LewisTrundle/tactihelm-l5project/timelog.md

# Timelog

* Tactihelm - Adding Haptic Feedback to a Cycling Helmet for Cyclist Safety
* LEWIS TRUNDLE
* 2469635T
* Stephen Brewster

## Week 1 [18/09/2023] - 7 hours
### 19 Sep 23
* *2.5 hours* Started conducting research.
### 20 Sep 23
* *3 hours* Continued with research.
### 21 Sep 23
* *1.5 hours* Continued with research.

## Week 2 [25/09/23] - 10 hours
### 25 Sep 23
* *3.5 hours* Continued with research.
### 26 Sep 23
* *3.5 hours* Continued with research.
### 28 Sep 23
* *1.5 hours* Continued with research.
### 29 Sep 23
* *1.5 hours* First supervisor meeting.

## Week 3 [02/10/23] - 5.5 hours
### 02 Oct 23
* *1 hour* Started constructing the Arduino parts.
### 05 Oct 23
* *1 hour* Structuring project repo.
### 08 Oct 23
* *3.5 hours* Constructing the circuit.

## Week 4 [09/10/23] - 21 hours
### 09 Oct 23
* *7 hours* Created an initial app to Bluetooth control motors on circuit.
### 10 Oct 23
* *1 hours*  Supervisor meeting.
* *1.5 hours* Continued working on app.
### 11 Oct 23
* *1.5 hours* Housekeeping.
### 12 Oct 23
* *4 hours* Setting up Expo app for bluetooth permissions.
### 13 Oct 23
* *6 hours* Connecting the bike radar to react native app via Bluetooth.

## Week 5 [16/10/23] - 29.5 hours
### 16 Oct 23
* *4 hours* Continuing to connect bike radar to react native app.
* *2.5 hours* Creating user survey.
### 17 Oct 23
* *1 hour* Supervisor meeting
* *1 hour* Continuing user survey.
### 18 Oct 23
* *2.5 hours* Finalised user survey.
### 19 Oct 23
* *4.5 hours* Started creating react native app to connect to bluetooth devices.
### 20 Oct 23
* *2 hours* Connecting both devices to app.
* *2 hours* General app work.
### 21 Oct 23
* *4.5 hours* General app work.
### 22 Oct 23
* *5.5 hours* General app work.

## Week 6 [23/10/23] - 17.5 hours
### 23 Oct 23
* *5.5 hours* General app work.
### 24 Oct 23
* *2 hours* Started interim report.
### 27 Oct 23
* *3 hours* General app work.
### 28 Oct 23
* *3 hours* General app work.
* *2 hours* Circuit construction.
### 29 Oct 23
* *2 hours* General app work.

## Week 7 [30/10/23] - 14.5 hours
### 30 Oct 23
* *1 hour* General app work.
* *4 hours* Started on introduction for interim report.
### 31 Oct 23
* *1 hour* Supervisor meeting.
* *1.5 hours* User survey work.
* *1.5 hours* General app work.
### 01 Nov 23
* *2.5 hours* Interim report work.
### 02 Nov 23
* *3 hours* Interim report work.

## Week 8 [06/11/23] - 14 hours
### 06 Nov 23
* *3.5 hours* Interim report work.
### 07 Nov 23
* *0.5 hours* Interim report work.
### 08 Nov 23
* *5 hours* Analysing user survey.
### 09 Nov 23
* *2 hours* Interim report work.
* *1 hours* Refactoring code on app.
### 11 Nov 23
* *2 hours* Continued refactoring code on app.

## Week 9 [13/11/23] - 9.5 hours
### 15 Nov 23
* *4 hours* General app work.
### 16 Nov 23
* *2.5 hours* More general app work.
### 17 Nov 23
* *3 hours* Interim report.

## Week 10 [20/11/23] - 19 hours
### 20 Nov 23
* *5 hours* Interim report.
### 21 Nov 23
* *1.5 hours* Supervisor meeting and prep.
* *2.5 hours* Interim report.
### 22 Nov 23
* *3 hours* Interim report.
### 23 Nov 23
* *3.5 hours* Interim report.
### 24 Nov 23
* *3.5 hours* Interim report.

## Week 11 [27/11/23] - 17 hours
### 28 Nov 23
* *5.5 hours* Interim report.
### 01 Dec 23
* *3.5 hours* Interim report.
### 02 Dec 23
* *6 hours* Interim report.
### 03 Dec 23
* *2 hours* Interim report.

## Week 12 [04/12/23] - 33.5 hours
### 04 Dec 23
* *5 hours* Interim report.
### 05 Dec 23
* *2.5 hours* Interim report.
### 06 Dec 23
* *6.5 hours* Interim report.
### 07 Dec 23
* *6.5 hours* Interim report.
### 08 Dec 23
* *3.5 hours* Interim report.
### 09 Dec 23
* *3 hours* Interim report.
### 10 Dec 23
* *6.5 hours* Interim report.

## Week 13 [11/12/23] - 21 hours
### 11 Dec 23
* *3.5 hours* Interim report.
### 12 Dec 23
* *6 hours* Interim report.
### 13 Dec 23
* *6 hours* Interim report.
### 14 Dec 23
* *4.5 hours* Interim report.
### 04 Dec 23
* *1 hours* Interim report.

## Week 14 [08/01/24] - 16.5 hours
### 08 Jan 24
* *1.5 hours* Housekeeping.
### 09 Jan 24
* *1 hours* Lab-study prep.
### 11 Jan 24
* *6 hours* Updating Arduino-code.
### 12 Jan 24
* *5 hours* Updating Arduino-code.
* *3 hours* Lab-study planning.

## Week 15 [15/01/24] - 14 hours
### 15 Jan 24
* *2 hours* Updating app to work with arduino code
### 18 Jan 24
* *3 hours* Lab-study planning.
### 19 Jan 24
* *5 hours* App work.
### 21 Jan 24
* *4 hours* Lab-study planning

## Week 16 [22/01/24] - 7 hours
### 22 Jan 24
* *2 hours* Lab-study planning.
### 26 Jan 24
* *5 hours* Lab-study planning.

## Week 17 [29/01/24] - 13.5 hours
### 29 Jan 24
* *3 hours* Lab-study planning.
### 01 Feb 24
* *4.5 hours* Lab-study planning.
### 04 Feb 2024
* *6 hours* Lab-study planning.

## Week 18 [05/02/24] - 12.5 hours
### 05 Feb 2024
* *4 hours* Lab-study planning.
### 06 Feb 2024
* *1.5 hours* Conducting lab-study.
* *1 hours* Supervisor meeting.
### 07 Feb 2024
* *3 hours* Conducting lab-study.
### 08 Feb 2024
* *2 hours* Conducting lab-study.
### 09 Feb 2024
* *3 hours* Conducting lab-study.

## Week 19 [12/02/24] - 1.5 hours
### 16 Feb 2024
* *1.5 hours* Conducting lab-study.

## Week 20 [19/02/24] - 18 hours
### 19 Feb 2024
* *3 hours* Conducting lab-study.
* *3 hours* Started analysing results.
### 21 Feb 2024
* *3 hours* Conducting lab-study.
* *3 hours* Started planning user study.
### 23 Feb 2024
* *6 hours* Coding infrastructure for user study.

## Week 21 [26/02/24] - 21 hours
### 27 Feb 2024
* *3 hours* Conducting lab-study.
### 28 Feb 2024
* *4 hours* Conducting lab-study.
### 29 Feb 2024
* *6 hours* Continued with analysis of lab-study results
### 02 Feb 2024
* *8 hours* Further analysis of lab-study.

## Week 22 [04/03/24] - 20 hours
Week was mainly composed of gaining ethical permission of the user-study and redesigning the helmet.

## Week 23 [11/03/24] - 32 hours
Started writing the dissertation and testing the helmet.

## Week 24 [18/03/24] - 20 hours
Conducting user study.

## Week 25 [25/03/24] - 30 hours
Writing dissertation.

## Week 26 [01/04/24] - 40 hours
Writing dissertation.

## Week 27 [08/04/24] - 40 hours
Finishing the project!
