LewisTrundle/tactihelm-l5project/user-study/task-list.md

# TactiHelm User Study: Task List

## Important Information

Before proceeding with any tasks, please ensure you have fully read the [information sheet](./information-sheet.md) and [user manual](../user-guide/user-manual.md).

- If you have opted not to record your GPS data, then please ignore any instructions regarding how to do so.
- Please remember to turn on and off the helmet, bike radar, and headpiece between usage.
- Please ensure your mobile device is near fully charged before commencing your commute.
- If you are okay doing so, for GPS data to be accurately tracked, please ensure battery saving mode on your mobile device is turned off.

## Task List

1. cycle from **work to home** using TactiHelm and performing think-aloud.
2. cycle from **home to work** using TactiHelm and performing think-aloud.
3. complete questionnaire.
4. complete interview and return equipment.
5. cycle from **home to work** normally and complete NASA-TLX questionnaire.

Task 1 will be performed the day you are given TactiHelm. Tasks 2, 3, and 4 will be performed the day after you are given TactiHelm. Task 4 can be performed any day within seven days of performing the previous tasks. Please note that this experiment is not a test of your ability.

## Task 1: First Commute

Your first task is to cycle your normal commute, from your workplace to your residence, whilst using the TactiHelm system. While performing this task, please ensure to perform a think-aloud evaluation, as previously described.

**Before proceeding with Task 1, please carefully read through the [Before Your Commute](../user-guide/user-manual.md#before-your-commute) and [After Your Commute](../user-guide/user-manual.md#after-your-commute) sections of the user manual.**

## Task 2: Second Commute

Your second task is to again cycle your normal commute, this time from your residence to your workplace, whilst using the TactiHelm system. While performing this task, please ensure to perform a think-aloud evaluation, as previously described.

**Before proceeding with Task 2, please carefully read through the [Before Your Commute](../user-guide/user-manual.md#before-your-commute) and [After Your Commute](../user-guide/user-manual.md#after-your-commute) sections of the user manual.**

Once you have completed task 2, please immediately commence to task 3.

## Task 3: Questionnaire

After completion of task 2, your third task is to complete the provided questionnaire.

- [Post-experiment Questionnaire](https://uofg.qualtrics.com/jfe/form/SV_0N8G0Wckys2GCge)

You will be asked a variety of questions regarding your two commutes. Some questions will be regarding both of them, while other questions will only be about your second commute. Please complete this questionnaire as soon as possible after your second commute, so that your experience is still fresh in your mind. Please answer truthfully and honestly.

## Task 4: Interview

After your commutes and completion of the questionnaire, you will be asked to come in for an interview with the evaluator. This will be relatively short (no more than 15 minutes) and is just for us to more deeply understand your experience with TactiHelm.

**Please bring all the equipment with you to return.**

## Task 5: Final Commute and Questionnaire

Your final task is to complete one more commute but without TactiHelm. Please complete this commute within seven days of your interview. Immediately after your commute, we would ask that you complete part of the questionnaire again.

- [Post-experiment Questionnaire](https://uofg.qualtrics.com/jfe/form/SV_0N8G0Wckys2GCge)

Make sure to select the option stating that you have just completed your final commute.
