LewisTrundle/tactihelm-l5project/user-study/participant-brief.md

# TactiHelm User Study: Participant Brief

Hi! Thank you for volunteering to be part of the user-study for our TactiHelm project.

**What is TactiHelm?**
TactiHelm is a smart-helmet which provides vibrotactile feedback to a cyclist warning them of an approaching vehicle. The helmet connects to a bike radar, attached to the rear of a users bike. The radar detects the approaching vehicle and communicates this information to the helmet. The helmet uses this information to activate the vibrational motors inside the helmet - activating them in some pattern, from which the cyclist can interpret information about the approaching vehicle.

**What am I doing here today?**
We would like to evaluate how our developed TactiHelm system works in the real-world. In-order to do this, we need the help of people, such as yourself, who are willing to try on and wear TactiHelm during an actual bike ride. By doing this, we hope to understand how effective our helmet is in warning cyclists of the presence and proximity of approaching vehicles behind them.

**What will I be doing?**
Your participation in this study will take place over the course of today, tomorrow, and one further day. Your primary task will be to simply cycle your commute between your workplace and residence as you normally would, but equipped with the TactiHelm system. We ask that during your commute, you perform a think-aloud evaluation of the system (i.e. say your thoughts out-loud). Further guidance on this will be explained shortly. After the completion of your second commute, you will be asked to complete a questionnaire, followed by a short interview with the evaluator. Finally, we will ask that you complete one more commute between your workplace and residence, without the use of TactiHelm. This will not require a think-aloud evaluation, instead we will ask you to complete a small section of the questionnaire again, after which, your participation in this study is complete, and you will be properly debriefed.

The task list is as follows:

1. cycle from **work to home** using TactiHelm and performing think-aloud.
2. cycle from **home to work** using TactiHelm and performing think-aloud.
3. complete questionnaires and interview and return equipment.
4. cycle from **home to work** normally and complete NASA-TLX questionnaire.

Task 1 will be performed the day you are given TactiHelm. Tasks 2 and 3 will be performed the day after you are given TactiHelm. Task 4 can be performed any day within seven days of performing the previous tasks. Please note that this experiment is not a test of your ability.

**What data will you collect?**

| Data Type | Reason for Collection | Collection Method | Storage | Extra Notes |
|:---:|:---:|:---:|---|---|
| Audio data captured during commute | This will be used to look for any important comments made regarding your experience with TactiHelm | Using a microphone connected to a voice recorder app on your mobile device | This will not be uploaded to anywhere other than the evaluators own personal device, for the sole purpose of analysis | |
| Answers to post-experiment questionnaire | This will be used to gather your subjective opinion on the effectiveness and usability of TactiHelm | Using the online survey platform, Qualtrics | All survey data will be stored anonymously online | |
| Audio from post-experiment interview | This will be used to gather more descriptive data from yourself regarding the effectiveness and usability of TactiHelm | Using a voice recorder app on a mobile device | This will not be uploaded to anywhere other than the evaluators own personal device, for the sole purpose of analysis | |
| GPS data captured during commute | This will be used for purposes such as visualising your commute and comparing general information, such as your commute distance, elevation profile, and time to complete | Using the Ride with GPS app on your mobile device | All GPS data will be kept within the Ride with GPS app and sharing of such data will be kept confidential. Any personal data, such as your actual location will not be used or shared | You may opt out of collection of this data, in which case, we would ask that you provide some general information yourself regarding your commute |

Please note that your data is and will remain completely confidential, and will be used solely for the purpose of this research project. You can of course request that your data be removed at any time, including during or after the study.

**What if I no longer want to participate?**
You are welcome to withdraw from the experiment at any time without prejudice. If you do so, then please note that it will not be possible for you to be debriefed about the purposes of the experiment.

**Can I ask questions?**
Yes, you are free to ask whatever questions you like during the study, and the evaluator will attempt to answer them to the best of their knowledge (so long as it won’t impose on the results of the study). If you have any further questions either during or after the study, please feel free to reach out to [2469635t@student.gla.ac.uk](mailto:2469635t@student.gla.ac.uk).

**Consent**
By continuing with this study, you acknowledge that you have read and understood the above information, and you consent to participate in this study. If you consent to participate in this study, then please follow the link to explicitly give your consent: [User Consent Form](https://uofg.qualtrics.com/jfe/form/SV_24umSauLX1uydtI).
