LewisTrundle/tactihelm-l5project/interim-report/Education Use Consent For Level 5 Projects.docx

Education Use Consent

I hereby grant my permission for my Level 5 Project Final Research Paper and Interim Report to be distributed and shown to other University of Glasgow students and staff for educational purposes.

Name: Lewis Trundle

Student Id: 2469635T

Signature:

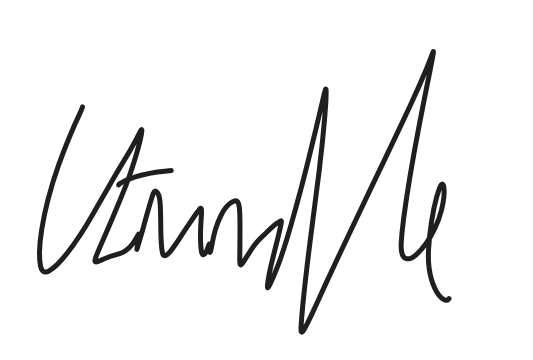
[picture p3: figure]

Date: 15/12/2023
