LewisTrundle/tactihelm-l5project/presentation/TactiHelm.pptx

## TactiHelm: A Vibrotactile Helmet for Cycling Safety

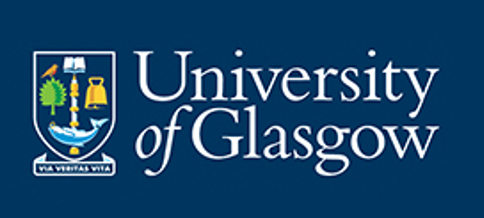
[picture p4: figure]

Lewis Trundle
Level 5 MSci Project
Supervised by Stephen Brewster

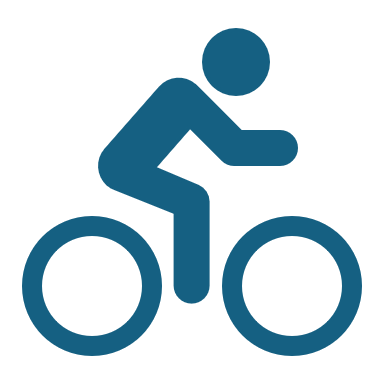
[picture p5: figure]
Bike

## Motivation

41,000 cyclists are fatally injured annually worldwide [1].
Leading cause of fatalities is collisions with other vehicles approaching from behind [2, 3].
Technologies such as bike radars provide unique alerting methods, utilising visual, auditory, and vibrotactile feedback.
Yet to be explored is how the cycling helmet can be used.

Introduction

TactiHelm System

Lab Study

User Study

Conclusions

## Objective

“Develop a vibrotactile helmet-based hazard notification system to effectively warn a cyclist of an approaching vehicle.”

What hazard information is most useful for warning cyclists?
How can this information be encoded using vibrotactile feedback?
How can this be incorporated into a helmet-based display?

Introduction

TactiHelm System

Lab Study

User Study

Conclusions

## Background Survey

An online survey was conducted (N=110) to understand the requirements of such a system.

73% had suffered an injury whilst cycling
80% said that they regularly wear a helmet
10% responded that they own a bike radar.
40% stated that close passes from cars were a top safety challenge while cycling.

Introduction

TactiHelm System

Lab Study

User Study

Conclusions

## The TactiHelm System

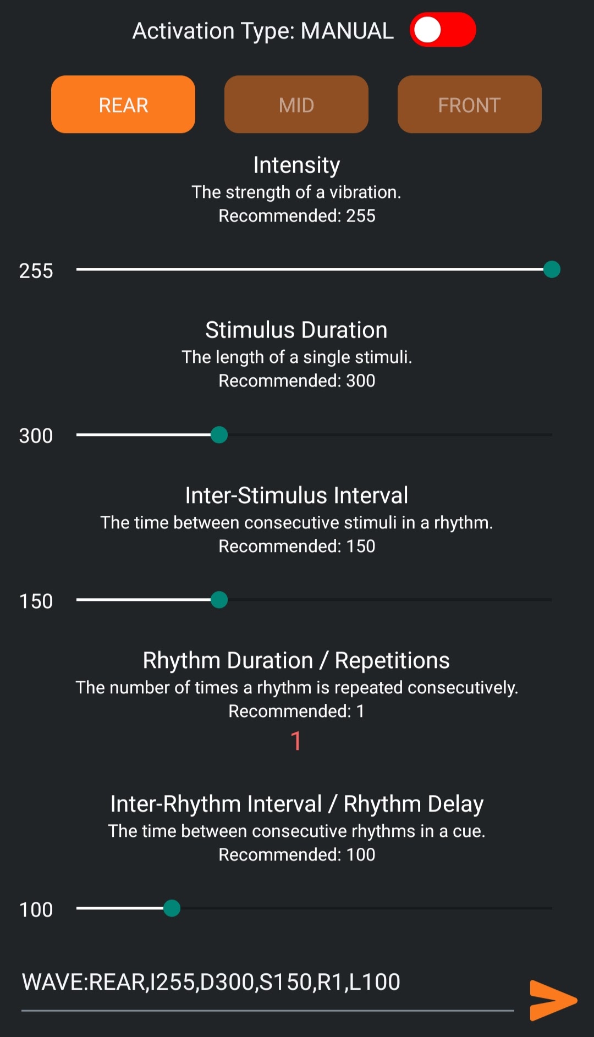
[picture p6: figure]

Controller

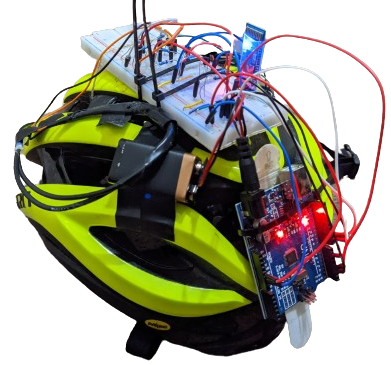
[picture p7: figure]

Helmet

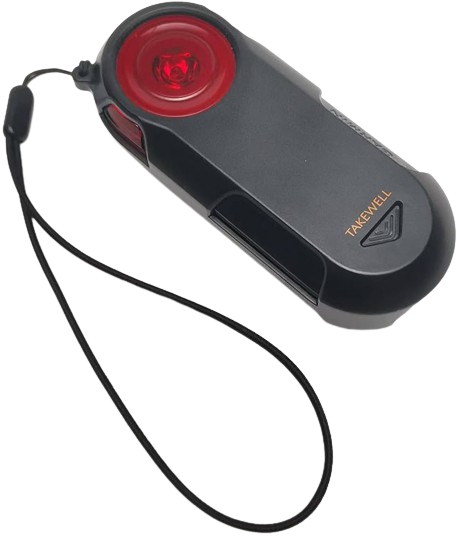
[picture p8: figure]

Bike Radar

Introduction

TactiHelm System

Lab Study

User Study

Conclusions

## Helmet

- Extends a standard cycling helmet.
- 3 internal tactile actuators along sagittal midline.
- Controlled by an Arduino microcontroller.
- Remotely operated via a mobile app.

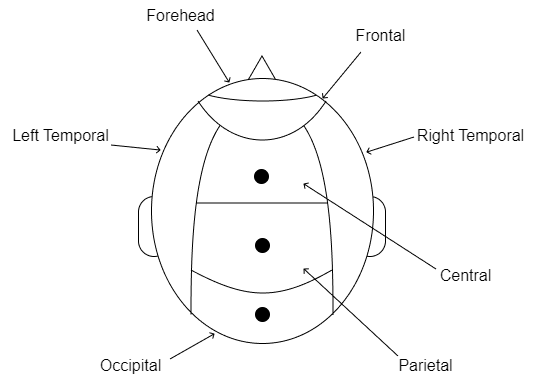
[picture p9: figure]

Introduction

TactiHelm System

Lab Study

User Study

Conclusions

## Bike Radar

- Bike radar detects approaching vehicles’ distance and speed.
- Info sent to the controller app, which calculates the following distance.
- Following distance encoded into vibrational cues: far, near and imminent.
- Following distance thresholds found through preliminary testing.

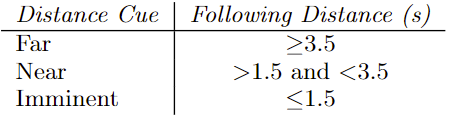
[picture p10: figure]

Introduction

TactiHelm System

Lab Study

User Study

Conclusions

## Controller

- Controller app connects to the helmet and radar – allowing communication between them.
- Parses info received from the radar into relevant instructions for the Arduino.
- Provides manual control over attributes of vibrations, such as location, intensity, etc.

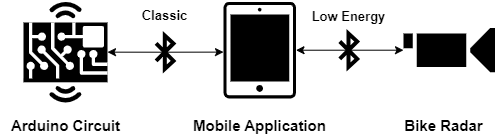
[picture p11: figure]

Introduction

TactiHelm System

Lab Study

User Study

Conclusions

## Lab Study: Investigating Vibrotactile Distance Encodings

Goal:

To investigate how distance can be effectively encoded using vibrotactile cues delivered from a helmet.

RQ1. Is the sagittal plane of the scalp a suitable location for vibrotactile stimulation, for a helmet-based display?
RQ2. Which combination of location- and duration-based encodings are most usable?
RQ3. Which combination of location- and duration-based encodings helps participants make the fewest amount of perception/interpretation errors?

Introduction

TactiHelm System

Lab Study

User Study

Conclusions

Questions:

## Independent Variables: Encoding Schemes

Six encoding schemes were evaluated

Singular Constant
Singular Varying
Wall Constant
Wall Varying
Wave Constant
Wave Varying

Vibration Location
Singular
Wave
Vibration Duration
Constant
Varying
Wall

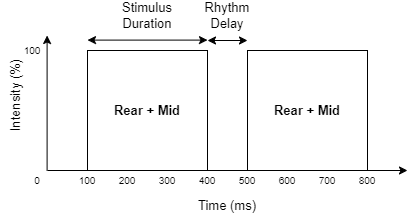
[picture p12: figure]

Example: Wall Varying (Near)

Introduction

TactiHelm System

Lab Study

User Study

Conclusions

## Experiment Design

- Participants evaluated every scheme (within-subjects), in lab-based environment.
- For each scheme, participants received a randomised series of 24 vibrations (8 far, 8 near, 8 imminent) delivered every 5 seconds, followed by post-evaluation questions.
- Dependent measures:
  - Cue Perception: For each vibration, participants recorded the distance cue they believed was conveyed.
    - Stat tests: Two-way repeated-measures ANOVA, followed by pairwise t-tests.
  - Usability: For each scheme, usability was measured using 5-point Likert questions, regarding its: usefulness, distinguishability, interpretability, intuitiveness, and length.
    - Stat test: Friedmans’ ANOVA, followed by pairwise Wilcoxon.

Introduction

TactiHelm System

Lab Study

User Study

Conclusions

## Results: Usability & Cue Perception

Constant vs Varying: All Varying outperformed Constant counterparts for usability and perception.
Within Constant: For usability and perception, Wall was the worst, and Wave was the best.
Within Varying: All varying schemes performed similarly well, with no significant differences.
Perception across cues:
Far: similar across all schemes.
Near & Imminent: Varying schemes performed significantly better than Constant schemes.

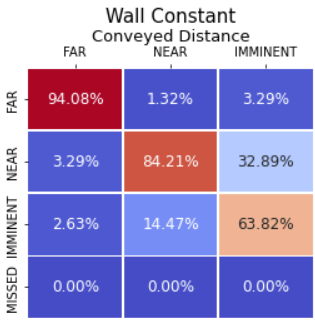
[picture p13: figure]

Introduction

TactiHelm System

Lab Study

User Study

Conclusions

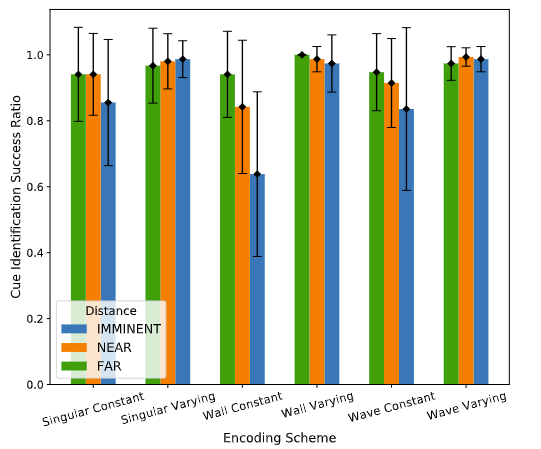
[picture p14: figure]

## Lab Study: Conclusions

- RQ1 (suitability of the head as a vibrotactile display):
  - Linear configuration of tactors along midline of head worked well.
  - Participants wanted a larger gap between the front and middle tactors.
- RQ2&3 (most effective encoding scheme):
  - For both usability and cue perception, all Varying conditions were better than Constant conditions.
    - Likely due to being able to easily count the number of vibrations, from which it is cognitively easier to infer a distance, compared to using an on-body location.
  - The dominant effect of duration makes the location irrelevant, however, there are still notable differences across location schemes.

Introduction

TactiHelm System

Lab Study

User Study

Conclusions

## User Study: Effectiveness of TactiHelm in the Real World

Goal:

Evaluate our developed TactiHelm system in the real-world.

RQ1. Can participants accurately perceive and interpret vibrotactile signals on the scalp whilst cycling?
RQ2. Does the use of TactiHelm improve participants' perceived safety?
RQ3. Is the 3-level categorisation of following distance, suitable for alerting participants of an approaching vehicle?

Introduction

TactiHelm System

Lab Study

User Study

Conclusions

Questions:

## Experiment Design

- We asked commuter cyclists to perform a think-aloud evaluation during their morning commute, using TactiHelm.
- After their commute, they would complete a short questionnaire, followed by an interview.

System Usability Scale (SUS)
NASA-RTLX
Qualitative comments

Introduction

TactiHelm System

Lab Study

User Study

Conclusions

## Results so Far: SUS & NASA-RTLX Totals

SUS

NASA-RTLX

- M=73.5, SD=5.76
- t-test reveals no significant difference from typical benchmark of 68.

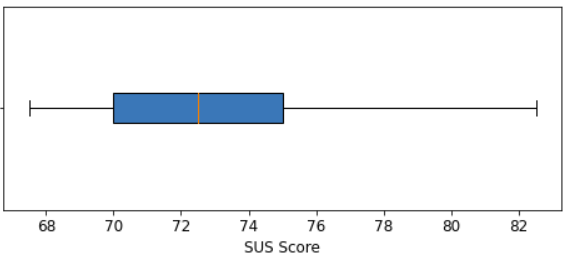
[picture p15: figure]

With TH: (M=42.5, SD=16.67)
Without TH: (M=48.5, SD=10.92)
t-test reveals no significant difference

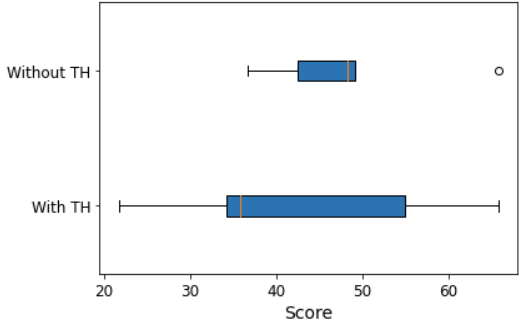
[picture p16: figure]

Introduction

TactiHelm System

Lab Study

User Study

Conclusions

## Results so Far: NASA-RTLX Factors

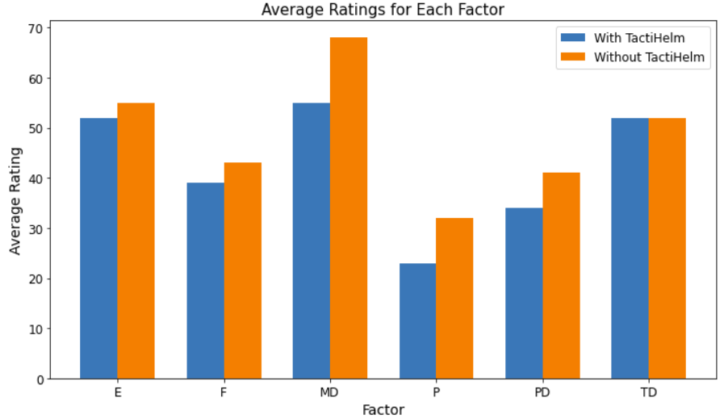
[picture p17: figure]

Introduction

TactiHelm System

Lab Study

User Study

Conclusions

- ‘With TH’ had lower workload across all factors
  - However, no differences were statistically significant.

## Results so Far: Qualitative Comments

Design of the cues made a vehicle really seem like it was approaching

Cue Design

Imminent cue was often delivered too late, and the far cue too early

Cue Delivery

Sometimes required more cognitive effort to interpret

Effort

Reminded you that a vehicle was still there
Could focus more on your surroundings

Effort and Safety

Potential to aid accessibility or to be used for cycling education
Sometimes stopped working

Additional Comments

Introduction

TactiHelm System

Lab Study

User Study

Conclusions

## Conclusions and Future Work

TactiHelm has the potential to improve perceived cycling safety, by giving timely alerts, without distracting the user. However, further work is needed refining the delivery of cues and making the system more robust.

Improve current system: integrate with different bike radars and helmets.
Multimodal: integrate visual and audio cues.
Improve detection and alerting system to be omnidirectional.
Decrease cost by integrating smartphone.

Introduction

TactiHelm System

Lab Study

User Study

Conclusions

## Thank You

Questions?

References:
1. World Health Organization. Global status report on road safety 2018. World Health Organization, 2018
2. Michal Bil, Martina Bilova, and Ivo Muller. Critical factors in fatal collisions of adult cyclists with automobiles. Accident Analysis Prevention, 42(6):1632–1636, 2010.
3. Dovile Adminaite, Richard Allsop, and Graziella Jost. Making walking and cycling on europe’s roads safer. 2015.

## Circuit

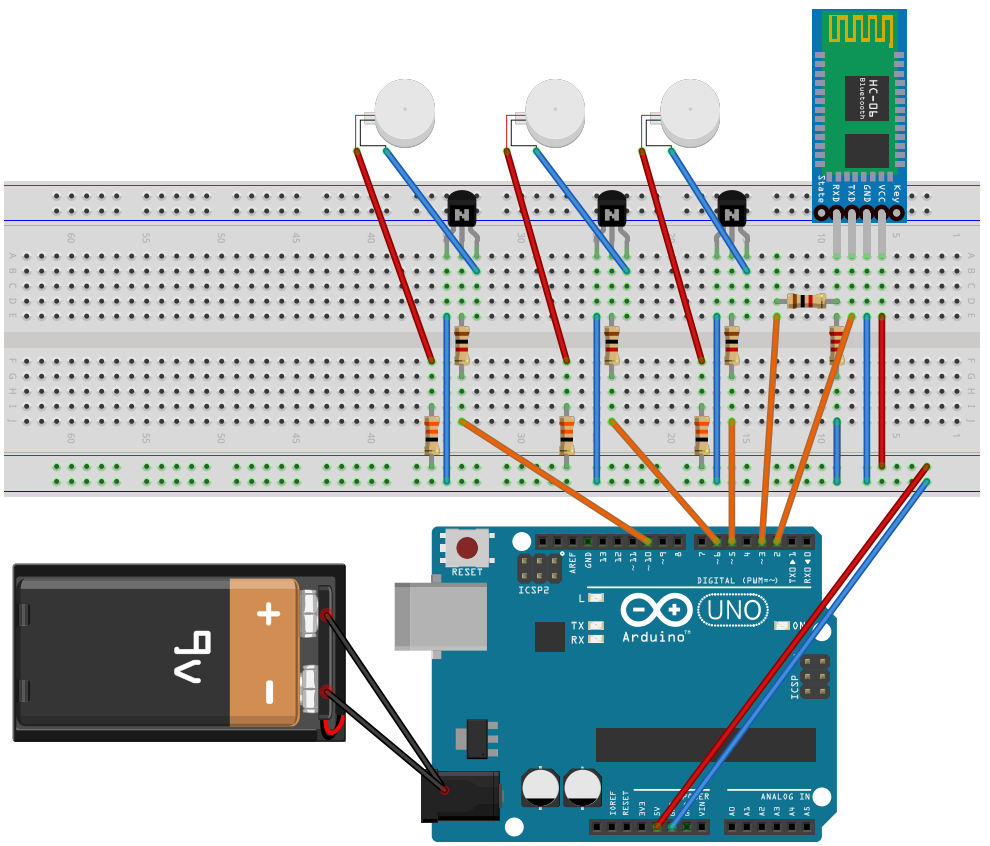
[picture p18: figure]

Version 1

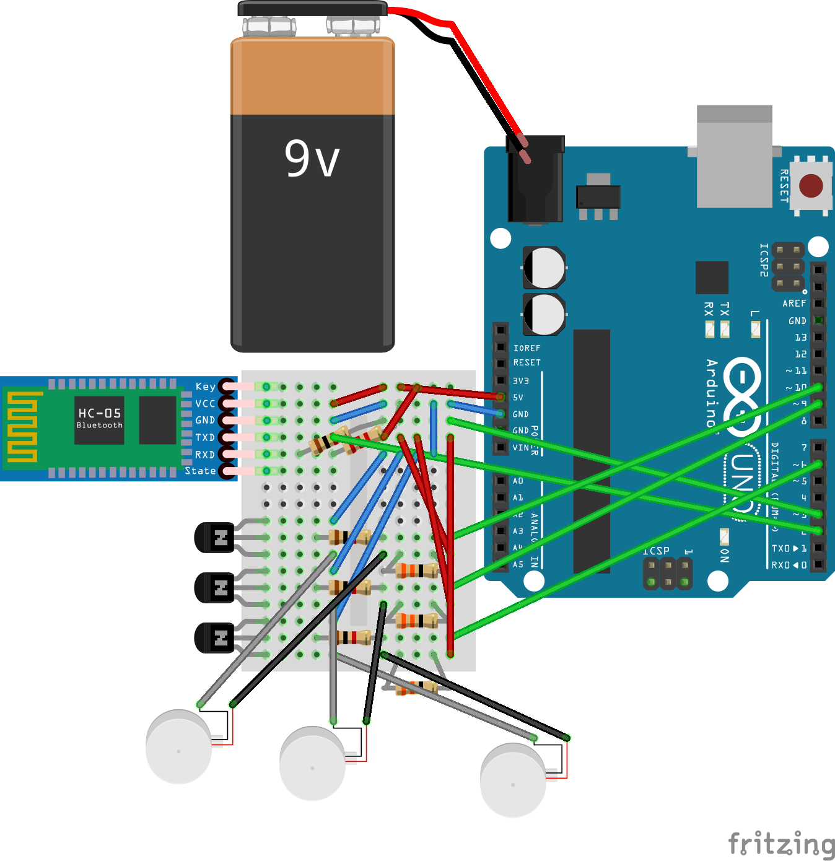
[picture p19: figure]

Version 2

## Lab Study: Stats Tests

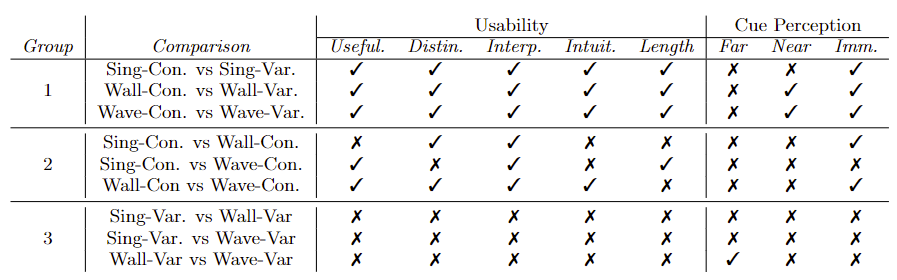
[picture p20: figure]

## Lab Study: Usability

## Lab Study: Recognition Errors

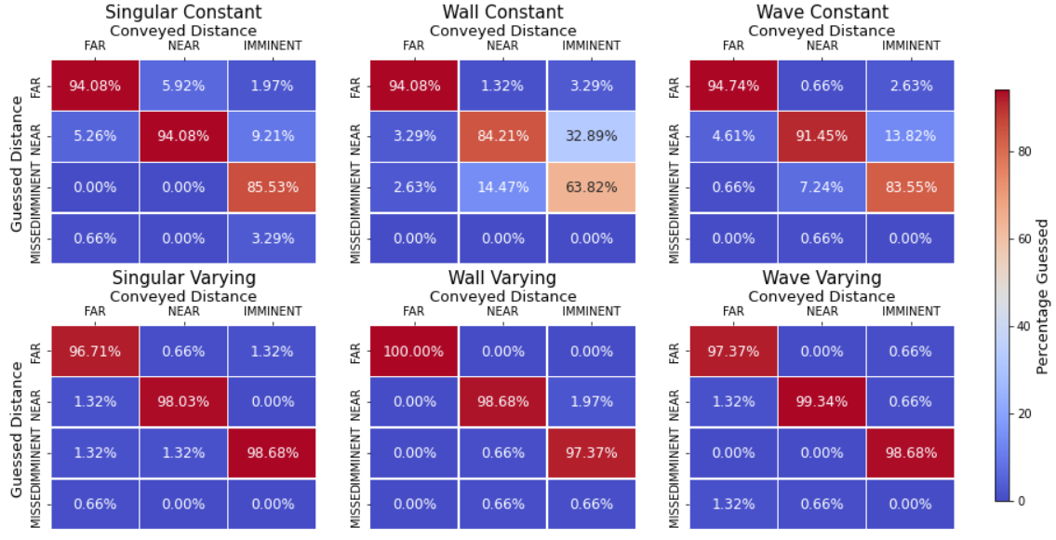
[picture p21: figure]

## Lab Study: Additional Results

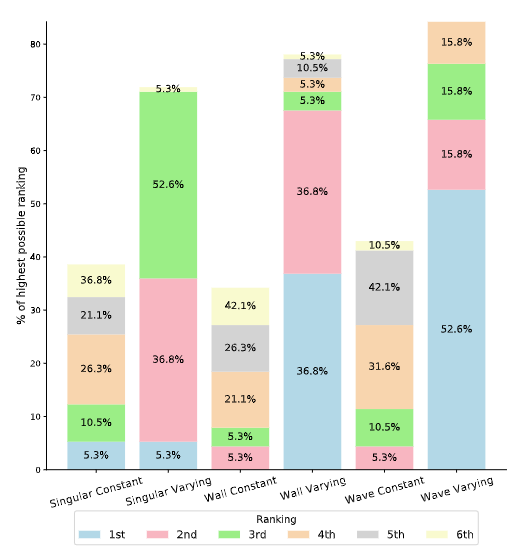
[picture p22: figure]

Scheme Preference

M=7.17/10, SD=2.08
Comments regarding uncomfortable pressure points

Helmet Comfort

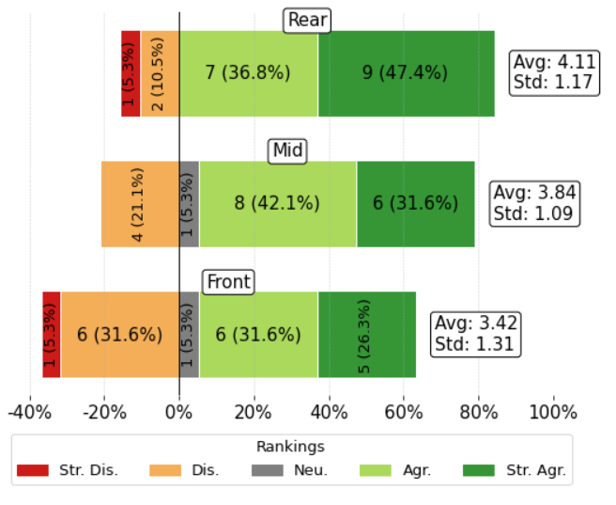
[picture p23: figure]

Tactor Perception

Only 25% knew it was a measure of time and guessed an imminent cue would represent 1-5 seconds.

Understanding of Fol. Dis.

## Example: Near

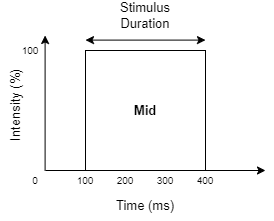
[picture p24: figure]

Singular Constant

Wall Varying

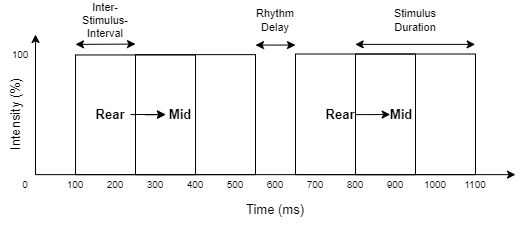
[picture p25: figure]

Wave Varying
