LewisTrundle/tactihelm-l5project/interim-report/2469635t_interim_report.pdf

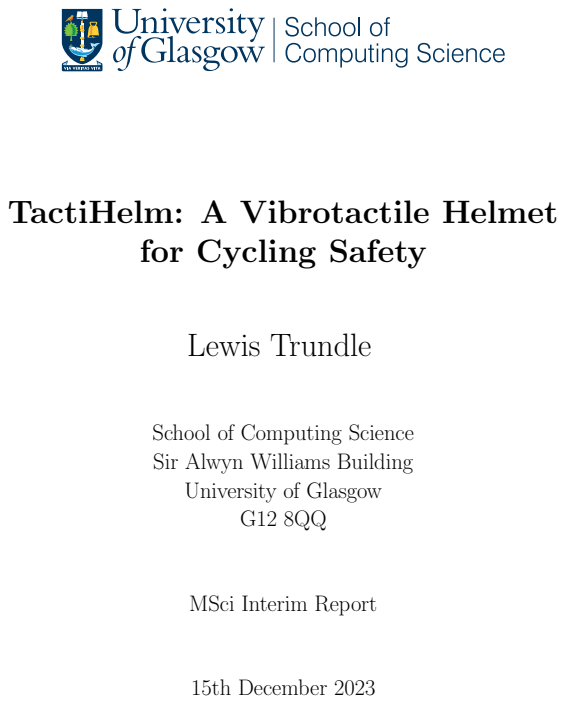
[picture p26: page 1]
Lewis Trundle; 15th December 2023

TactiHelm: A Vibrotactile Helmet

for Cycling Safety

School of Computing Science
Sir Alwyn Williams Building
University of Glasgow

MSci Interim Report

## Contents

1 Introduction | 1
2 Background Survey | 2
3 Proposed Approach | 10

i

4 Work Plan | 19

ii

## 1 Introduction

### 1.1 Motivation

Each year, road-traffic accidents account for 1.35 million deaths worldwide, with cyclists comprising 41,000 of these fatalities [60]. The economic burden associated with road accidents in the EU alone is estimated to amount to 236 billion euros annually [16]. Despite the EU achieving an average annual reduction of 3% in motor vehicle related fatalities, between 2010 and 2018, the fatality rate for cyclists remained the same across that period
[2] - emphasising the lack of attention towards cyclists regarding road safety.

One of the primary causes of cyclist fatalities is collisions with motorised vehicles [13], with 78% of cyclist fatalities in the EU due to bicycle-to-vehicle collisions [1]. Although a collision with another vehicle may occur from any angle, situations where the offending vehicle crashes into the cyclist from behind cause the largest proportion of fatalities of all crash directions [13]. Despite a large body of research investigating how cyclist safety can be improved using safety systems implemented within other road vehicles [68, 70, 15, 40, 48], few studies have explored how cyclist safety can be improved from the perspective of the cyclist [82, 73].

Studies investigating the cognitive demand of cycling has shown that novice cyclists often struggle to accomplish cognitive tasks which are necessary for traffic safety, such as looking for traffic and identifying the type of intersection [86]. To aid cyclists, safety technology such as rear-view bike radars [28] help reduce cognitive load, by delivering warning messages about approaching vehicles both visually and audibly. An obvious benefit of auditory messages is that they do not consume the visual sensory channel. However, auditory messages have been shown to be difficult to understand in noisy environments [20] and in situations such as when the cyclist is listening to music, something which many admit to doing [19].

A possible alternative message modality is vibrotactile. Previous work from Vo et al. [81] explored how this modality can be used for the purpose of cyclist safety, something which no other studies have done as of yet. Regarding where to encode vibrotactile stimulation, there are many options. Previous work have used belts [65, 71, 25], vests [26, 77, 79, 67], and even bicycles [64, 51], as mediums for vibrational stimuli, with products such as attachable handlebar grips which can provide vibrotactile feedback [9]. However, an unexplored area is the potential of the helmet. Few studies have explored how vibrotactile stimuli can be used in helmets [8, 88] and even fewer have investigated how this can be applied in the context of cycling [43].

### 1.2 Problem Statement and Aim

We aim to develop a vibrotactile helmet which can improve cycling safety - helping to lower the number of cyclist fatalities. More specifically, we aim to develop a hazard notification system using vibration for cyclists, able to effectively communicate to the cyclist when a vehicle from behind is approaching.

The system is restricted to the context of notifying of vehicles behind the user, as from our motivation, we identify this as a dangerous situation, with little existing work to aid cyclists in this context. By focusing our system to work in this specific context, we aim to make the most impact in terms of improving cyclist safety.

Regarding developing this system, we first investigate the best metric (or metrics) to convey to a cyclist, to appropriately inform them of approaching vehicles. We hypothesise that this would simply be distance. However, categories of such a metric can be arbitrary - what specific distances do terms such as far or near mean to a cyclist? We hope to distinguish such meanings in this project.

Secondly, we explore how this information can be encoded using vibrotactile cues. This modality is chosen due to its potential to provide feedback with minimal distraction. Therefore, our chosen coding method should be able to accurately represent the appropriate metric, with minimal diversion of the cyclists’ attention. Furthermore, we investigate how this system can be incorporated into a helmet - our chosen medium due to the unexplored potential of bicycle helmets for interaction. We seek to answer which region of the head is best to place vibrotactile motors, and what parameters of the vibrations are most suitable to encode our vibrotactile cues.

Finally, we will evaluate the system in a real-world user study, to learn cyclists’ thoughts regarding its usefulness for cycling in real-life. By testing the system in realistic conditions, we hope to discover if it achieves its purpose of improving cycling safety.

## 2 Background Survey

There is little literature on the use of vibrotactile feedback while cycling, and of the existing corpus, few relate to the problem of cyclist safety. To address this issue, we survey four broad areas of research, and combine the insights we gather to inform our approach to developing TactiHelm. We first examine existing literature regarding in-vehicle hazard notification systems for cyclists. We then explore how different feedback modalities have been used in cycling. Finally, we review the ways in which vibrotactile stimuli can be used to encode information, and how this can be applied to the head.

### 2.1 Hazard Notification for Cyclist Safety

The idea of a hazard notification system was first explored in 1992 by Horowitz and Dingus [35]. They proposed various design approaches, such as adjusting the warning intensity based off the detected collision time, and employing different signal modalities to convey various warning severities - concepts which have been often used in later research. However, it was not until 1996 where one of the earliest hazard detection systems emerged [44]. While not explicitly labelled as a hazard detection system, this project combined radar and vision technologies to create a system which could detect and classify road vehicles ahead of the car, then appropriately change lanes to avoid collision. This idea of detecting vehicles in-front was continued in subsequent research by Huang et al. who developed a warning system which could detect lane boundaries and successfully detect a vehicle in-front with 97% accuracy [37].

These early in-vehicle warning systems are all examples of Intelligent Transport Systems (ITSs) - a series of information and communications technologies which aim to improve the safety of transportation [74]. Despite research into various types of ITSs, few address how the safety of vulnerable road users (VRUs), such as cyclists, can be improved [69]. Silla et al. [70] performed a quantitative safety impact assessment of five different types of ITSs, to evaluate which has the greatest potential to improve cyclist safety. They found that by 2030, the Pedestrian and Cyclist Detection System + Emergency Braking (an in-vehicle system which uses detection sensors to detect pedestrians/cyclists in front of a forward moving vehicle to warn and automatically brake) would have the greatest effect. The PROSPECT project [15], funded by the European Commission, further improves the effectiveness of detection systems. Not only is it able to detect VRUs, but it can also detect their intentions - allowing the vehicle to take pre-emptive measures, such as changing its speed or course, to avoid a collision. This project is estimated to reduce the number of seriously injured people in the EU by anywhere up to 2,500 people by 2030.

Another promising ITS mentioned by Silla et al. [70] is Bicycle to Vehicle communication (B2V) systems. Jenkins et al. created a system which could bring cyclists onto the US Connected Vehicles Program [58] - an initiative designed to bring vehicles onto a Vehicle-to-Everything (V2X) network¹
. This was done by outfitting cyclists with a low-cost DSRC-WAVE²
solution which allowed them to receive basic safety messages. From this, they created a multimodal hazard notification system which would deliver these safety messages using audio and haptic cues. By varying signal parameters, they were able to create a unique vocabulary of cues which cyclists could learn. This was delivered via a standard smartphone speaker and Boreal Bikes’ smrtGRiPs [9]. Although the paper does not describe exactly how these cues were encoded, it does describe the five hazard categories used to decide which action to recommend to the cyclist - ranging from cautionary messages to suggesting immediate action.

Lujic et al. combines the idea of cyclist detection systems and connected networks, to create InTraSafEd5G [48], a system which can predict when pedestrians and cyclists will enter a vehicles’ blind spot at intersections. By installing nodes across various traffic lights around Vienna, the authors create an Edge network which is able to detect critical situations and deliver early warning messages to drivers in real-time using 5G. These warnings are

1The ’Everything’ part of V2X refers to any entity which has an impact or can be impacted by a vehicle. Typically, V2X is a combination of Vehicle-to-Vehicle (V2V) and Vehicle-to-Infrastructure (V2I) networks. In this specific case, Jenkins et al. aims to also include a Vehicle-to-Cyclist (V2C) network.
2Dedicated Short-Range Communications for Wireless Access in Vehicular Environments (DSRC-WAVE) is currently one of the only ways to provide V2X networks, with high reliability and low latency.

delivered both visually and audibly to a driver’s mobile phone. This work highlights the potential of combining various types of ITSs to create a system which enhances cyclist safety. However, the described system only provides a single type of notification to the driver, only alerting them of whether a potential collision is possible. An improved system may deliver different types of notifications which is able to effectively communicate more information about the potential collision.

Despite the potential for improving cyclist safety using ITSs, pre-existing attitudes and perceptions affect the acceptance of such systems. Angelis et al. [17] investigated how attitudes towards cyclists effect how likely a driver is to use an in-vehicle cyclist detection system. They found that drivers who already express a negative representation of cyclists are more unlikely to use a new technology, compared to those who do not. This is further explored by Berge et al. [7] who studied acceptance from the perspective of the cyclist, exploring their beliefs and attitudes towards being equipped with human-machine interfaces (HMIs) for communication with smart-traffic. Through analysis of questionnaire responses and interviews, the authors identified that cyclists were worried about using HMIs as the responsibility of safety would be imposed on themselves, regardless of whether a situation warrants they take immediate action.

### 2.2 Feedback Modalities in Cycling

Wolfe et al. [87] investigated the different types of distractions which cyclists commonly face, finding that auditory distractions were most common, followed shortly by visual ones. Despite little research into ‘distracted biking’ [55] it is generally believed that cyclists’ use of mobile phones is at the root of the cause. Angelis et al. [49] studied the relationship between smartphone usage while cycling and frequency of crashes, finding that the usage of a smartphone led to an increased crash risk. With over half a surveyed population admitting to using their mobile device on every trip [32] and 17% of the population admitting to using one during every ride [31], there have been calls to put legislation in place to prevent the use of smartphones while cycling [61]. However, Angelis et al.’s study found that the link between smartphone usage and increased crash risk was not true for their female subsample, and only applied to their male subset. Although they recommend investigating this further, this finding is also backed by other studies exploring differences in cycling behaviours based on factors such as gender [6]. Furthermore, the authors admit to limitations in their study, such as the unreliability of participants remembering crashes. While some studies have investigated ways to improve smartphone interaction while cycling to reduce distraction [66, 34] other approaches have investigated alternative interaction modalities, which don’t make use of the visual sensory channel.

The concept of utilising different sensory channels to convey information is an idea studied by Wickens [84] and Wickens and Liu [85], who explored ‘Multiple Resource Theory’ - a model of human information processing which predicts that attention is a limited cognitive resource that can be allocated across different tasks and modalities. The model implies that multiple sensory channels can be used simultaneously (within the cognitive load of the individual), without any individual one degrading the processing performance of the human operator. Seeking to take advantage of this concept, Wickens suggests that tasks can be configured to utilise multiple sensory channels - exploiting our information-processing capabilities.

In the context of cycling, multiple works would explore the potential of utilising such a model, by developing tactile displays to aid navigation. One of the earliest instances of this was by Pielot et al. [64] who developed Tacticycle - a bicycle with a minimal set of navigational cues encoded into the handlebars, to guide tourists to points of interests. Direction was encoded via the relative intensity across both handlebars. For example, a 45◦ angle to the right was indicated by 25% intensity vibration in the left handlebar and a 75% intensity vibration in the right. This coding method proved effective, as participants in a study were able to understand the tactile cues and none of them reported losing orientation. However, the authors acknowledge that their testing environment was geographically constraint, and that it was likely participants could find the correct way to their destination as long as they travelled roughly in the right direction. Steltenpohl and Bouwer [71] created Vibrobelt - a vibrotactile belt also developed to aid navigation while cycling . By analysing the visual focus and spatial knowledge acquisition of participants, the authors found that the use of Vibrobelt increased participants ability to recall images from the route, but were generally slower at navigating and recalling the route - showing a lesser contextual understanding. Peeters et al. [62] investigated response times of vibrotactile cues during various levels of physical cycling exercise. By attaching vibrotactile motors to participants’ spine and thighs, they showed that vibrotactile signals were perceivable in both a stationary position, and during diverse levels of physical effort. Furthermore, they showed that cyclists’ reaction time to stimuli shortened as they were cycling with greater effort. However, the study does not investigate the tactile perception of other body parts while cycling, such as the head.

Strohaeker et al. [73] investigated the effect of unimodal warnings on cyclists to prevent collisions, specifically comparing acoustic and vibrotactile warnings. The results found that warnings, especially acoustic, were effective at shortening response times to potential collisions. Though, vibrotactile warnings could also be effective for a system which does not require urgent reactions from the cyclist. This study however, did not consider how multimodal warnings could be used. The effects of unimodal and multimodal cues would be investigated by Matviienko et al. [51, 50] who compared the effectiveness of delivering navigational instructions to child cyclists using visual, auditory, and vibrotactile feedback. Visual and auditory cues were delivered using flashing lights and speakers inside a bicycle helmet, and vibrotactile cues were delivered using the bicycles’ handlebars - similar to Tacticycle [64]. Results from their study showed that unimodal cues were easier to recognise, and so were best used to indicate directions, but multimodal cues were best used to communicate when immediate action is required as it demonstrated shorter reaction times and better understandability. However, due to the sample size and age of the participants, the authors acknowledge that these findings may not be generalisable to the public. These findings are backed by Sawitzky et al. [82, 83] who compared different awareness message modalities for cyclists to avoid dooring - a type of collision where a parked vehicle door suddenly opens onto the path of an incoming cyclist. The authors compared the effectiveness of using combinations of visual messages, auditory icons, and voice messages for delivering warning notifications. The results showed that participants generally preferred the multimodal combination of visual messages and auditory icons. Although the study does not provide any evidence for how tactile feedback could be used, it does suggest it be studied for future work.

Despite the potential of using different communication modalities while cycling, there are drawbacks to each. Waard et al. [19] discovered that 68% of auditory cues were missed when participants were listing to music. Notably, no negative effects towards participants auditory perception were recorded when they only used one earbud. Although Wolfe et al. [87] suggests these effects can be reduced using bone conducing headphones³
, May and
Walker [52] found that when distractor sounds were played through them, a wearers’ ability to localise critical environment sounds worsened. Erdei et al. [23, 22] reported that the perception of vibrotactile signals during cycling worsen in environments where the surface causes haptic interference. However, they suggested this could be overcome by adjusting how the vibrotactile stimuli was delivered to the cyclist. An effective way of delivering stimuli was shown by Tacticyle [64], where they delivered vibrations through the handlebars as they believed, “these are the only parts of the bicycle that the rider constantly touches during the ride”. This statement would be proven correct by Hochleitner et al. [34] who found that cyclists like to keep their hands on the handlebars as much as possible. Furthermore, Porcheron et al. [66] further studied cyclists use of technology while cycling and through findings of an ethnographic study, they introduced the concept that the handlebars are a ‘zonal space’. This alluded to the possibility of expanding the potential stimuli vocabulary, by encoding information across various zones of the handlebars. Companies have even capitalised on the capabilities of the handlebars for vibrotactile feedback, with products such as smrtGRiPs [9] which can be attached to the handlebars of any bicycle.

### 2.3 Coding Information Using vibrotactile Stimuli

### 2.3.1 Coding Direction Using Veridical and Illusionary Stimuli

Much early work utilising vibrotactile stimuli would explore how tactile displays could be incorporated alongside visual displays, to extend a computer systems’ functionality. Tan and Pentland [75], investigated how tactile displays could be used in wearable computing
- suggesting they could be used as directional displays to aid navigation. Ertan et al. [26] would shortly realise this idea of a wearable navigational display less than a year later in 1998, where they developed an adjustable vest which provides directional navigational instructions via vibrations. These directions were conveyed by vibrating a grid of motors -which were sewn into the back of the vest - in a specific pattern. For example, to indicate a right turn, the motors were activated sequentially, from left to right. Research into the design of such a haptic vest would continue over the years, including a study, investigating its efficiency in conveying directional instructions across different gravity conditions [77]. Although the study found that the perceived intensity of vibrotactile signals did not change

3These differ from regular headphones in that, instead of projecting air pressure waves directly into a wearers’ ear, they instead use the cheekbones to transfer auditory signals directly to the cochlea [47].

across the varying conditions, it did comment on the effect that cognitive load has on a persons ability to interpret tactile signals - suggesting the need for further psychophysical experiments investigating haptic perception.

This method of communicating direction makes use of a vibrotactile illusion known as ‘sensory saltation’ - a phenomenon in which successive pulses delivered to equidistant regions of a body part simulate the feeling of movement across the stimulus area [29]. Lederman and Jones [45] and Lee et al. [46] studied different types of sensory illusions, dividing haptic illusions into two types: saltation, and funneling - the illusion of perceiving a single sensation at the centre of two or more simultaneously presented stimuli which are close in proximity. The use of such illusions has the potential to reduce the number of required actuators [42], and earlier studies showed that these illusions are highly robust. Gardner and Spencer
[27] studied funneling, by placing three stimulators spaced 30mm apart on participants forearms and simultaneously activating them. In 80% of the trials, participants reported feeling a stimulation within a 20mm band of the middle stimulator. Cholewiak and Collins
[14] compared the perception of veridical and saltatory sensations. When presenting participants with both types of sensations, the majority of responses reported feeling the same sensation - highlighting the effectiveness of using saltation to mimic veridical signals. However, a study by Peeters et al. [62] contradict these findings. By measuring the perception of vibrotactile signals at the thigh and spine, they showed that illusionary signals were less perceptible than veridical signals, with participants often feeling the individual veridical stimuli during the illusion conditions.

Later studies would often utilise veridical signals for coding direction, such as one conducted by van Erp [79], which used the on-body location of the veridical vibration to indicate the direction of travel. Using a haptic vest similar to Ertan et al. [26], they instead attached motors around the axial (horizontal) plane of the wearers body, allowing directions in a 360◦
circumference to be conveyed. The use of such a coding scheme has the benefit of only requiring a linear array of motors, and would lead to such tactile displays being implemented on smaller wearables, such as belts [65, 71, 25]. Only a small number of studies have investigated how funneling can be use, such as one conducted by Kim et al. [42], who demonstrated how funneling and saltation could be extended to 2D objects to create an ”out of the body” sensation. They attached vibrators to the rear of a mobile device and a phantom sensation was created in the middle area of the phone by varying the relative intensities of vibrations (in the case of funneling) and varying the inter-stimulus intervals (in the case of saltation). Participants were able to feel a phantom sensation in the gap between their two hands holding the mobile device - demonstrating how a greater number of stimulus loci can be created using only a small number of actuators.

### 2.3.2 Coding Distance Using Multiple Parameters

Although a simple navigational system may only convey direction to a user, a more effective one would also typically convey an idea of distance [11]. Parameters to encode information is studied by van Erp, who explores spatial and temporal effects of vibrotactile stimuli [24]. The paper serves as a set guidelines for implementing a vibrotactile system and suggests that a vibrotactile display affords four parameters which can be adjusted: the location, timing, frequency, and amplitude of a vibration. How parameters such as these can be used is described by Brewster and Brown [10], who introduce Tactons - structured, abstract messages, whose meaning is encoded using the parameters of cutaneous perception⁴
. The
authors expand on the parameters suggested by van Erp, explicitly describing how temporal characteristics of a vibration, such as rhythm and duration can be used.

Previous studies have investigated how these parameters can be used to create coding schemes for distance. van Erp et al. [25] investigated the effectiveness of different distance coding schemes to aid navigation for pedestrian participants. Two main categories of distance coding schemes were used; the first was a monotonic relation between distance and rhythm - as the distance got smaller, the rhythm got faster. The second category was a three-phase model, which varied the delay duration between vibration pulses, depending on which phase of the navigation task the participant was in. Navigational directions were encoded by the location of the vibrotactile motors on a belt which participants wore. Notably, there was no difference found in participant performance when comparing those with access to distance information, to those without - concluding that this may be due to the confounding of the distance information with the temporal resolution of the direction information. Straub et al. [72] conducted a similar experiment, also using a vibrotactile belt to perform navigational tasks with pedestrians. Three experiments were preformed to explore how the encoding of distance using the parameters of rhythm, intensity, and frequency, affected the walking speed of participants. Similarly to van Erp et al. [25], no notable differences to walking speed were found. However, this is likely attributable to the confounding of parameters, as both rhythm and intensity are simultaneously varied in the experimental coding schemes.

The inconclusive findings from van Erp et al. [25] and Straub et al. [72] identified a need to further explore how distance can be coded using temporal aspects of vibrotactile stimulation, something which the skin is sensitive to [78]. McDaniel et al. [54] utilised tactile rhythms to create a coding scheme to convey intimate, personal, interpersonal, and social distances to the blind. The duration of a pulse was kept to a constant 50ms, but as the distance increased, the delay between pulses increased, similar to van Erp et al.’s monotonic scheme [25]. However, this experiment proved effective, and showed that given a small training period, users were able to effectively identify different tactile rhythms and associate them with their respective distances. Pielot et al. [63] further studied distance encodings by developing a tactile display which presents the position and distance of other team members in a fast-paced 3D multiplayer game. They compared rhythm-based, duration-based, and intensity-based schemes. Participants found their rhythm-based scheme the easiest to judge distance. Furthermore, they proved it was possible to accurately use vibrotactile signals to convey distance in an environment with high cognitive demand. Asif et al. [5] further studied these parameters, but instead explored how they could be combined to compare three rhythm-based schemes: rhythm only, rhythm and intensity, and rhythm and duration. These schemes were used in-vehicle, to indicate different categories of distance until an approaching turn. The results found that the combination of rhythm

4Cutaneous perception refers to receptors under the surface of the skin. The cutaneous senses are multimodal and includes sensations of temperature, pressure, and vibration.

and duration (where the pulse duration stayed the same but the number of pulses decreased as the distance decreased) was the easiest for participants to learn and led to the smallest amount of navigational mistakes. This finding motivated Prasad et al. [67] to develop HaptiMoto - a wearable vest which provides vibrotactile feedback regarding upcoming turns for motorcyclists. Through a user study, they were able to prove that the rhythm and duration coding scheme for distance, as found by Asif et al. [5], was effective at providing navigational instructions to motorcyclists. However, the authors note that this was only studied at low speeds of below 25 mph.

### 2.4 Vibrotactile Stimulation on the Head

### 2.4.1 Spatial Acuity and the Midline Effect

An early investigation into the spatial acuity of the head was performed by Gilliland and Schlegel [30] who studied localisation ability for various configurations of 4 to 12 tactors placed across the coronal plane of the head. Specifically, tactors were placed across the parietal meridian (from ear to ear). They found that optimal tactile detection and localization accuracy occurred when using six tactors - with a 93% accuracy. More than this, and both the accuracy and reaction time worsened. Myles and Kalb [56] also assessed tactile perception - comparing different regions of the head, using various configurations of eight tactors. They found that the scalp (namely the parietal, central and frontal regions) were the least sensitive loci on the head, whereas, the regions around the axial plane of the head (namely the forehead, occipital, and temple regions) were the most sensitive loci. These different regions can be seen in Figure 3. Myles et al. [57] continued studying how the effects of vibrotactile stimulation varied across regions of the head, by investigating to what effect hair density has on vibration sensitivity. Although known to cause lessened vibrotactile sensitivity, they found that the density of hair on the skin only has a small effect. More so, this effect is confined to only the regions of the head which are the least sensitive.

de Jesus Oliveira et al. [18] studied the spatial resolution of the head, specifically, comparing the more sensitive regions as identified by Myles and Kalb [56]. Namely, the forehead (referred to as frontal in this paper), temporal, occipital, and frontotemporal regions. Although they found that the forehead was the most accurate region for spatial discrimination of vibrotactile stimuli, their results also showed that the centre of the occipital region had high precision. Furthermore, they found that as the distance from the head midline increased, the precision for spatial discrimination decreased - naming this phenomenon as the Midline Effect. Although this was the first direct reporting of this effect, it had been indirectly reported on earlier by van Erp [80] who studied how spatio-temporal characteristics of vibrotactile patterns on the torso effects spatial acuity. He hypothesised multiple reasons for this phenomenon, such as suggesting the body midline is like an anchor point - allowing aid in absolute localization, or that the central nervous system has specific characteristics for processing stimuli. Regardless of the reason, de Jesus Oliveira et al. suggests further research is needed investigating the effect.

### 2.4.2 Tactile Systems for the Head

An early study investigating the role that vibrotactile stimulation can have in a helmet was conducted by Bertram et al. through The Tactile Helmet Project [8]. Vibration actuators were placed around the headband of a helmet, to warn the wearer of imminent collisions and communicate the distance of detected objects. The device is designed with the philosophy of ”active sensing”, where the behaviour of the device changes depending on the context of use. This is accomplished by varying the type and intensity of a vibration by using a context-sensitive algorithm, which takes into account the walking speed of the wearer.

Yamauchi and Suzuki [88] demonstrated how a vibrotactile helmet could be used for hazard notification, specifically, in the context of motorcycling. The location of the vibration on the different regions of the head (the forehead, temporal, and occipital regions) corresponded to the direction of the hazard, whereas the strength of the vibration corresponded to the level of risk. They showed that the use of four directions and three levels of intensity was effective at notifying a wearer of an approaching hazard, even in winds of up to 100km/h.

However, in the context of cycling, the only study to the best of our knowledge which investigates how vibrotactile stimulation around the head can be used, was conducted by Krauß et al. [43]. This study developed a navigational headband which vibrated on the wearers head in the direction of travel - using 12 actuators for a spatial resolution of 30◦ .
They demonstrated that vibrotactile stimulation could be used on the head whilst cycling, without the wearer reporting discomfort or distraction. Although the use of a headband is similar to a helmet, we recognise that no studies have explored how vibrotactile stimulation can be delivered via a helmet to aid cycling.

## 3 Proposed Approach

The following section details each part of the project, describing which stages have been completed, and which stages we are yet to complete. More specifically, it outlines the current implementation of the TactiHelm system, before describing the results from an initial user survey. Finally, it thoroughly describes the plan for two future studies. It is important to note that some details may change in future development of the project.

### 3.1 TactiHelm System Design

### 3.1.1 Circuit Hardware

The current TactiHelm helmet builds off previous work from Vo et al. [81]. The inside lining of the helmet is equipped with 10mm diameter, three volt ERM coin cell tactile actuators (tactors). The exact location, number, and spacing of these tactors is discussed in Section 3.1.5. These actuators are driven by PWM signals from 0 to 3V generated by an

Arduino Uno micro-controller [4], which is powered using a standard 9V battery. PWM can represent the use of an analogue signal [41], allowing us to more precisely vary the range of discrete values used to control the intensity of the tactile actuators. The Arduino Uno has six PWM pins, thus if we wish to vary the intensity of the actuators, we are limited to just six of them. The circuit is also equipped with an HC-06 Bluetooth Module, to allow for remote control over the actuators. This Bluetooth module communicates using Bluetooth Classic [21]. A diagram of the full circuit can be seen in Figure 1.

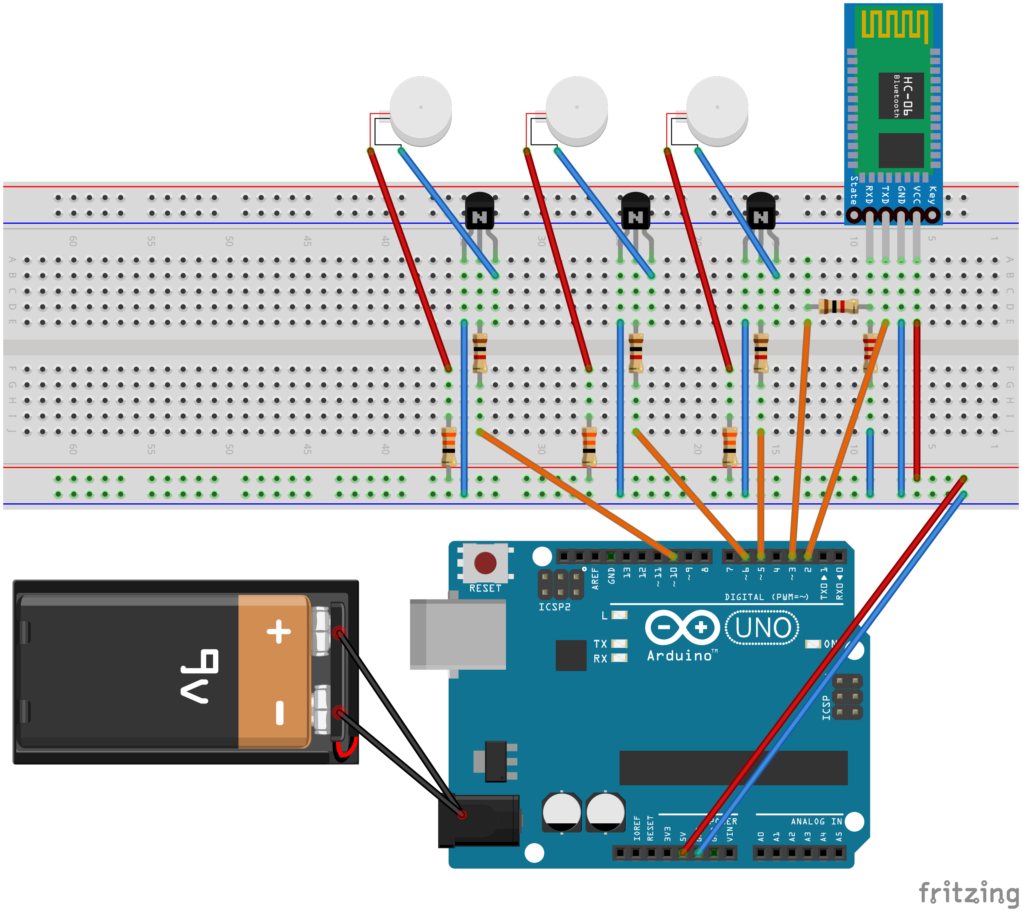
[picture p27: figure]

Figure 1: Figure shows the constructed circuit for TactiHelm. A voltage divider is used to limit the voltage level between the HC-06 Bluetooth Module and the Arduino [3]. The vibration motors require more power than the Arduino pins can provide, so NPN transistors are used to amplify the signal [76].

### 3.1.2 Bike Radar Design

On the other side of the TactiHelm system is the Garmin Varia RTL515 bike radar [28]. Designed to attach to the back of a bicycle, the radar can detect vehicles up to a range of 140 metres, with a viewing angle of 220◦
. The radar allows for two communication methods: Bluetooth Low Energy (BLE) and ANT+. Communicating using BLE provides us with access to the distance and speed of each detected vehicle. Notably, BLE does have limitations such as a smaller bandwidth compared to ANT+ [53]. However, this is not a concern since only a small amount of data is being transferred. From this, the following questions remain:

- Which metric (or metrics), from distance, speed, or some arbitrary combination of the two, is most suitable for signifying an approaching vehicle to a user?
- How can this metric be conveyed to a user? Should continuous values be encoded, or should the metric be defined into categories? What do these arbitrary categories mean to users?
- How can this information be encoded using vibrotactile cues?

To answer the first question, a potential metric for our system is the following distance of the car behind. Typically measured in seconds, the UK Government suggests that vehicles maintain at least a two-second gap from the vehicle in-front [33]. We can quite simply calculate the following distance using the distance and speed given to us by the bike radar. Answers to the other questions are explored with a lab-study investigating different cues and encodings, described in Section 3.3.

### 3.1.3 App Design

To allow communication between the bike radar and Arduino, a custom-built React Native application was developed, to act as an intermediary between the two devices, as seen in Figure 2. The current state of the application can run on an Android mobile phone; however, future versions of the app would ideally also run on an iOS device. Currently, the following functionality is possible with the application:

- Connect to the HC-06 Bluetooth module using Bluetooth Classic
- Connect to the Garmin Varia using Bluetooth Low Energy
- Receive the distance and speed information of each detected vehicle from the bike radar.
- Manually turn on/off and control the vibration intensity of each connected actuator.

What remains to be implemented is a pipeline between the bike radar and Arduino. More specifically, the information received via BLE from the bike radar should be parsed and encoded into the relevant vibrotactile cues. However, this is not possible, until such encodings to cues are defined, as discussed further.

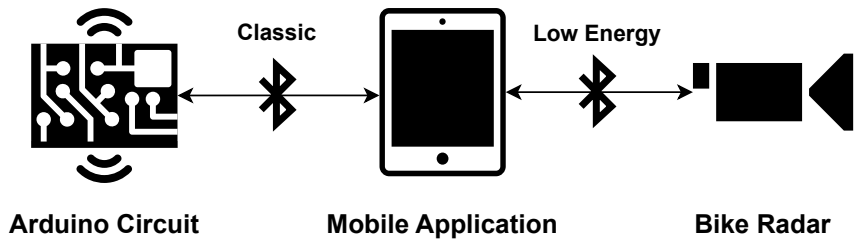
[picture p28: figure]
Classic; Low Energy; Arduino Circuit; Mobile Application; Bike Radar

Figure 2: Figure shows the overall system design. The bike radar communicates to the mobile application using Bluetooth Low Energy, which in turn communicates to the Arduino circuit using Bluetooth Classic.

### 3.1.4 Coding Distance Using Rhythm and Location

As previously mentioned in Section 2.3.2, a vibrotactile display affords four parameters which can be adjusted: the location, timing, frequency, and amplitude of a vibration [24]. In our described system, the ’intensity’ of a vibration is controlled by varying the voltage to the motor using pulse-width-modulation (as described in Section 3.1.1). These changes in voltage results in simultaneous changes in frequency and amplitude, meaning the parameter ’intensity’ is treated as a combination of these two parameters. However, whether these are suitable parameters for our system depends on how many intervals we wish to categorise distance, as frequency and amplitude only have 5-7 perceptually distinguishable levels [24]. From this, and for the sake of simplicity, we choose not to study how the intensity can be varied. Furthermore, it is known that the perception of a stimulus is effected by the waveform [24]. However, the vibration motors which we are using are only capable of producing sine waves, meaning we are limited to this waveform.

This leaves the parameters of location and timing to be used to encode distance. Many studies have investigated how timing (or more specifically, rhythm) can be used to represent different distances [25, 72, 54, 63, 5]. In these studies, the distance is measured from a moving wearer, to a stationary point of interest (POI), where the wearer is moving towards the POI. However, in the context of our described system, the POI (the approaching vehicle) is moving towards the wearer, who is also travelling in the same direction. This motivates the need to study whether typical rhythm coding schemes for distance are still appropriate for use in our described context. Furthermore, no studies to the best of our knowledge have investigated how the location of a vibration can convey distance. This is likely because the location parameter is typically used to convey direction.

From this, we seek to understand how location and/or rhythm of a vibration on a helmet can be used to code distance.

### 3.1.5 Helmet Design and Tactor Placement

A unique feature the use of a helmet affords is the ability to use locations across various anatomical planes. That is, the sagittal, coronal, and axial planes [39]. In the context of vibrotactile systems, motors on a belt-based display [65, 71, 25] would be considered to be along the axial plane, whereas motors on a 2D vest display [26, 77, 79] would be considered to be along the coronal plane. However, few studies have investigated how vibrotactile motors can be used to convey information across the sagittal plane.

By seeking to utilise the sagittal plane of a helmet, we restrict ourselves to linear configurations of tactors, anywhere between the nape and the forehead. These parasagittal configurations may pass through any of the cranial regions, except the temporal. However, as identified by Myles and Kalb [56], regions of the scalp are the least sensitive loci of the head, compared the regions around the axial plane of the head. However, de Jesus Oliveira et al. [18] found that this effect was mitigated when stimuli was presented closer to the midline of the head. Furthermore, they suggested that the center of the occipital region was suitable for conveying warning signals to participants.

For this reason, we restrict our configurations of tactors on the helmet to be linearly placed across the midline of the head, as to maximise perception of stimuli. Although Gilliland and Schlegal [30] found optimal tactile detection and localisation with four or six tactors, we initially set our number of tactors to three, as we hypothesise that no more than three is needed to accurately convey a sense of distance to the wearer. We are still to investigate the exact spacing of these tactors; however, we initially space them roughly 50mm apart. Further investigation into the number and spacing of tactors will be conducted in our lab study as described in Section 3.3. A diagram of the placement of the tactors on the head can be seen in Figure 3.

Forehead

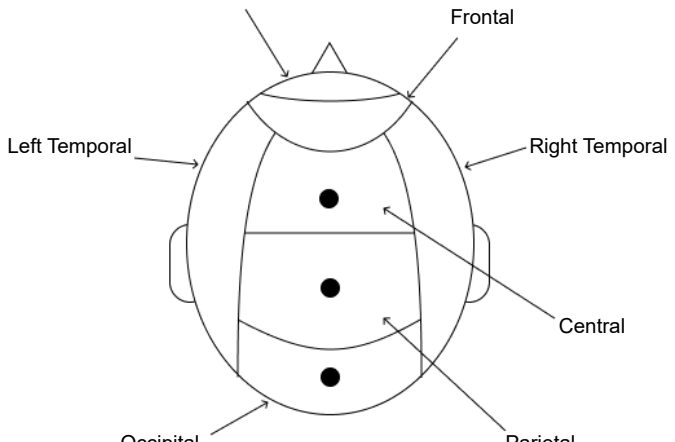
[picture p29: figure]
Frontal; Left Temporal; Right Temporal; Central

Occipital | Parietal

Figure 3: Diagram shows the different regions of the head, as well as the placement of the tactors for our described system.

### 3.2 Exploratory Survey

To identify the requirements of a hazard notification system such as TactiHelm, an online survey was conducted to understand cyclists’ attitudes and behaviours towards safety while cycling. The survey used a mixture of open response, Likert scale, and multiple choice questions to explore topics such as use of safety equipment and techniques and causes of injuries. It was distributed to various cycling groups around Glasgow, and respondents were urged to answer as truthly and honestly as possible. We emphasised that we did not intend to judge any participants’ answers on their safety, legality, or ’sensibility’ - instead we only wish to gather insights for use for the project.

The survey was answered by 110 respondents, aged from 16-24 (14.55%), 25-34 (10.91%), 35-44 (11.82%), 45-54 (31.82%), 55-64 (24.55%) and 65+ (5.45%) years old. Participants identified as 61.82% male, 37.27% female, and 0.91% non-binary. Finally, roughly 90%

of respondents were from Scotland, with the majority from Glasgow. This demographic data was collected as studies has shown that the risk and severity of cyclist injury vary depending on factors such as roadway characteristics and demographic group [6].

90% of respondents answered saying they cycle more than one hour a week, with 42.73% of respondents cycling 7+ hours a week. Respondents equally cycled on city roads (30.37%), cycle paths (29.63%), and country roads (28.15%), with the remaining 11.85% cycling in other environments. Notably, 72.73% of respondents answered that they had suffered some kind of injury while cycling - 60% a minor injury and 12.73% a major injury. Reasons for injury varied, from slipping on wet and uneven roads, to colliding with another road vehicle.

When asked about their usage of a helmet, over 80% of participants stated that they regularly wear one. When asked for reasons for not wearing a helmet, a variety of responses were given, with the most common being that they are not available when hiring a bike. Interestingly, some respondents answered that they did not believe helmets to be useful in certain scenarios, “Helmets are designed to prevent injury at relatively low speeds, speeds which are comfortably exceeded by adult cyclists of even moderate fitness. I believe the effectiveness of helmets to prevent injury is grossly overstated” [P13]. However, multiple studies conducted on the effectiveness of bicycle helmets [59, 38, 36, 12] have found that regardless of the crash severity, helmets can help reduce the severity of head injuries by 48% [38].

When asked about safety technology, the most common equipment following from a helmet were cycle lights (87.27%), reflective gear (64.54%), and bike computers or mounted smartphones (60.90%). Of nine respondents who stated they had a bike radar, all of them said they had a Garmin radar. When asked to comment on its usefulness they all expressed that they benefit from being more aware of vehicles behind them; however, a common disadvantage is its high cost.

Participants were asked to freely respond with the challenges they face which makes cycling feel unsafe. Categorising the responses, the most common ones were “close passes from cars” (38.18%), followed shortly by ”poor cycling infrastructure” (34.54%).

Finally, participants were provided with a brief description of TactiHelm and were invited to comment on its usefulness for cycling. Respondents thought the concept could be useful, but were worried that it may be distracting - expressing concern that it may remain vibrating at all times while a vehicle is detected. These comments are useful in understanding users pre-conceived notions and worries as to how such as system may operate, and help shed light on specific problems which should be addressed in TactiHelm.

### 3.3 Lab Study - Investigating Vibrotactile Distance Encodings

A key idea which remains to be investigated is how distance can be encoded using vibrotactile cues to effectively warn a cyclist of an approaching vehicle. The following section details a future lab-study to be conducted, to explore how distance can be effectively encoded for our system. We categorise distance into three categories: far, near, and imminent. How these terms correspond to real distances is arbitrary, and is something which we hope to understand via this study. Our lab-study presents the opportunity to provide four novel contributions regarding distance encoding schemes.

1. Is the typical use of rhythm to encode distance, a suitable parameter in the context of a hazard awareness system for approaching vehicles from behind?
2. How can the sagittal plane be utilised in a helmet-based vibrotactile display?
3. Is location of a vibration a suitable parameter to encode distance?
4. What real-life distances do cyclists associate with the terms: far, near, and imminent?

### 3.3.1 Subjects and Apparatus

We seek to recruit roughly 10 participants for the study. Although factors such as age and hair density may affect the perception of vibrotactile stimuli, we do not seek to discriminate in this study. The equipment used in this study will be that which is described in Section
3.1. However, vibrotactile cues will be controlled manually through the remote mobile application.

### 3.3.2 Tactile Location and Rhythm Design

Three different location coding schemes for distance have been defined for study. These represent a distance by vibrating any number of the three tactors. These are:

1. Singular Vibration - only the tactor at the location relative to the specified distance is activated.
2. Sequential Synchronous Vibration - all tactors up to the tactor at the location relative to the specified distance are activated at the same time.
3. Sequential Asynchronous Vibration - all tactors up to the tactor at the location relative to the specified distance are activated one at a time in sequential order.

By activation, we refer to a single 1000ms pulse of the tactor of 100% intensity. We set the inter-stimulus interval for the asynchronous condition to 500ms; however, we recognise that this may need further investigation, as discussed in Section 3.3.4. Furthermore, we cannot say for certain which tactors participants will relate to which distance - some participants may believe far should be communicated by activating the tactor at the rear of the head, while others may believe, it should activate the one at the front. Our prediction is given in Section 3.3.4.

Three different rhythm coding schemes for distance have also been defined for study. These are:

1. Monotonic (delay-based) - the activation delay continuously decreases as distance decreases.
2. Categorical (duration-based) - the duration of the rhythm (the number of pulses) decreases as the distance decreases.
3. Hybrid - a multi-phase model, which is categorical while the distance is far, but once a vehicle is imminent, it switches to a monotonic scheme.

With these schemes, only a single tactor is used, specifically, the rear tactor in the occipital region of the head. This is because Myles and Kalb [56] showed that stimulus perception is high in this region. The monotonic encoding is inspired from van Erp et al. [25], who compared different rhythm coding schemes for waypoint navigation. Specifically, an absolute encoding is used, where the delay decreases by a constant amount (compared to a relative encoding which decreases the delay be a percentage of the distance left). The categorical encoding is inspired from Asif et al. [5], who compared different rhythm encodings, finding that participants found the combination of rhythm and duration the best at conveying distance. The hybrid encoding is inspired by Steltenpohl and Bouwer [71], who combined two schemes similar to the described monotonic and categorical ones, to create a two-phase rhythm and duration distance encoding. Although arguably, these rhythm encodings could be further refined into more schemes; for instance, the monotonic scheme could be divided into a relative and an absolute scheme. This is simply meant to serve as an initial study investigating how rhythm can be used to encode distance for a hazard awareness system. Future work would ideally investigate such further refined schemes.

### 3.3.3 Procedure

In the first phase of the study, we seek to gain preliminary insights into our defined coding schemes, by putting the participants through a brief training stage. Participants will be presented with a brief description of TactiHelm, including the location and rhythm schemes which they will be testing. For each scheme, participants will be trained on the different cues. Both during and after this training, participants will be encourage to comment on various factors of the system, such as the number of tactors, and whether they agree with our coding schemes. In the second phase of the study, we seek to gain more quantitative data. Participants will be randomly assigned an order in which they experience the different coding schemes, to control for order effects. They will then be presented with various distance scenarios, and for each scenario, they will be asked to identify the perceived distance as presented by the vibrotactile cue. Participants responses and time taken to respond will be recorded, so that we can compare accuracy and reaction time. After the study, participants will be presented with a brief questionnaire to gather more further qualitative data.

Ideally, we would also like to evaluate schemes which combine both location and rhythm, such as using both the asynchronous location scheme and categorical rhythm scheme. However, further investigation into possible combinations is required.

### 3.3.4 Hypotheses and Predictions

We hypothesise that participants will prefer the asynchronous location scheme, as this utilises the vibrotactile illusion of sensory saltation - proven to be effective [45]. However, this is dependent on whether the size of our inter-stimulus interval is correct, as well as the spacing and number of our tactors. This may require further investigation. Additionally, we predict that participants may experience the illusion of funneling when using the synchronous scheme, due to the simultaneous activation of tactors. Further investigation is required into whether this could be a hindrance, or could be utilised.

We hypothesise that participants will prefer the categorical (duration-based) rhythm scheme, as Asif et al. [5] found the combination of rhythm and duration to work well to convey distance. Finally, we hypothesise that categorising distance into three categories is suitable for our system, and that participants will find it intuitive that the tactor at the back of the head corresponds to a far distance.

### 3.4 User Study - TactiHelm Evaluation

Following from our lab study, we aim to evaluate our fully developed TactiHelm system in a real-world user study. This study aims to assess the usability and effectiveness of the helmet in a naturalistic setting.

### 3.4.1 Subjects and Apparatus

Similarly to the lab study, we seek to recruit roughly 10 participants of any demographic. Although arguably, it may be more beneficial to recruit participants which cycle frequently, TactiHelm should be able to support even novice cyclists. The full TactiHelm system as described in Section 3.1 will be used. Distance will be coded using the best scheme found in the aforementioned lab study. For internal validity, we aim to use the same bike for every experiment. This bike will have a microphone and camera attached, to capture both video and audio footage of participants.

### 3.4.2 Procedure

Participants will undergo a brief training session on how TactiHelm works, and will be given the chance to ask any questions. Their primary task will involve riding the bicycle along a chosen road - once with and once without TactiHelm. The order in which participants do this will be randomised to account for learning order effects. Additionally, participants will be encouraged to think-aloud during the experiment. Afterwards, we will conduct postexperiment interviews and questionnaires with participants. This may include questions from SUS and NASA-TLX questionnaires, so that we can assess participants overall user experience with TactiHelm and whether it had any cognitive effects. Ideally, we would also review video and audio footage obtained from the experiment. There are a number of ways in which this could be analysed, such as comparing the number of times participants turned their heads during both conditions.

Which road this experiment will be performed on is yet to be decided. For validity purposes, it should have a moderate amount of traffic, so that we can perform a realistic evaluation. However, it should not be too busy as to put the participant in danger. Furthermore we still need to obtain ethical permission before performing such an experiment.

## 4 Work Plan

As discussed in the previous section, at the current stage of the project, we have achieved the following:

- Conducted a user survey to gather an initial understanding to cyclists’ thoughts and beliefs regarding safety while cycling.
- Developed a mobile application which can connect to our bike radar and Arduino, and has remote control over each tactile actuator.
- Thoroughly planned two studies to investigate distance coding schemes and then evaluate our finished TactiHelm product.

What remains to be done is to, prepare for, conduct, and then analyse the results of each study. Finally, we then must write our final article. This chapter outlines the intermediate deliverables and dates needed to complete the project. For simplicity, the plan is divided into weekly intervals, between the 8th January and the deadline of April 12th. The whole plan is detailed in a Gantt chart as shown in Figure 4.

The first large stage of work to be completed is the lab study as detailed in Section 3.3. This stage is expected to last from 08/01/24 to 05/02/24. Described below are the intermediate deliverables needed to complete this stage, and their expected dates:

1.1 Prepare materials for study (08/01 - 15/01): before the study can be conducted, we first need to recruit participants, create briefs and debriefs, and plan a space to perform the study, among other preparations.
1.2 Design cues (08/01 - 22/01): the relevant vibrotactile cues to be evaluated in the study need to be designed (as discussed in Section 3.3.3). These should be able to be activated from the mobile app on command.
1.3 Conduct study (22/01 - 29/01): the study can be performed with participants over the course of a week. This task is dependent upon tasks 1.1 and 1.2.
1.4 Analyse results (29/01 - 05/02): the results from the study need to be analysed, inorder to understand which encoding scheme for distance is most suitable. This task is dependent upon task 1.3.

The next large stage is to use the results gathered from the lab study, to design a real-world user study to evaluate our final TactiHelm product. This stage is expected to last from 05/02/24 to 11/03/24. Described below are the intermediate deliverables needed to complete this stage, and their expected dates:

2.1 Prepare materials for study (05/02 - 12/02): before the study can be conducted, we first need to recruit participants, create briefs and debriefs, and plan a space to perform the study, among other preparations.
2.2 Create pipeline from radar to cues (05/02 - 19/02): distance information from the radar should be encoded into the relevant vibrotactile cues using the best coding scheme found in our lab study.
2.3 Additional bug fixing (19/02 - 26/02): extra time is allocated to allow for any potential improvements and changes to be made to the system before the study is conducted. 2.4 Conduct study (26/02 - 04/03): the study can be performed over the course of a week. This is dependent upon tasks 2.1, 2.2, and 2.3.
2.5 Analyse results (04/03 - 11/03): a week is allocated to analyse results to assess the usability and effectiveness of TactiHelm. This task is dependent upon task 2.4.

The final large stage of work to be conducted is to write our final article piece. This stage can run concurrently alongside the other stages, and is expected to last from 12/02/24 to 01/04/24. This provides a buffer period of 11 days for potential changes and problems.

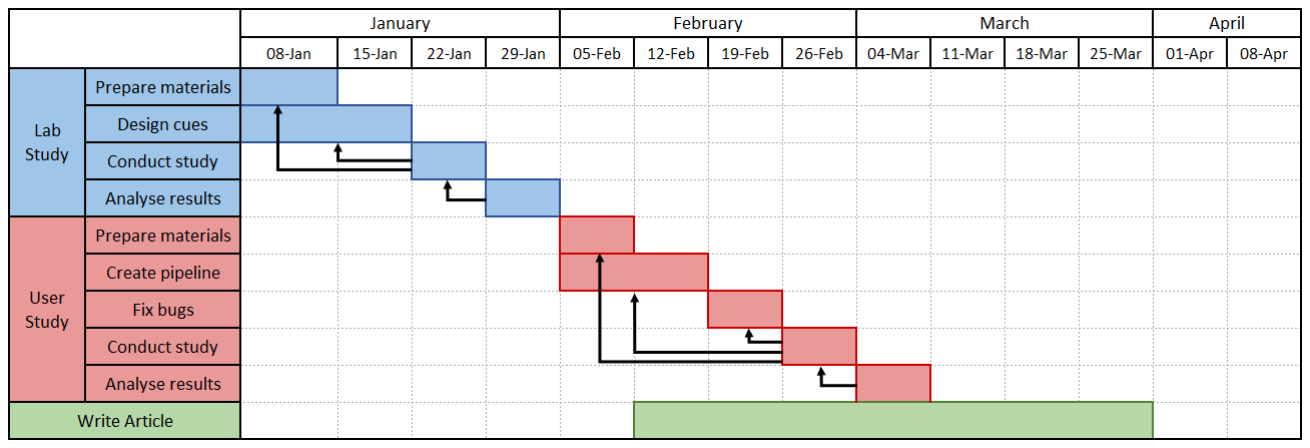
[picture p30: figure]

Figure 4: Figure shows the outlined work plan, visualised as a Gantt chart. Large tasks are divided into smaller deliverables. Time is split into weekly intervals.

## References

[1] Dovile Adminaite, Richard Allsop, and Graziella Jost. Making walking and cycling on europe’s roads safer. 2015.
[2] Dovil´e Adminait´e-Fodor and Graziella Jost. How safe is walking and cycling in europe? pin flash report 38. 2020.
[3] AranaCorp. Arduino and bluetooth module hc-06. https://www.aranacorp.com/en/arduino-and-bluetooth-module-hc-06/. (https://www.aranacorp.com/en/arduino-and-bluetooth-module-hc-06/)
[4] Arduino.cc. Uno r3 arduino documentation. https://docs.arduino.cc/hardware/uno-rev3. (https://docs.arduino.cc/hardware/uno-rev3)

[5] Amna Asif, Wilko Heuten, and Susanne Boll. Exploring distance encodings with a tactile display to convey turn by turn information in automobiles. In Proceedings of the 6th Nordic Conference on Human-Computer Interaction: Extending Boundaries, NordiCHI ’10, page 32–41, New York, NY, USA, 2010. Association for Computing Machinery.
[6] Ali Behnood and Fred Mannering. Determinants of bicyclist injury severities in bicyclevehicle crashes: A random parameters approach with heterogeneity in means and variances. Analytic Methods in Accident Research, 16:35–47, 2017.
[7] Siri Hegna Berge, Marjan Hagenzieker, Haneen Farah, and Joost de Winter. Do cyclists need hmis in future automated traffic? an interview study. Transportation research part F: traffic psychology and behaviour, 84:33–52, 2022.
[8] Craig Bertram, Mathew H. Evans, Mahmood Javaid, Tom Stafford, and Tony Prescott. Sensory augmentation with distal touch: The tactile helmet project. In Nathan F. Lepora, Anna Mura, Holger G. Krapp, Paul F. M. J. Verschure, and Tony J. Prescott, editors, Biomimetic and Biohybrid Systems, pages 24–35, Berlin, Heidelberg, 2013. Springer Berlin Heidelberg.
[9] Boreal Bikes. Garmin varia rtl515. https://www.garmin.com/en-GB/p/698001.
[10] Stephen Brewster and Lorna M. Brown. Tactons: Structured tactile messages for non-visual information display. In Proceedings of the Fifth Conference on Australasian User Interface - Volume 28, AUIC ’04, page 15–23, AUS, 2004. Australian Computer Society, Inc.
[11] GE Burntt and J Mark Porter. Empirical comparison of the use of distance versus landmark information within the human-machine interface for vehicle navigation systems. 2002.
[12] Carlson Moses B¨uth, Natalia Barbour, and Mohamed Abdel-Aty. Effectiveness of bicycle helmets and injury prevention: a systematic review of meta-analyses. Scientific reports, 13(1):8540, 2023.
[13] Michal B´ıl, Martina B´ılov´a, and Ivo M¨uller. Critical factors in fatal collisions of adult cyclists with automobiles. Accident Analysis Prevention, 42(6):1632–1636, 2010.
[14] Roger W Cholewiak and Amy A Collins. The generation of vibrotactile patterns on a linear array: Influences of body site, time, and presentation mode. Perception & Psychophysics, 62:1220–1235, 2000.
[15] Ilona Cieslik, Jordanka Kovaceva, Marie-Pierre Bruyas, David Large, Martin Kunert, Sebastian Krebs, and Martin Arbitmann. Improving the effectiveness of active safety systems to significantly reduce accidents with vulnerable road users-the project prospect (proactive safety for pedestrians and cyclists). 2019.
[16] European Commission, Directorate-General for Mobility, Transport, H Essen, D Fiorello, K El Beyrouty, C Bieler, L Wijngaarden, A Schroten, R Parolin, M Brambilla, D Sutter, S Maffii, and F Fermi. Handbook on the external costs of transport – Version 2019 – 1.1. Publications Office, 2020.
[17] Marco De Angelis, V´ıctor Mar´ın Puchades, Federico Fraboni, Luca Pietrantoni, and Gabriele Prati. Negative attitudes towards cyclists influence the acceptance of an in-vehicle cyclist detection system. Transportation Research Part F: Traffic Psychology and Behaviour, 49:244–256, 2017.

[18] Victor Adriel de Jesus Oliveira, Luciana Nedel, Anderson Maciel, and Luca Brayda. Spatial discrimination of vibrotactile stimuli around the head. In 2016 IEEE Haptics Symposium (HAPTICS), pages 1–6, 2016.
[19] Dick de Waard, Koen Edlinger, and Karel Brookhuis. Effects of listening to music, and of using a handheld and handsfree telephone on cycling behaviour. Transportation Research Part F: Traffic Psychology and Behaviour, 14(6):626–637, 2011. Special Issue: Driving Simulation in Traffic Psychology.
[20] Judy. Edworthy and Elizabeth. Hellier. Auditory warnings in noisy environments. Noise and Health, 2(6):27–39, 2000.
[21] Utmel | Electronic. | Hc-06 | bluetooth | module: | Pinout, | datasheet
pdf | and | arduino | connection. | https://www.utmel.com/components/
hc-06-bluetooth-module-pinout-datasheet-pdf-and-arduino-connection? id=884. (https://www.utmel.com/components/hc-06-bluetooth-module-pinout-datasheet-pdf-and-arduino-connection?id=884)
[22] Jochen Steinmann Elke-Henriette Erdei and Carmen Hagemeister. | Which signal
modalities do cyclists prefer based on experiences in road traffic? | Traffic Injury
Prevention, 22(8):640–645, 2021. PMID: 34709941.
[23] Elke-Henriette Erdei, Jochen Steinmann, and Carmen Hagemeister. Comparing perception of signals in different modalities during the cycling task: A field study. Transportation research part F: traffic psychology and behaviour, 73:259–270, 2020.
[24] Jan Erp. Guidelines for the use of vibro-tactile displays in human computer interaction. Proceedings of Eurohaptics, 2002, 01 2002.
[25] Jan B. F. Van Erp, Hendrik A. H. C. Van Veen, Chris Jansen, and Trevor Dobbins. Waypoint navigation with a vibrotactile waist belt. ACM Trans. Appl. Percept., 2(2):106–117, apr 2005.
[26] S. Ertan, C. Lee, A. Willets, H. Tan, and A. Pentland. A wearable haptic navigation guidance system. In Digest of Papers. Second International Symposium on Wearable Computers (Cat. No.98EX215), pages 164–165, 1998.
[27] Esther P Gardner and W Alden Spencer. Sensory funneling. ii. cortical neuronal representation of patterned cutaneous stimuli. Journal of Neurophysiology, 35(6):954– 977, 1972.
[28] Garmin. smrtgrips. https://smrtgrips.com/.
[29] Frank A Geldard. Sensory saltation: Metastability in the perceptual world. Lawrence Erlbaum, 1975.
[30] Kirby Gilliland and Robert E. Schlegel. Tactile stimulation of the human head for information display. Human Factors, 36(4):700–717, 1994.
[31] C Goldenbeld, M Houtenbos, and E Ehlers. The use of portable media players and mobile phones while cycling: results of a large-scale internet survey. Technical report, 2010.
[32] C. Goldenbeld, M. Houtenbos, E. Ehlers, and D. De Waard. The use and risk of portable electronic devices while cycling among different age groups. Journal of Safety Research, 43(1):1–8, 2012.
[33] National Highways. | National highway urges drivers to use the new two-
second | rule | in | new | campaign. | https://www.gov.uk/government/news/

national-highways-urges-drivers-to-use-the-two-second-rule-in-new-campaign, (https://www.gov.uk/government/news/national-highways-urges-drivers-to-use-the-two-second-rule-in-new-campaign) 2022.
[34] Wolfgang Hochleitner, David Sellitsch, Daniel Rammer, Andrea Aschauer, Elke Mattheiss, Georg Regal, and Manfred Tscheligi. No need to stop: Exploring smartphone interaction paradigms while cycling. In Proceedings of the 16th International Conference on Mobile and Ubiquitous Multimedia, MUM ’17, page 177–187, New York, NY, USA, 2017. Association for Computing Machinery.
[35] Avraham D. Horowitz and Thomas A. Dingus. Warning signal design: A key human factors issue in an in-vehicle front-to-rear-end collision warning system. Proceedings of the Human Factors Society Annual Meeting, 36(13):1011–1013, 1992.
[36] Alena Hoye. Recommend or mandate? a systematic review and meta-analysis of the effects of mandatory bicycle helmet legislation. Accident Analysis Prevention, 120:239–249, 2018.
[37] Shih-Shinh Huang, Chung-Jen Chen, Pei-Yung Hsiao, and Li-Chen Fu. On-board vision system for lane recognition and front-vehicle detection to enhance driver’s awareness. In IEEE International Conference on Robotics and Automation, 2004. Proceedings. ICRA ’04. 2004, volume 3, pages 2456–2461 Vol.3, 2004.
[38] Alena Høye. Bicycle helmets – to wear or not to wear? a meta-analyses of the effects of bicycle helmets on injuries. Accident Analysis Prevention, 117:85–97, 2018.
[39] National Cancer Institute. | Anatomical terminology. | https://training.seer.
cancer.gov/anatomy/body/terminology.html. (https://training.seer.cancer.gov/anatomy/body/terminology.html)
[40] Michael Jenkins, Daniel Duggan, and Alessandro Negri. Towards a connected bicycle to communicate with vehicles and infrastructure : Multimodel alerting interface with networked short-range transmissions (main-st). In 2017 IEEE Conference on Cognitive and Computational Aspects of Situation Management (CogSIMA), pages 1–3, 2017.
[41] Diagram Source Brain Kart. Pulse width modulation. 2001.
[42] Youngsun Kim, Jaedong Lee, and Gerard J. Kim. Extending ”out of the body” tactile phantom sensations to 2d and applying it to mobile interaction. Personal Ubiquitous Comput., 19(8):1295–1311, dec 2015.
[43] Anna-Magdalena Krauß, Dennis Wittchen, Dietrich Kammer, and Georg Freitag. A head-based vibrotactile compass for cyclists. Mensch und Computer 2021-Workshopband, 2021.
[44] D. Langer and T. Jochem. Fusing radar and vision for detecting, classifying and avoiding roadway obstacles. In Proceedings of Conference on Intelligent Vehicles, pages 333–338, 1996.
[45] Susan J. Lederman and Lynette A. Jones. Tactile and haptic illusions. IEEE Transactions on Haptics, 4(4):273–294, 2011.
[46] Hye Jin Lee, Jaedong Lee, Chi Jung Kim, Gerard J. Kim, Eun-Soo Kim, and Mincheol Whang. Brain process for perception of the “out of the body” tactile illusion for virtual object interaction. Sensors, 15(4):7913–7932, 2015.
[47] TS Littler, John J Knight, and PH Strange. Hearing by bone conduction and the use of bone-conduction hearing aids, 1952.

[48] Ivan Lujic, Vincenzo De Maio, Klaus Pollhammer, Ivan Bodrozic, Josip Lasic, and Ivona Brandic. Increasing traffic safety with real-time edge analytics and 5g. In Proceedings of the 4th International Workshop on Edge Systems, Analytics and Networking, EdgeSys ’21, page 19–24, New York, NY, USA, 2021. Association for Computing Machinery.
[49] V´ıctor Mar´ın Puchades Gabriele Prati Marco De Angelis, Federico Fraboni and Luca Pietrantoni. Use of smartphone and crash risk among cyclists. Journal of Transportation Safety & Security, 12(1):178–193, 2020.
[50] Andrii Matviienko, Swamy Ananthanarayan, Shadan Sadeghian Borojeni, Yannick Feld, Wilko Heuten, and Susanne Boll. Augmenting bicycles and helmets with multimodal warnings for children. In Proceedings of the 20th International Conference on Human-Computer Interaction with Mobile Devices and Services, MobileHCI ’18, New York, NY, USA, 2018. Association for Computing Machinery.
[51] Andrii Matviienko, Swamy Ananthanarayan, Abdallah El Ali, Wilko Heuten, and Susanne Boll. Navibike: Comparing unimodal navigation cues for child cyclists. In Proceedings of the 2019 CHI Conference on Human Factors in Computing Systems, CHI ’19, page 1–12, New York, NY, USA, 2019. Association for Computing Machinery.
[52] Keenan R May and Bruce N Walker. The effects of distractor sounds presented through bone conduction headphones on the localization of critical environmental sounds. Applied ergonomics, 61:144–158, 2017.
[53] S. McClain. What are the limitations of bluetooth? https://www.techwalla.com/articles/what-are-the-limitations-of-bluetooth, (https://www.techwalla.com/articles/what-are-the-limitations-of-bluetooth) 2017. Last accessed: 2023-03-21.
[54] Troy L. McDaniel, Sreekar Krishna, Dirk Colbry, and Sethuraman Panchanathan. Using tactile rhythm to convey interpersonal distances to individuals who are blind. In CHI ’09 Extended Abstracts on Human Factors in Computing Systems, CHI EA ’09, page 4669–4674, New York, NY, USA, 2009. Association for Computing Machinery.
[55] Judith L Mwakalonge, Jamario White, and Saidi Siuhi. Distracted biking: a review of the current state-of-knowledge. International Journal of Traffic and Transportation Engineering, 3(2):42–51, 2014.
[56] Kimberly Myles and Joel Kalb. Guidelines for head tactile communication. page 34, 03 2010.
[57] Kimberly Myles, Joel T. Kalb, Janea Lowery, and Bheem P. Kattel. The effect of hair density on the coupling between the tactor and the skin of the human head. Applied Ergonomics, 48:177–185, 2015.
[58] United States Department of Transportation. Us connected vehicles program. https://www.its.dot.gov/research_archives/connected_vehicle/connected_vehicle.htm. (https://www.its.dot.gov/research_archives/connected_vehicle/connected_vehicle.htm)
[59] Jake Olivier and Prudence Creighton. Bicycle injuries and helmet use: a systematic review and meta-analysis. International Journal of Epidemiology, 46(1):278–292, 07 2016.
[60] World Health Organization. Global status report on road safety 2018. World Health Organization, 2018.

[61] Mary O’Connor. Ban cyclists and e-scooter riders using phones, tory peer urges. https://www.bbc.co.uk/news/uk-politics-61018584, 2022.
[62] Thomas Peeters, Eric Van Breda, Wim Saeys, Evi Schaerlaken, Jochen Vleugels, Steven Truijen, and Stijn Verwulgen. Vibrotactile feedback during physical exercise: perception of vibrotactile cues in cycling. International Journal of Sports Medicine, 40(06):390–396, 2019.
[63] Martin Pielot, Oliver Krull, and Susanne Boll. Where is my team: Supporting situation awareness with tactile displays. In Proceedings of the SIGCHI Conference on Human Factors in Computing Systems, CHI ’10, page 1705–1714, New York, NY, USA, 2010. Association for Computing Machinery.
[64] Martin Pielot, Benjamin Poppinga, Wilko Heuten, and Susanne Boll. Tacticycle: Supporting exploratory bicycle trips. In Proceedings of the 14th International Conference on Human-Computer Interaction with Mobile Devices and Services, MobileHCI ’12, page 369–378, New York, NY, USA, 2012. Association for Computing Machinery.
[65] Benjamin Poppinga, Martin Pielot, and Susanne Boll. Tacticycle: A tactile display for supporting tourists on a bicycle trip. In Proceedings of the 11th International Conference on Human-Computer Interaction with Mobile Devices and Services, MobileHCI ’09, New York, NY, USA, 2009. Association for Computing Machinery.
[66] Martin Porcheron, Leigh Clark, Stuart Alan Nicholson, and Matt Jones. Cyclists’ use of technology while on their bike. In Proceedings of the 2023 CHI Conference on Human Factors in Computing Systems, CHI ’23, New York, NY, USA, 2023. Association for Computing Machinery.
[67] Manoj Prasad, Paul Taele, Daniel Goldberg, and Tracy A. Hammond. Haptimoto: Turn-by-turn haptic route guidance interface for motorcyclists. In Proceedings of the SIGCHI Conference on Human Factors in Computing Systems, CHI ’14, page 3597–3606, New York, NY, USA, 2014. Association for Computing Machinery.
[68] Johan Scholliers, Daniel Bell, Andrew Morris, and Alejandra B Garcia-Melendez. Potential of its to improve safety and mobility of vrus. 2014.
[69] Johan Scholliers, Daniel Bell, Andrew Morris, and Alejandra B. Garcia-Melendez. Potential of ITS to improve safety and mobility of VRUs. 6 2017.
[70] Anne Silla, Lars Leden, Pirkko R¨am¨a, Johan Scholliers, Martijn Van Noort, and Daniel Bell. Can cyclist safety be improved with intelligent transport systems? Accident Analysis Prevention, 105:134–145, 2017. Improving cyclist safety through scientific research, ICSC2015.
[71] Haska Steltenpohl and Anders Bouwer. Vibrobelt: Tactile navigation support for cyclists. In Proceedings of the 2013 International Conference on Intelligent User Interfaces, IUI ’13, page 417–426, New York, NY, USA, 2013. Association for Computing Machinery.
[72] Markus Straub, Andreas Riener, and Alois Ferscha. Distance encoding in vibro-tactile guidance cues. In 2009 6th Annual International Mobile and Ubiquitous Systems: Networking Services, MobiQuitous, pages 1–2, 2009.
[73] Elke Henriette Strohaeker, Alessandro Moia, Jochen Steinmann, and Carmen Hagemeister. How do warnings influence cyclists’ reaction to conflicts? comparing acoustic and vibro-tactile warnings in different conflicts on a test track. Transportation Research Part F: Traffic Psychology and Behaviour, 90:151–166, 2022.
[74] Rachel Finson Susan A. Shaheen. Intelligent transportation systems. Encyclopedia of Energy, pages 487–496, 2004.
[75] H.Z. Tan and A. Pentland. Tactual displays for wearable computing. In Digest of Papers. First International Symposium on Wearable Computers, pages 84–89, 1997.
[76] techZeero. Vibration motor with arduino - code, circuit for vibration motor. https: //techzeero.com/arduino-tutorials/vibration-motor-with-arduino/.
[77] R. Traylor and H.Z. Tan. Development of a wearable haptic display for situation awareness in altered-gravity environment: some initial findings. In Proceedings 10th Symposium on Haptic Interfaces for Virtual Environment and Teleoperator Systems. HAPTICS 2002, pages 159–164, 2002.
[78] Jan B F van Erp and Peter J Werkhoven. Vibro-tactile and visual asynchronies: Sensitivity and consistency. Perception, 33(1):103–111, 2004. PMID: 15035332.
[79] Jan BF van Erp. Tactile navigation display. In International Workshop on Haptic Human-Computer Interaction, pages 165–173. Springer, 2000.
[80] J.B.F. van Erp. Vibrotactile spatial acuity on the torso: effects of location and timing parameters. In First Joint Eurohaptics Conference and Symposium on Haptic Interfaces for Virtual Environment and Teleoperator Systems. World Haptics Conference, pages 80–85, March 2005.
[81] Dong-Bach Vo, Julia Saari, and Stephen Brewster. Tactihelm: Tactile feedback in a cycling helmet for collision avoidance. In Extended Abstracts of the 2021 CHI Conference on Human Factors in Computing Systems, CHI EA ’21, New York, NY, USA, 2021. Association for Computing Machinery.
[82] Tamara von Sawitzky, Thomas Grauschopf, and Andreas Riener. Hazard notifications for cyclists: Comparison of awareness message modalities in a mixed reality study. In 27th International Conference on Intelligent User Interfaces, IUI ’22, page 310–322, New York, NY, USA, 2022. Association for Computing Machinery.
[83] Tamara von Sawitzky, Thomas Grauschopf, and Andreas Riener. ldquo;attention! a door could open.rdquo;mdash;introducing awareness messages for cyclists to safely evade potential hazards. Multimodal Technologies and Interaction, 6(1), 2022.
[84] C Wickens. Processing resources and attention, varieties of attention. R. Parasuraman and D. Davis, Eds. Academic Press, 1984.
[85] Christopher D. Wickens and Yili Liu. Codes and modalities in multiple resources: A success and a qualification. Human Factors, 30(5):599–616, 1988. PMID: 3220489.
[86] M. Wierda and K. A. Brookhuis. Analysis of cycling skill: A cognitive approach. Applied Cognitive Psychology, 5(2):113–122, 1991.
[87] Elizabeth Suzanne Wolfe, Sandra Strack Arabian, Janis L Breeze, and Matthew J Salzler. Distracted biking: an observational study. Journal of trauma nursing: the official journal of the Society of Trauma Nurses, 23(2):65, 2016.
[88] Yuta Yamauchi and Akimasa Suzuki. Vibro-tactile notification in different environments for motorcyclists. no. c, pages 59–65, 2020.
