LewisTrundle/tactihelm-l5project/dissertation/tactihelm_l5project.pdf

# TactiHelm: A Vibrotactile Helmet for Cycling Safety

## Lewis Trundle (2469635t)

## April 12, 2024

## ABSTRACT

Despite significant advancements in motor-vehicle safety, such progress has not yet extended to cyclists, who continue to suffer thousands of fatal injuries annually worldwide, often due to collisions with road vehicles approaching from behind. Typical cyclist safety technologies rely on visual and auditory alerts for approaching vehicles, however, these sensory channels are often already in use whilst cycling. Vibrotactile stimulation offers a suitable alternative. Despite much prior work investigating methods for delivering vibration stimuli, few have explored how this can be used for cycling safety. In response, we continue previous work to develop TactiHelm: a vibrotactile, helmet-based, hazard-notification system, which can effectively warn a cyclist of vehicles approaching from behind. We combined a commercial bike radar with a modified cycling helmet to detect and convey distance information for approaching vehicles, using tactile actuators placed along the sagittal midline of the helmet. We conducted a study investigating how distance information can be encoded using the pattern and duration of a vibrotactile cue. Results showed that encoding schemes which vary the number of cue deliveries, led to a significantly higher percentage of correctly interpreted cues. Furthermore, participants preferred tactile patterns which create a sensation of movement across the scalp. TactiHelm was shown to be effective in real life, with commuter cyclists reporting its usefulness in portraying the approach of a vehicle, without consuming their sight or hearing, making them feel safer.

## 1. INTRODUCTION

Each year, road-traffic accidents account for 1.35 million deaths worldwide, with cyclists comprising 41,000 of these fatalities [58]. The economic burden associated with road accidents in the EU alone is estimated to amount to 236 billion euros annually [17]. Despite the EU achieving an average annual reduction of 3% in motor vehicle related fatalities between 2010 and 2018, the fatality rate for cyclists remained the same across that period [2] - emphasising the lack of attention towards cyclists regarding road safety. One of the primary causes of cyclist fatalities is collisions with motorised vehicles [14], with 78% of cyclist fatalities in the EU due to bicycle-to-vehicle collisions [1]. Although a collision with another vehicle may occur from any angle, situations where the offending vehicle crashes into the cyclist from behind cause the largest proportion of fatalities of all crash directions [14]. Despite a large body of research investigating how cyclist safety can be improved using safety systems implemented within other road vehicles [66, 68, 16, 40, 48], few studies have explored how cyclist safety can be improved from the perspective of the cyclist [77, 72].

Studies investigating the cognitive demand of cycling has shown that novice cyclists often struggle to accomplish the cognitive tasks which are necessary for traffic safety, such as looking for traffic and identifying the type of intersection [81]. To aid cyclists, safety technology such as rear-view bike radars [28] help reduce cognitive load, by delivering warning messages about approaching vehicles both visually and audibly, without the cyclist having to shoulder check, which takes their eyes of the road ahead. However, auditory messages have been shown to be difficult to understand in noisy environments [21] and in situations such as when the cyclist is listening to music, which many admit to doing [20]. A possible alternative message modality is vibrotactile stimulation. Many previous works have explored different methods for delivering vibrational stimuli, utilising belts [70, 26], vests [64], and even bicycles themselves [62, 51]. However, an unexplored area is the potential of the helmet. Few studies have explored how vibrotactile stimuli can be used in helmets [9, 83] and even fewer have investigated how this can be applied in the context of cycling [43].
In this paper, we continue previous work from Vo et al. [76], to develop TactiHelm: a vibrotactile, helmet-based, hazard-notification system, which can effectively warn a cyclist of vehicles approaching from behind. The system utilises a commercial bike radar to detect the distance and speed of approaching vehicles from behind the cyclist, which is subsequently conveyed to them using vibrotactile feedback delivered to the head. The TactiHelm system aims to improve cycling safety, by alerting the cyclist of potential collisions through their tactile sensory channel, as opposed to potentially distracting visual or auditory methods - helping reduce the cognitive demand required of the cyclist. Through development of this system, we define and investigate two primary research questions:
RQ1: How can meaningful information about an approaching vehicle be encoded using vibrotactile feedback delivered from a helmet? The amount of information that a vibrotactile display can effectively convey is limited by the number of perceptually distinguishable levels afforded by the parameters of the system [25]. This is subsequently limited by the on-body location of where these stimuli are delivered. Therefore, we consider how information about an approaching vehicle, such as its distance and speed, can be quantised and represented using vibrotactile stimulation. Furthermore, we investigate what parameters of a helmet-based vibrotactile display, are most suitable for encoding this information.
RQ2: Is our developed TactiHelm system effective for warning cyclists in real-world scenarios? For our system to be effective, people must be able to accurately perceive and interpret our defined vibrotactile cues on their scalp whilst

1

cycling. Furthermore, these cues must be meaningful, and should help improve perceived safety. Therefore, we assess TactiHelm using a real-world user study, where participants evaluate the system in realistic traffic conditions.

## 2. BACKGROUND

Little literature exists on the use of vibrotactile feedback for cycling, and of the existing corpus, few relate to the problem of cyclist safety. To address this issue, we survey four broad areas of research, and combine the insights we gather to inform our approach to developing TactiHelm. We first examine existing literature regarding hazard notification systems for cyclist safety. We then explore how different feedback modalities have been used in cycling. Finally, we review ways in which vibrotactile stimuli can be used to encode information, and how this can be applied to the head.

## 2.1 Hazard Notification for Cyclist Safety

Hazard notification systems were first explored by Horowitz and Dingus [35], who proposed ideas, such as varying the warning intensity based off the detected collision time, and using different signal modalities to convey various warning severities. These concepts have been used often in later research, such as by Langer and Jochem [44] and Huang et al.
[37] who combined radar and vision technologies to detect and classify road vehicles ahead of the car, with up to 97% accuracy, showing that even relatively older vehicle detection systems are highly reliable.
Jenkins et al. [40] showed how cyclist detection could be implemented using Bicycle to Vehicle communication systems. By outfitting cyclists with a human-machine interface (HMI), they were able to receive basic safety messages, delivered using multimodal audio and haptic cues, from a smartphone speaker and attachable handlebar grips [10]. These safety messages were categorised into five levels, describing recommended actions to the cyclist. Lujic et al. [48] furthers this idea, by creating an Edge network around a city which would detect when a pedestrian or cyclist entered a vehicles’ blind spot, sending a visual and auditory warning to driver’s mobile device in real-time using 5G. These papers showcase the potential ways in which feedback modalities can be used to improve cyclist safety. Furthermore, they highlight potential warning messages which could be used in our system. These don’t necessarily convey information about the potential threat, but rather they recommend actions to avoid danger.
These warning systems are examples of Intelligent Transport Systems (ITSs) - a series of technologies which aim to improve the safety of transportation [73]. Although few address how the safety of vulnerable road users (VRUs), such as cyclists, can be improved [67], of those which do, a quantitative safety impact assessment found that vehicles which contain a dedicated VRU detection system would have the greatest impact for cyclists [68]. However, despite their potential for improving cyclist safety, studies have shown that pre-existing attitudes and perceptions affect the acceptance of such systems. One such study from Angelis et al. [18], found that drivers who already express a negative representation of cyclists are more unlikely to use a cyclist detection system, compared to those who do not. This is further explored by Berge et al. [8] who studied acceptance from the perspective of the cyclist. Through questionnaires and interviews, the authors found that cyclists were worried about using technologies, such as HMIs, as they believed such technologies would force them to take responsibility over safety critical situations, regardless of whether or not it was their fault. This finding motivates the need to further study cyclists’ beliefs and attitudes towards cycling safety, to ensure that a technology such as TactiHelm would be accepted.

## 2.2 Feedback Modalities in Cycling

Wolfe et al. [82] investigated different types of distractions which cyclists commonly face, finding that auditory distractions were most common, followed shortly by visual ones. These distractions commonly occur from interaction with a mobile device, which studies have found to increase the risk of crashing whilst cycling [54, 49]. With over half a surveyed population admitting to using their mobile device on every trip [31], there have been calls to put legislation in place to prevent the use of smartphones whilst cycling [59]. While some studies investigate ways to improve smartphone interaction whilst cycling to reduce distraction [63, 34] other approaches have investigated alternative interaction modalities, which don’t consume the cyclists visual senses. Pielot et al. showed how vibrotactile stimulation can be effective in improving cyclists’ visual focus, by developing Tacticycle - a bicycle with a set of directional cues encoded by the relative intensity across both handlebars [62]. Although the authors remark that the navigational routes used in their study were simple, no participants reported losing orientation, and positively described the ease of interpreting the vibrotactile cues, with minimal cognitive effort. Steltenpohl and Bouwer support these findings using Vibrobelt
- a vibrotactile belt also developed to aid navigation while cycling [70]. Through analysis of visual focus and spatial knowledge acquisition, they found that Vibrobelt increased participants ability to recall images from the route; however, they were generally slower at navigating. These studies showed that vibrotactile feedback is an effective way of communicating information without decreasing the cyclists’ visual focus - an important aspect of cycling.
This concept of utilising different sensory channels to convey information is studied by Wickens [79] and Wickens and Liu [80], who explored Multiple Resource Theory - a model of human information processing which predicts that attention is a limited cognitive resource that can be allocated across different tasks and modalities. The model implies that multiple sensory channels can be used simultaneously, without impairing the attention of an individual, within their cognitive capacity. Seeking to take advantage of this concept, Wickens suggests that tasks can be configured to utilise these multiple sensory channels - exploiting our informationprocessing capabilities.
Previous studies have explored this idea further, by comparing the effectiveness of unimodal and multimodal warning messages for cyclists. Strohaeker et al. [72] compared auditory and vibrotactile warnings. They found that auditory warnings were more effective for decreasing participants response time to potential collisions, but vibrotactile warnings were still effective for a system which does not require urgent reactions from the cyclist. However, a study conducted by Peeters et al. [60] found that vibrotactile signals were not only perceivable during diverse levels of physical effort, but that cyclists’ reaction time to stimuli shortened

2

as they cycled with greater effort, acknowledging the potential of utilising tactile feedback for cycling. Matviienko et al. [51, 50] expanded upon this research by comparing the delivery of navigational instructions to child cyclists using visual, auditory, and vibrotactile feedback. Their results showed that when instructions were delivered multimodally, cue interpretation accuracy increased and cyclists showed a shorter reaction time to potential dangers. These findings are backed by Sawitzky et al. [77, 78] who similarly compared the combination of different awareness message modalities for cyclists, finding that a multimodal combination of visual messages and auditory icons was preferred by participants. Although these studies clearly outline the potential benefits of providing feedback multimodally, we keep our TactiHelm system restricted to only unimodal vibrotactile feedback, so that we may thoroughly assess the impact this has on cyclists’ perceived safety and focus.
Despite auditory and vibrotactile modalities having the potential to aid visual feedback, they each have disadvantages. Waard et al. [20] found that 68% of auditory cues were missed when participants were listing to music, an act which many admit to doing. Although this could be mitigated by wearing bone conducting headphones [82], May and Walker [52] found that their usage worsened participants ability to localise critical environment sounds. Erdei et al. [24, 23] reported that perception of vibrotactile signals worsen when cycling over surfaces which cause haptic interference. However, they suggested this could be overcome by adjusting how the stimuli was delivered to the cyclist. This motivates our decision to deliver vibrotactile stimuli through the cycling helmet, as this remains in-contact with the rider at all points of the journey and haptic interference received from the terrain dissipates the further it travels [47], with the helmet being one of the furthest points of contact away from the source of interference. Therefore, delivering tactile stimuli from the helmet to the scalp allows for greater perception.

## 2.3 Using Vibrations to Encode Distance

Parameters to encode information is studied by van Erp, who explores spatial and temporal effects of vibrotactile stimuli [25]. The paper serves as a set guidelines for implementing a vibrotactile system and suggests that a vibrotactile display affords five adjustable parameters: the location, timing, frequency, amplitude, and waveform of a vibration. How these parameters can be used is described by Brewster and Brown [11], who introduce Tactons - structured, abstract messages, whose meaning is encoded using the parameters of tactile perception. The authors expand on the parameters suggested by van Erp, explicitly describing how temporal characteristics of a vibration, such as rhythm and duration can be used.
Previous studies have investigated how these parameters can be used to encode distance. van Erp et al. [26] and Straub et al. [71] both performed similar studies, investigating the effectiveness of different distance encoding schemes to aid navigation for pedestrians. Both studies used different combinations of rhythm, duration, intensity, and frequency to encode distance, finding that access to distance information did not aid the navigational performance of participants. However, the authors from both studies admit this is likely attributable to the confounding of parameters in their defined schemes.

These inconclusive findings identified a need to further explore how distance could be encoded using temporal aspects of vibrotactile stimulation, something which the skin is sensitive to [75]. McDaniel et al. [53] utilised tactile rhythms to convey four different short-range distances, to the blind. This was done by decreasing the delay between vibration pulses as the distance decreased. The experiment proved effective and showed that given a small training period, users were able to effectively identify different tactile rhythms and associate them with their respective distances.
Pielot et al. [61] further studied distance encodings, comparing rhythm, duration, and intensity based schemes, for a fast-paced 3D multiplayer game. Participants found the rhythm-based scheme the easiest to judge distance. Furthermore, they proved it was possible to accurately perceive and interpret vibrotactile signals in an environment with high cognitive demand, similar to a task such as cycling in our context.
Asif et al. [5] further studied how rhythm can be used to encode distance, comparing three rhythm-based schemes: rhythm only, rhythm and intensity, and rhythm and duration. These schemes were used in-vehicle, to indicate four different categories of distance until an approaching turn. The results found that the combination of rhythm and duration (where the pulse duration stayed the same but the number of pulses decreased as the distance decreased) was the easiest for participants to learn and led to the smallest amount of navigational mistakes.
This finding motivated Prasad et al. [64] to develop Hapti-Moto - a wearable vest which provides vibrotactile feedback regarding upcoming turns for motorcyclists. Through a user study, they were able to prove that the rhythm and duration coding scheme for distance, was effective at providing navigational instructions to motorcyclists. This paper highlights the effectiveness of using a rhythm and duration to encode different distances. Additionally, this study was performed at low speeds of below 25 mph, suggesting that these results may be similarly applied to our cyclist demographic.

## 2.4 Vibrotactile Stimulation on the Head

Gilliland and Schlegel [30] studied the spatial acuity of the head, investigating how various configurations of 4 to 12 tactile actuators, placed across the coronal plane of the head (from ear to ear), affected localisation ability. They found that optimal tactile detection and localization accuracy occurred when using six actuators - with a 93% accuracy. More than this, and both the accuracy and reaction time worsened.
Myles and Kalb [55] explored how tactile perception varied across different regions of the head, using various configurations of eight actuators. They found that the scalp was the least sensitive loci on the head, whereas, the regions around the axial plane of the head (namely the forehead, occipital, and temple regions) were the most sensitive. These different regions can be seen in Figure 3. In subsequent research, Myles et al. [56] determined that the density of hair on the head only minimally impacts tactile perception. Furthermore, this effect is confined to only the regions of the head which are the least sensitive.
de Jesus Oliveira et al. [19] continued Myles and Kalb’s work, by comparing the spatial resolution of the identified sensitive head regions around the axial plane. Although they found that the forehead was the most accurate region

3

for spatial discrimination of vibrotactile stimuli, they also showed that the centre of the occipital region had high precision, which decreased as the distance from the head midline increased. This phenomenon was named the Midline Effect, and had previously been indirectly reported on by van Erp [74]. He proposing various hypotheses for the effect, that include the body’s midline serving as an anchor point to assist in absolute localization, or that the central nervous system possesses specific characteristics for processing stimuli. Regardless of the reason, de Jesus Oliveira et al. suggests further research is needed investigating the effect -highlighting the need to investigate how tactile perception differs between regions of the head across the sagittal plane. Few studies have explored how vibrotactile feedback can be utilised in a helmet. Bertram et al. introduced the Tactile Helmet [9] which communicated the distance of a detected object to a pedestrian wearer using the intensity of a vibration. Yamauchi and Suzuki [83] extended this by demonstrating how such a helmet could be used for hazard notification for motorcyclists. The direction of a hazard corresponded to the location of a vibration around the axial plane of the head, whereas the vibration strength corresponded to the level of risk. They showed that the use of four directions and three levels of intensity was effective at notifying a wearer of an approaching hazard, even in winds of up to 100km/h.
However, in the context of cycling, only two studies to the best of our knowledge have investigated how vibrotactile stimulation around the head can be used. Krauß et al.
[43] developed a navigational headband which vibrated on the wearers head in the direction of travel - using 12 actuators for a spatial resolution of 30◦
. They demonstrated that
vibrotactile stimulation could be used on the head whilst cycling, without any reported discomfort or distraction. Similarly Vo et al. introduces the TactiHelm helmet [76] - a cycling helmet aimed to inform cyclists to potential collisions. Direction was conveyed using one of four tactile actuators in the cardinal directions and two distance levels were encoded using two distinct tactile cues. They showed that cyclists were able to accurately identify the proximity and direction from a cue 91% and 85% of the time respectively. This highlighted the potential of TactiHelm as a hazard notification system for cyclists, and it is from this work which this paper is inspired to continue development of such a system.

## 3. EXPLORATORY SURVEY

To identify the requirements of a hazard notification system such as TactiHelm, an online survey was conducted to understand cyclists’ attitudes and behaviours towards safety while cycling. The survey used a mixture of open response, Likert scale, and multiple choice questions to explore topics such as use of safety equipment and techniques and causes of injuries. It was distributed to various cycling groups around Glasgow. We emphasised that we did not intend to judge any participants’ answers on their safety or legality - instead we only wish to gather insights for use for the project.
The survey was answered by 110 respondents, aged 16-24 (14.55%), 25-34 (10.91%), 35-44 (11.82%), 45-54 (31.82%), 55-64 (24.55%) and 65+ (5.45%) years old. Participants identified as 61.82% male, 37.27% female, and 0.91% other. Roughly 90% of respondents were from Scotland, with the majority from Glasgow. These demographic data were collected as studies have shown that the risk and severity of cyclist injuries vary depending on factors such as roadway characteristics and demographic group [7].
90% of respondents answered saying they cycle more than one hour a week, with 42.73% cycling 7+ hours a week. Respondents equally cycled on city roads (30.37%), cycle paths (29.63%), and country roads (28.15%), with the remaining 11.85% cycling in other environments. Notably, 72.73% of respondents answered that they had suffered some kind of injury while cycling - 60% a minor injury and 12.73% a major injury. Reasons for injury varied, from slipping on wet and uneven roads, to colliding with another road vehicle. Over 80% stated that they regularly wear a helmet. When asked for reasons for not wearing a helmet, a variety of responses were given, with the most common being that they are not available when hiring a bike. Some respondents answered that they did not believe helmets to be useful in certain scenarios, “Helmets are designed to prevent injury at relatively low speeds, speeds which are comfortably exceeded by adult cyclists of even moderate fitness. I believe the effectiveness of helmets to prevent injury is grossly overstated” [P13]. However, multiple studies conducted on the effectiveness of bicycle helmets [57, 38, 36, 13] have found that regardless of the crash severity, helmets can help reduce the severity of head injuries by 48% [38].
When asked about safety technology, the most common equipment following from a helmet were cycle lights (87.27%), reflective gear (64.54%), and bike computers or mounted smartphones (60.90%). Of nine respondents who stated they had a bike radar, all of them said they had a Garmin radar. When asked to comment on its usefulness they all expressed that they benefit from being more aware of vehicles behind them; however, a common disadvantage is its high cost. Participants were asked to freely respond with the challenges they face which makes cycling feel unsafe. Categorising the responses, the most common ones were “close passes from cars” (38.18%), followed shortly by ”poor cycling infrastructure” (34.54%).
Finally, participants were provided with a brief description of TactiHelm and were invited to comment on its usefulness for cycling. Respondents thought the concept could be useful, but were worried that it may be distracting - expressing concern that it may remain vibrating at all times while a vehicle is detected. These comments are useful in understanding users pre-conceived notions and worries as to how such as system may operate, and help shed light on specific problems which should be addressed in TactiHelm.

## 4. TACTIHELM

## 4.1 The TactiHelm System

The TactiHelm system is composed of three primary components: the helmet, a Garmin bike radar, and the controller application on a mobile device, as seen in Figure 2. The TactiHelm helmet builds on previous work from Vo et al. [76], and can be seen in Figure 1. The inside lining of the helmet is equipped with 10mm diameter, three volt ERM coin cell tactile actuators. The intensity of these are controlled by PWM signals from 0 to 3V generated by an Arduino Uno micro-controller [3], which is subsequently powered by a 9V battery. PWM varies the voltage to the actuator in such a way that it is represented as an analogue signal - si-

4

multaneously effecting the frequency and amplitude of the signal wave [42]. Therefore, the term ’intensity’ refers to the combined effects of vibration frequency and amplitude. The circuit is also equipped with an HC-06 Bluetooth Module [22], which can connect to a mobile device using Bluetooth Classic, allowing for remote control over the actuators.

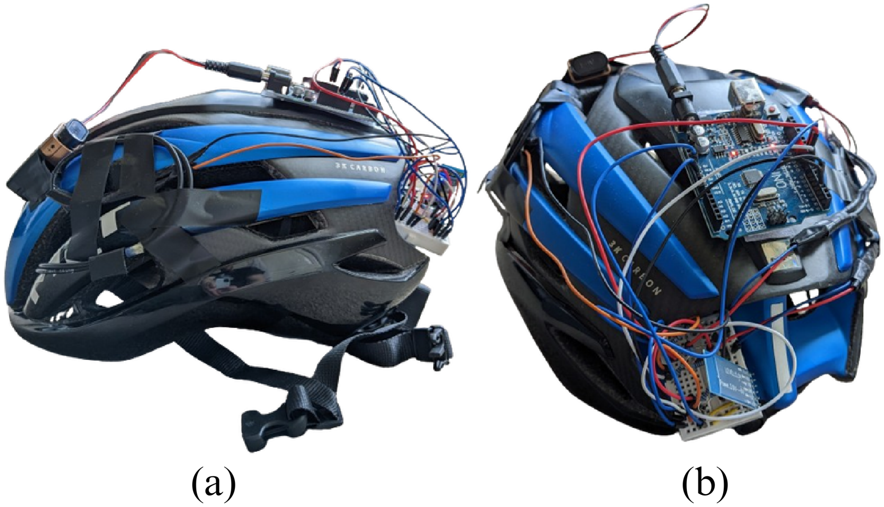
[picture p31: figure]

Figure 1: The developed TactiHelm helmet: (a) side-view,
(b) rear-view.

A custom Android application, known as the controller, was developed to allow communication between the bike radar and Arduino. The controller acts as a pipeline between the two devices: parsing information received from the radar into the relevant instructions for the Arduino to deliver the specified stimulus. Furthermore, the application provides manual control over the actuators, giving the researchers precise control over the location, intensity, and further attributes of delivered stimuli.
The bike radar used in this project was the Garmin Varia RTL515 [28]. Designed to attach to the back of a bicycle, the radar can detect vehicles within a 140-metre range and offers a 220◦
viewing angle. This allows for complete detection of vehicles approaching from behind, extending beyond the cyclist’s standard peripheral vision [69]. The radar detects approaching vehicles’ distance and speed, and sends this to the controller application using Bluetooth Low Energy. These are then used to calculate the following distance of the closest approaching vehicle.

## 4.2 Alerting Using Following Distance

The following distance is a commonly used metric in roadsafety: defined as the time it would take an approaching vehicle behind a cyclist to reach their location if they were to suddenly stop [65]. The exact recommended value varies depending on conditions such as the weather; however, the UK Government suggests that a following distance of at least two seconds is kept between vehicles at all times [33]. We hypothesised this to be an appropriate metric for our system, as it encompasses both the distance and speed of the vehicle into a single value. However, such an arbitrary value can be meaningless to a cyclist.
Although, little research has investigated how distance can be classified in our context of hazard detection for a cyclist, many works have explored the optimal number of distance categories in other contexts. Four-level distance classifications have been used to convey inter-personal distances [53, 61] and distance until an upcoming turn [5]. Threelevel classifications have also been proven to be useful [64], showing that an extra distance category does not improve

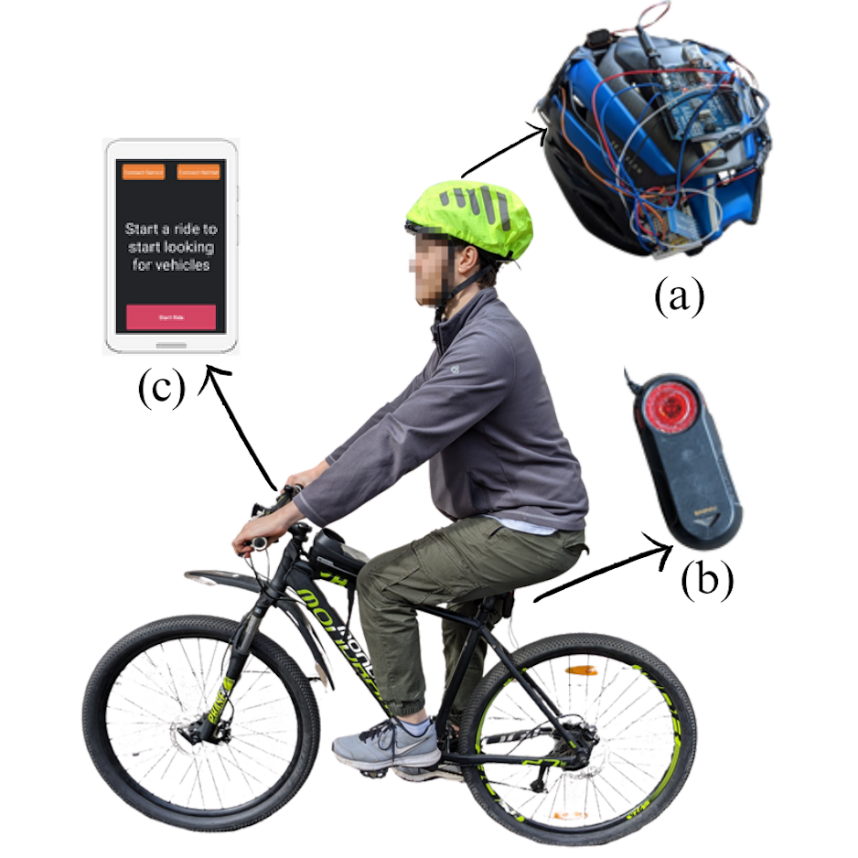
[picture p32: figure]

Figure 2: A commuter cyclist equipped with (a) TactiHelm helmet with attached rain cover (b) Garmin Varia RTL515 bike radar, and (c) a mobile device hosting the controller application.

a user’s awareness of distance. Therefore, seeking to avoid overwhelming the user with unnecessary tactile stimulation, we quantise our following distance metric into three discrete categories which provide more physical meaning. We name these categories: far, near, and imminent.

## 4.3 Actuator Configuration on the Head

A unique feature the use of a helmet affords is the ability to use locations across the three anatomical planes: the sagittal, coronal, and axial [39]. Previously mentioned studies have utilised the axial plane of the head, using tactile motors placed around the head’s circumference to convey direction [9, 83, 43, 76]. However, despite research showing the effectiveness of utilising the Midline Effect across the sagittal plane of the scalp [19, 74], this has yet to be explored in the context of helmet-based systems. Furthermore, stimuli in the occipital region have been shown to be suitable for conveying warning signals [19].
Therefore, we hypothesise that placing tactile actuators along the head’s sagittal midline could effectively signal the distance of an approaching vehicle from behind. Specifically, we use three actuators, whose subsequent activation, from the nape to the forehead, corresponds to the progression of the approaching vehicle, following our previously defined following distance categories (far, near, and imminent). This effectiveness is attributed to the innate analogy it creates, simulating the sensation of a car approaching. We do not precisely measure the separation between these actuators; instead, we initially set them approximately 70mm apart, so that each lies within a distinct region of the head. We then investigate how their perception varies in our following study, so that we may empirically find the optimal placement. A diagram of the placement of the actuators across the different regions of the head can be seen in Figure 3.

5

Left
Temporal

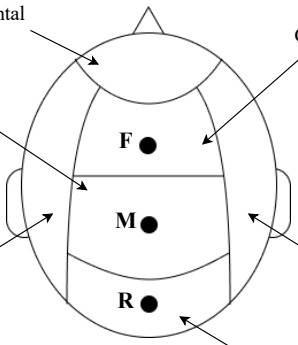
[picture p33: figure]

Occipital

Parietal

Frontal

Right
Temporal

Central

Figure 3: Diagram shows placement of actuators in different regions of the head. The front actuator (F) lies in the central region, middle (M) in the parietal, and rear (R) in the occipital.

## 4.4 Vibrotactile Distance Encodings

To understand how the following distance can be converted into a vibrotactile signal, we consider the previously identified encoding parameters: the location, rhythm, duration, frequency, amplitude, and waveform of a vibrotactile stimuli [25, 11]. The parameters of frequency and amplitude, which typically have 5-7 perceptually distinguishable levels [25], are encompassed within the candidate parameter ’intensity’. However, in our context of use, where the stimuli recipient receives haptic interference from the terrain they cycle over, the number of distinguishable levels reduce, making a 3-level distance category unsuitable. Additionally, the waveform of our stimuli signal is restricted by our actuators, which are only capable of producing sine waves.
This leaves the parameters of location, rhythm, and duration to be used to encode distance. Prior work has typically used location to convey direction. However, in our system, we do not convey the specific direction of the vehicle; instead, we only prompt the rider to look behind, meaning this parameter is left free.
Rhythm is a complex parameter where a number of stimuli are delivered in succession to compose a pattern. Similarly, duration can refer to multiple different attributes, such as the length of a stimulus, or overall length of a cue. How the terms rhythm and duration are defined is unclear and changes across many previous works. McDaniel et al. [53] used rhythm by varying the delay between two 50ms stimuli in a cue. Pielot et al. [61] used rhythm by varying the number of 200ms stimuli with a 200ms delay between each, and referred to duration as the length of a single stimulus. Asif et al. [5] also used rhythm by varying the number of stimuli in a cue; however, as the number of stimuli increases, their duration and delay between each decreased, keeping the overall duration of the rhythm constant. Their combined rhythm and duration encoding similarly kept the overall duration of the rhythm constant, but instead also kept the duration and delay of the varying number of stimuli constant.
In the following study, we explicitly define duration and the exact parameters which compose the term rhythm, and investigate how these parameters can be used alongside location to encode distance.

## 5. LAB STUDY - INVESTIGATING VIBRO-TACTILE DISTANCE ENCODINGS

The goal of this experiment was to investigate how different distance categories could be effectively encoded and conveyed, using vibrotactile cues delivered from a cycling helmet. We compared six defined encoding schemes which were composed of different patterns and durations. The evaluation investigated the following sub-questions from our first primary research question:

RQ1.1. Is the sagittal plane of the scalp a suitable location for vibrotactile stimulation?

RQ1.2. Which combinations of pattern and duration encodings are most usable?

RQ1.3. Which combinations of pattern and duration encodings gives the lowest number of information perception/interpretation errors?

## 5.1 Experiment Design

### 5.1.1 Independent Variables

The experiment centered around the delivery of distance information, which was composed of three independent variables: the distance category, the vibration pattern, and cue duration. The combination of the pattern and duration created six unique experimental conditions, known as the distance encoding schemes. When combined with the three distance categories (far, near, and imminent), they create 18 vibrotactile cues. How the pattern and duration effect the parameters of a vibrotactile cue can be seen in Table 1 and Figure 4.
Pattern: The vibration pattern is a composite parameter, which combines the location of a vibration (the activated actuator), and the delay between delivered stimuli (also known as the inter-stimulus-interval). The vibration pattern had three distinct levels: Singular, Wall, and Wave. With a Singular pattern, only a single actuator at the location relative to the specified distance is activated. With a Wall pattern, all actuators, from the rear to the one at the location relative to the specified distance, are activated simultaneously. The Wave pattern works similarly, however, there is a delay of 150ms between each actuators activation. These pattern names are inspired from a pilot study with a single participant, who described the feeling of the patterns as ‘creating a wall’ or ‘moving like a wave across your head’. Duration: In this study, we define duration as the number of times a vibrotactile cue is delivered and had two distinct levels: Constant and Varying. With a Constant duration, each vibration cue was delivered only once. With a Varying duration, the number of times a cue is delivered increased as the distance decreased.

### 5.1.2 Apparatus and Encoding Parameters

The helmet with the described configuration of tactile actuators was used to deliver the vibrotactile cues. In this paper, we define a vibrotactile cue to be the composition of a number of tactile rhythms, and define a rhythm to be the composition of a number of tactile stimuli.
Stimuli Parameters: We define a stimulus to have four possible parameters: (i) intensity (frequency + amplitude), (ii) waveform, (iii) location, and (iv) stimulus duration. Each actuator produced sinewaves and was set to vibrate at its

6

PATTERN (Location + ISI) | RHYTHM DURATION
Distance Cue | Singular (ISI=0) | Wall (ISI=0) | Wave (ISI=150ms) | Constant | Varying
Far | R | R | R | 1 | 1
Near | M | R+M | R→M | 1 | 2
Imminent | F | R+M+F | R→M→F | 1 | 3

Table 1: Table shows the activated actuators and number of deliveries for each distance, pattern and duration level. R, M, and F refers to the Rear, Mid, and Front actuator respectively. + denotes simultaneous activation and → denotes delayed activation.

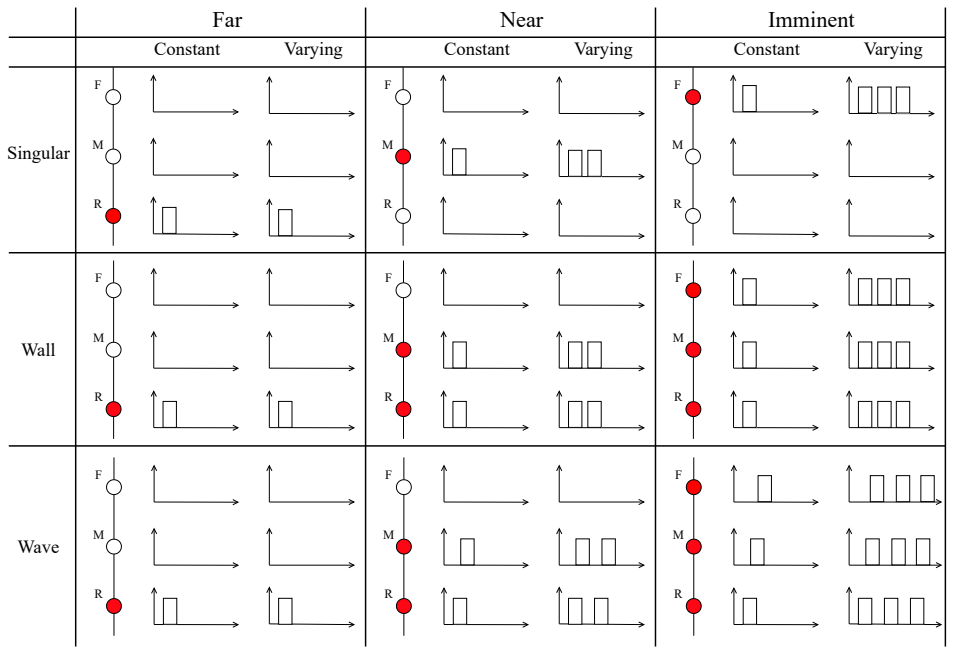
[picture p34: figure]
Singular; Wall; Wave; Constant; Varying; Far; Near; Imminent

Figure 4: Diagram shows the vibrotactile cues delivered to each actuator, depending on the distance, pattern, and duration.

maximum intensity, with a duration of 300ms. The possible
locations were one of three actuators: the front, middle, and rear, and was dependent upon the encoding scheme.
Rhythm Parameters: We define a rhythm to have three possible parameters: (i) inter-stimulus-interval (ISI), (ii) number of stimuli deliveries, and (iii) length of the rhythm. Often referred to as the ’delay’, the ISI is the time between consecutive stimuli in a rhythm, and when combined with the location, became our pattern variable. The number of stimuli deliveries is the number of times that a single actuator is activated per rhythm, and was set to a constant value of 1. The overall length of the rhythm is dependent upon these prior parameters.
Cue Parameters: We define a cue to have three possible parameters: (i) inter-rhythm-delay, (ii) number of rhythm deliveries, and (iii) length of the cue. The inter-rhythminterval is the time between consecutive rhythms, and was set to a constant 100ms. The number of times that a rhythm is delivered per cue was our duration variable, and was dependent on the encoding scheme. The overall length of the cue is dependent upon these prior parameters.

### 5.1.3 Participants

20 participants were recruited for the study, all aged 16-24 years old. However, the helmet did not fit P13, therefore they could not participate in the study.

### 5.1.4 Dependent Measures

Following our defined research questions for the evaluation, we determine our dependent measures to be the usability of the encoding schemes, and the information perception of participants using such schemes. We measure the usability of an encoding scheme in terms of its usefulness, distinguishability, interpretability, intuitiveness, and length of its cues. This is measured using a combination of qualitative feedback and 5-point Likert scale questions in a post-experiment questionnaire [41]. We measure information perception by recording the errors made by participants in identifying the correct cues. Finally, we analyse participants responses to the applied questionnaire to further understand additional related factors, such as their perception of the actuators, the comfort of the helmet, and their understanding of following distance.

### 5.1.5 Procedure

Each experimental session began by first briefing the participant on the study’s purpose and explaining how the TactiHelm system operates. Participants were allowed to wear the helmet and adjust the tightness until they were comfortable with its placement. They were presented a diagram which showed the positioning of the actuators inside the helmet (Figure 3) and the evaluator activated each one, re-

7

Encoding Scheme | Useful. | Distin. | Interp. | Intuit. | Length
Singular Constant | 3.05 ± 1.31 | 2.79 ± 1.13 | 2.95 ± 1.03 | 3.79 ± 0.92 | 3.00 ± 1.15
Singular Varying | 4.42 ± 0.77 | 4.26 ± 0.93 | 4.42 ± 0.61 | 4.53 ± 0.61 | 3.89 ± 1.05
Wall Constant | 2.74 ± 1.19 | 1.95 ± 1.03 | 2.42 ± 1.07 | 3.42 ± 1.12 | 3.11 ± 1.15
Wall Varying | 4.32 ± 0.88 | 4.42 ± 0.84 | 4.47 ± 0.70 | 4.58 ± 0.51 | 3.89 ± 1.33
Wave Constant | 3.58 ± 1.02 | 2.84 ± 1.12 | 3.47 ± 1.17 | 4.16 ± 0.83 | 3.58 ± 1.12
Wave Varying | 4.58 ± 0.51 | 4.37 ± 0.90 | 4.53 ± 0.70 | 4.63 ± 0.76 | 3.74 ± 1.20

Table 2: Table shows the mean and standard deviation of the Likert scores for each encoding scheme for each measure of usability. Likert scores are measured on a five-point scale (1 - Strongly Disagree, 5 - Strongly Agree). The highest score in each category is emboldened.

peating any if a participant requested. The evaluator gave
a brief explanation of the term “following distance”, and explained the three categories we have divided this value into. Participants were then asked to complete the first part of the provided questionnaire, regarding their initial thoughts towards the aforementioned described concepts.
To compare the six encoding schemes, we used a withinsubjects design, where each participant evaluated every scheme under lab conditions. This process was split based on the three levels of vibration pattern. Participants were sequentially introduced to each pattern level, under which they evaluated both duration levels and completed part of the provided questionnaire, before advancing to the next subsequent pattern level. This approach enabled participants to provide feedback on the two most recent encoding schemes immediately after evaluation, ensuring that their impressions were accurately captured. The evaluation order of the schemes was balanced using a Latin square.
The evaluation of a scheme was composed of three trials. During a trial, a vibrotactile cue representing a distance would be sent to the helmet every five seconds. Participants would then have to state which distance they believed was just conveyed. The first trial was a short training phase, aimed to quickly train participants on how to interpret the encoding scheme. The second and third trials were part of the data gathering phase, where participants’ results would be recorded without correction. This totalled to 18 trials for each participant. Trials were consistent in length: every training trial had a total of seven cues, whereas every data gathering trial had 12 cues, with an equal split of different distances. The order of the trials remained constant.

## 5.2 Results

The following presents the acquired results from our study. Friedman’s ANOVA tests were applied to Likert data from the questionnaire, followed by Wilcoxon tests on each pair of conditions. For the cue perception errors, we applied a two-way repeated measures ANOVA, to compare the means of the number of correct guesses across the six schemes and three distance cues. This was followed by pairwise t-tests across these two groups. For the Wilcoxon tests, a Bonferroni correction was applied to the standard alpha value of 0.05, to account for the number of comparisons (N=3) in each group [4]. The means and standard deviations for each usability measure can be seen in Table 2. Tables 3 and 4 show the results of the post-hoc Wilcoxon and t-tests.

### 5.2.1 Usability of Encoding Schemes

The applied Friedman tests showed that there were significant differences across all our measures of usability: usefulness (Chi-Square=49.16, p<.05), distinguishability (Chi-

Square=58.04, p<.05), interpretability (Chi-Square=51.37, p<.05), intuitiveness (Chi-Square=32.82, p<.05), and length of cues (Chi-Square=14.09, p<.05).
Constant vs Varying durations within each pattern: The Wilcoxon tests revealed that within each pattern category, there were significant differences between the two duration conditions, with the Constant conditions repeatedly outperforming the Varying conditions across all usability measures. Single vs Wall vs Wave patterns within the Constant duration: The Wilcoxon tests revealed that when comparing the Single and Wall patterns with a Constant duration, the only significant differences was between their distinguishability, where the Single condition was ranked better. In-fact, the Wall Constant scheme was ranked the worst across all the usability measures, with the exception of the length of the cue, where participants ranked the Single Constant scheme the lowest. Comparing the Wave condition to the other two, we see that significant differences were found in many of the usability measures, with the Wave Constant scheme being ranked the highest or near highest by participants across all dimensions.
Single vs Wall vs Wave patterns within the Varying duration: When comparing the different pattern conditions for a Varying duration, there were no significant differences found across any usability measure, with all the Varying schemes being rated equally high.

### 5.2.2 Information Perception

Information perception was measured by recording the number of errors made by participants in identifying the correct distance cues. Figure 5 presents these results for each distance category for each scheme. Our two-way ANOVA test revealed there were statistically significant differences between pairs of schemes (F=9.25, p<.05) and distance cues (F=14.86, p<.05), and there was a significant interaction between these two groups (F=6.83, p<.05).
Differences in cue perception within schemes: The t-tests revealed there was a significant difference in cue perception between the far (M =96.16%, SD=4.70%) and imminent (M =87.94%, SD=8.98%) distance cues; t=4.54, p<.05. However, the only scheme to exhibit this difference was the Wall Constant scheme; t=5.25, p<.05. Similarly a significant difference was found between the imminent and near (M =94.30%, SD=5.23%) cues; t=-3.78, p<.05. However, this was only seen in the Singular Constant (t=-2.69, p<.05) and Wall Constant (t=-3.36, p<.05) schemes. There was no significant difference found between the far and near cues; t=1.58, p=0.13.
Far Cue: The only statistically significant difference found via the t-tests for the far distance cue, was between the Wall and Wave Varying scheme; t=2.19, p<.05.

8

Comparison | Useful. | Distin. | Interp. | Intuit. | Length
Sing-Con. vs Sing-Var. | W=0.0, p<.001 | W=0.0, p<.001 | W=0.0, p<.001 | W=4.0, p=.008 | W=7.0, p=.011
Wall-Con. vs Wall-Var. | W=15.5, p=.002 | W=0.0, p<.001 | W=3.0, p<.001 | W=0.0, p<.001 | W=15.0, p=.056
Wave-Con. vs Wave-Var. | W=5.5, p=.001 | W=0.0, p<.001 | W=14.5, p=.008 | W=11.0, p=.041 | W=33.5, p=.659
Sing-Con. vs Wall-Con. | W=32.5, p=.35 | W=8.5, p=.028 | W=25.0, p=.145 | W=13.5, p=.131 | W=23.0, p=.627
Sing-Con. vs Wave-Con. | W=3.0, p=.031 | W=68.0, p=1.00 | W=36.0, p=.166 | W=9.0, p=.100 | W=9.0, p=.055
Wall-Con. vs Wave-Con. | W=2.5, p=.010 | W=10.0, p=.006 | W=5.5, p=.001 | W=5.0, p=.005 | W=10.5, p=.075
Sing-Var. vs Wall-Var. | W=19.0, p=.668 | W=21.0, p=.49 | W=30.0, p=.763 | W=6.0, p=.655 | W=22.5, p=1.00
Sing-Var. vs Wave-Var. | W=2.0, p=.257 | W=16.0, p=.773 | W=10.5, p=.527 | W=3.5, p=.577 | W=12.0, p=.366
Wall-Var. vs Wave-Var. | W=12.0, p=.19 | W=25.5, p=.834 | W=43.0, p=.851 | W=10.5, p=.527 | W=12.0, p=.366

Table 3: Table shows the Wilcoxon tests results for each usability measure, found between different conditions. A Bonferroni corrected alpha value of 0.017 was used. Significant values are emboldened.

Comparison | Far | Near | Imminent
Sing-Con. vs Sing-Var. | t=-0.64, p=.531 | t=-1.37, p=.187 | t=-3.39, p=.003
Wall-Con. vs Wall-Var. | t=-1.92, p=.070 | t=-3.01, p=.007 | t=-5.41, p<.001
Wave-Con. vs Wave-Var. | t=-0.85, p=.408 | t=-2.36, p=.030 | t=-2.62, p=.017
Sing-Con. vs Wall-Con. | t=0.00, p=1.00 | t=1.78, p=.092 | t=2.87, p=.010
Sing-Con. vs Wave-Con. | t=-0.14, p=.891 | t=0.56, p=.586 | t=0.29, p=.776
Wall-Con. vs Wave-Con. | t=-0.17, p=.867 | t=-1.29, p=.213 | t=-4.02, p<.001
Sing-Var. vs Wall-Var. | t=-1.23, p=.235 | t=-0.29, p=.772 | t=0.52, p=.607
Sing-Var. vs Wave-Var. | t=-0.27, p=.790 | t=-0.62, p=.542 | t=0.00, p=1.00
Wall-Var. vs Wave-Var. | t=2.19, p=.042 | t=-0.57, p=.578 | t=-0.81, p=.429

Table 4: Table shows the t-tests results for the perception of distance cue, found between different conditions. An alpha value of 0.05 was used. Significant values are emboldened.

Near Cue: Significant differences for the near distance cue were revealed between the Wall Constant and Varying schemes (t=-3.01, p<.05), and the Wave Constant and Varying schemes (t=-2.36, p<.05).
Imminent Cue: Significant differences for the imminent cue were found between the Constant and Varying durations for each pattern: Singular (t=-3.39, p<.05), Wall (t=-5.41, p<.05), and Wave (t=-2.62, p<.05). Additionally, significant differences were found between schemes with a Constant duration, namely the Singular and Wall (t=2.87, p<.05), and Wall and Wave (t=-4.02, p<.05) conditions. Recognition errors across schemes: Figure 6 shows the ratio of recognised distance cues guessed by participants, for each cue, for each scheme. Far cues were rarely misinterpreted; however, when they were, they were typically misinterpreted as near cues. Near cues were also typically correctly recognised, with the exception of within the Wall Constant scheme, where 14.47% were misinterpreted as imminent cues. Imminent cues were highly recognised across the Varying schemes; however, these were typically misinterpreted as a near cue in the Constant schemes, such as in the Wall Constant scheme where 32.89% were misinterpreted as near. Imminent cues were also the most commonly missed, with 3.29% missed with the Singular Constant scheme.

### 5.2.3 Further Comments and Observations

Scheme Preference: Participants ranked the six schemes in order of preference. A Friedman’s test revealed there were significant differences in their rankings (Chi-Square=47.90, p<.05). All of the Varying conditions were ranked higher than their Constant counterparts, with the Wave condition

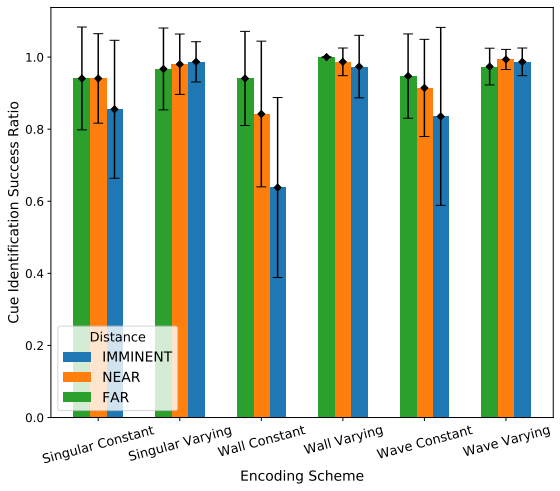
[picture p35: figure]
Singular Constant; Encoding Scheme; Cue Identification Success Ratio; Distance; IMMINENT; NEAR; FAR

Singular Varying Wall ConstantWall VaryingWave Constant Wave Varying

Figure 5: Cue identification success ratio of each distance cue across the six schemes.

being the highest ranked, followed by the Wall then Singular condition. The Wilcoxon tests revealed significant differences between every combination of these schemes. Perception of the Actuators: Participants were asked to rate the perception of the three tactile actuators using a 5-point Likert scale. Applying the Friedman’s test revealed that there were no statistically significant differences between the perception of the Front (M =3.42, SD=1.35), Mid-

9

FAR | NEAR | IMMINENT

Conveyed Distance

FAR NEAR IMMINENT MISSED

Guessed Distance

94.08% | 5.92% | 1.97%
5.26% | 94.08% | 9.21%
0.00% | 0.00% | 85.53%
0.66% | 0.00% | 3.29%

Singular Constant

FAR | NEAR | IMMINENT

Conveyed Distance

FAR NEAR IMMINENT MISSED
96.71% | 0.66% | 1.32%
1.32% | 98.03% | 0.00%
1.32% | 1.32% | 98.68%
0.66% | 0.00% | 0.00%

Singular Varying

FAR | NEAR | IMMINENT

Conveyed Distance

FAR NEAR IMMINENT MISSED

Guessed Distance

94.08% | 1.32% | 3.29%
3.29% | 84.21% | 32.89%
2.63% | 14.47% | 63.82%
0.00% | 0.00% | 0.00%

Wall Constant

FAR | NEAR | IMMINENT

Conveyed Distance

FAR NEAR IMMINENT MISSED
100.00% | 0.00% | 0.00%
0.00% | 98.68% | 1.97%
0.00% | 0.66% | 97.37%
0.00% | 0.66% | 0.66%

Wall Varying

FAR | NEAR | IMMINENT

Conveyed Distance

FAR NEAR IMMINENT MISSED

Guessed Distance

94.74% | 0.66% | 2.63%
4.61% | 91.45% | 13.82%
0.66% | 7.24% | 83.55%
0.00% | 0.66% | 0.00%

Wave Constant

FAR | NEAR | IMMINENT

Conveyed Distance

FAR NEAR IMMINENT MISSED
97.37% | 0.00% | 0.66%
1.32% | 99.34% | 0.66%
0.00% | 0.00% | 98.68%
1.32% | 0.66% | 0.00%

Wave Varying

0 | 20 | 40 | 60 | 80
Percentage Guessed

Figure 6: Percentage of guessed distance cues for each distance per scheme.

dle (M =3.84, SD=1.12), and Rear (M =4.11, SD=1.20) actuators; Chi-Square=3.76, p=.15. However, participants often stated that the front and middle actuators were harder to perceive: ”I was able to distinguish location on my head. However the middle and front tactors were much harder to feel than the back one” [P3].
Layout of the Actuators: Following our initial explanation and survey questions, 85% of participants correctly answered that the actuator at the back of the head would be activated if a detected vehicle was far. Additionally, participants stated that they agreed with the configuration of the actuators, ”The layout made sense in relation to the problem and the tactors are sufficiently powerful” [P7]. However, multiple participants stated that the actuators often felt too close to each other, expecting the front one to be closer to the forehead, ”I expected the middle one to be where the front is and the front one to be more towards the forehead” [P11]. Helmet Comfort: Regarding the comfort of the helmet, participants gave an average rating of 7.15 out of 10 for its’ comfortableness (SD=2.08), with many commenting that its weight and small size caused uncomfortable pressure points, such as at the back of the head.
Understanding of Following Distance From our initial explanation of the following distance, few participants (25%) correctly understood that it was in-fact a measure of time and hence typically measured in seconds. From this group, a variety of answers were provided, regarding what value the distance would be, given a vehicle was imminent, ranging from one to five seconds. Of the 75% of participants who did not correctly understand, their answers were typically measured using either metres or car/bike lengths. These ranged from one to five metres or one to two car/bike lengths. These answers did not mention what speed the vehicle would be travelling at. However, the majority of participants were not avid cyclists, with only 30% stating they cycle more than one hour per week, meaning their interpretation of this term may differ from our target group. When asked whether or not they believed the following distance would be an appropriate indicator of an approaching vehicle, most participants agreed that it would be, and agreed with the categorisation of this metric into three values.

## 5.3 Discussion

The aim of this study was to explore how the pattern and duration of a vibrotactile rhythm on the head could be used to effectively encode distance. By gathering qualitative feedback regarding usability measures and recording participants information perception errors across different encoding schemes and cues, we answer our previously defined research questions.
RQ1.1 (suitability of the head as a vibrotactile display): The configuration of the tactile actuators in our helmet was well received, with the majority of participants correctly understanding, how the layout of the actuators relate to the distance of an approaching vehicle. However, multiple participants stated they felt that the front and middle actuators were too close together, and that the front one could have been shifted closer towards the forehead to aid localisation and make the stimuli more distinguishable. This was likely related to their lower perception ratings, compared to the rear actuator. However, there are multiple further reasons which can explain the difficulty in perception. For example, as previously discussed, the front of the scalp is less perceptible than the back [55, 56, 19]. Additionally, variance in head size meant that some participants’ scalp pressed less against the top of the helmet than others, leading to a lesser perceived intensity. Because of the difficulty in perception, multiple participants stated they relied on the sound of the vibration rather than the tactile feeling. An improved experimental design would have had participants wear noise cancelling headphones to block this sensory channel; we acknowledge this as a limitation in our study.
RQ1.2 & RQ1.3 (most effective encoding scheme): In terms of both usability and cue perception, all Varying conditions performed better than all Constant conditions. This was likely due to the ability of being able to easily count the number of vibrations, opposed to the comparably harder task of having to identify the position of the stimuli on the head, as expressed by the majority of participants. This suggests that encoding distance using the duration of a rhythm (specifically the number of cue deliveries) does not inherently make it more effective, but rather it creates an easily

10 perceptible counting mechanism, from which inferring the distance is less cognitively demanding, and thus easier. Such inferences are harder to make when relying upon the location of a stimuli, which requires more cognitive demand to translate to a distance. For example, it is less cognitively demanding to infer an imminent distance from counting three buzzes, that it is by having to identify the precise location of the vibration.
This dominant effect of varying the duration can be seen in the lack of significant differences within the Varying schemes, suggesting the pattern, and hence location, is insignificant in comparison. However, despite few significant differences in cue perception, participants rated the Wave condition best of all Constant schemes, in terms of usability and preference. This could be because of the saltation sensory illusion it creates, which simulates the feeling of movement across the active stimulus loci [15, 29, 60], thus better representing the feeling of an approaching vehicle. The low cue perception of the Wall Constant scheme can be similarly explained by the funneling illusion, where the perceived location of a tactile stimulus is in-between two or more stimulus loci [27, 45, 46], causing participants to misinterpret the cues. Whether improving localisation of the stimuli would have an affect on the ease of perception is left to suggested future work. Conclusion: From this study, it is evident that our configuration of actuators along the sagittal plane of the scalp, is suitable for conveying the concept of an approaching vehicle. Although, we may aid distinguishability of these tactors be increasing the spacing between the front and middle actuators. We find that the location of vibrotactile rhythm on the scalp is insignificant in comparison to its duration and perceived intensity, as shown by participants preference to Varying schemes. However, when comparing the rhythmic patterns which vary the location and delay between delivered stimuli, participants preferred the Wave scheme, which created a sensation of movement across the scalp. Therefore in our following study, we aim to assess the effectiveness of using our defined Wave Varying encoding scheme to encode our three levels of distance.

## 6. USER STUDY - TACTIHELM EVALUA-TION

The goal of this experiment was to evaluate our developed TactiHelm system in the real world. Specifically, we assessed its usability and effectiveness in warning users of the presence and proximity of approaching vehicles behind them, all within a naturalistic setting. Through this study, we aimed to answer the following questions:
RQ2.1. Can participants accurately perceive and interpret our defined vibrotactile cues on the scalp whilst cycling?

RQ2.2. Does the use of TactiHelm improve participants’ perceived safety and comfort whilst cycling with other road vehicles?

RQ2.3. Is our 3-level categorisation of following distance into far, near, and imminent, appropriate for our proposed safety system?

## 6.1 Experiment Design

Commuter cyclists were recruited and equipped with a bike radar, the TactiHelm helmet, and a microphone to record their home to office commute. We asked participants to use TactiHelm on their normal commuting routes and to perform a think-aloud evaluation - audibly expressing any thoughts and feelings regarding the effectiveness of the helmet at warning them of approaching vehicles. Outwith of this, we asked them to behave as they normally would. After completing their commutes, participants were asked to complete a post-evaluation questionnaire, followed by a brief, semi-structured interview with the evaluator. The questionnaire included questions from the NASA-RTLX [32] and the System Usability Scale [12] questionnaire. Following this, participants were asked to perform an additional commute, without using TactiHelm, after which they would complete the NASA-RTLX questionnaire again. This was to establish a baseline score for comparison. We analysed participants’ captured audio for any qualitative comments made during the evaluation.

### 6.1.1 Dependent Measures

We used three primary dependent measures to evaluate the effectiveness of our system: 1) NASA-RTLX data to measure participants workload whilst cycling, both with and without TactiHelm, 2) SUS data to measure the usability of TactiHelm, and 3) qualitative comments made during the think-aloud evaluation, questionnaire, and interview. We primarily looked for comments regarding the accuracy and effectiveness of the vibrotactile warnings, and the perceived safety and awareness of the participant. We also noted comments related to additional factors of the helmet, such as its comfort. Friedmans’ ANOVA tests were applied to 5-point Likert-style questions from the questionnaire, and paired t-tests were applied to the NASA-RTLX data.

### 6.1.2 Participants

Five commuter cyclists were recruited for the study, (16-24 years=5, 55-64 years=1). An additional participant was also recruited, however, the TactiHelm system did not work on their commutes; therefore, they were unable to provide any meaningful data. All participants were affiliated with the university to allow ease of communication due to the requirement of handling the equipment.

### 6.1.3 Apparatus

The full TactiHelm system was used for this study, as seen in Figure 2. Following analysis of the results from the previous study, the Wave Varying encoding scheme was used to encode the following distance of approaching vehicles. Preliminary testing was carried out by the researchers, to find the ideal threshold values at which to define the distance categories (as seen in Table 5). Whether or not these values are optimal, we seek to answer in this study.
The TactiHelm helmet was improved to have a more lightweight and robust design. The vents of the helmet were utilised to hold a smaller sized breadboard and the front actuator was moved closed to the front of the head to increase the space from the middle actuator. A rain-cover was also added, which would: a) protect the electronic components from rain, b) keep the components contained within the helmet, and c) improve the helmet’s perceived social acceptability among participants, by concealing the components, helping minimise any social discomfort.
As the controller application was compatible exclusively with Android devices, participants were provided with such a device, for the duration of the study, with the required ap-

11 plications already downloaded. Participants were additionally provided with a microphone to record the think-aloud, the Garmin Varia RTL515 bike radar, and a bike phoneholder, to hold the mobile device.

Distance Cue | Following Distance (ms)
Far | ≥3500
Near | >1500 and <3500
Imminent | ≤1500

Table 5: Table shows the following distance thresholds which define the three distance cues.

### 6.1.4 Procedure

Participants attended a briefing session where we explained the study’s purpose and how to use the provided equipment and associated software. We demonstrated how to turn on and off the helmet and bike radar, and how to use the Tacti-Helm Controller application to connect to them and to start receiving vibrations. We instructed participants to record their route using the ’Ride with GPS’ mobile application. If a participant stated they were not comfortable sharing their GPS data, they were instead asked to provide general information of their commute, such as its estimated distance and time to complete. Participants were also briefed on how to use the microphone and how to perform a think-aloud evaluation. We encouraged them to regularly articulate their thoughts out-loud and provided guidance on what to say, prompting them to describe what they see and feel. However, we instructed them not to concentrate too hard on the evaluation so as to not distract them, and to behave as they normally would. Participants were given the helmet to wear as we demonstrated the three possible cues they may feel. Additionally, they were provided with a user manual in case they forgot how to use the equipment and software. Participants were then tasked with recording two commutes - from their work to their residence and vice versa. They were trusted to keep the equipment overnight and return it the following day. Immediately following their second commute, they were prompted to complete the post-experiment questionnaire. Participants were then instructed to repeat their second commute, from their residence to their workplace, without the aid of TactiHelm. Following this, they were to complete the NASA-RTLX part of the questionnaire once more. A period of seven days was allotted for this task. Upon completion, they were fully debriefed. The study was approved by the University’s ethics committee.

## 6.2 Results

### 6.2.1 Quantitative Results

From the SUS questionnaire, participants gave an average system usability score of 73.5 (SD=5.76).
Table 6 presents the results for each factor in the NASA-TLX questionnaire, including the overall RTLX score. The scores for every dimension (except temporal demand) for the commute using TactiHelm were lower than the commute without TactiHelm, indicating a lesser workload. As the sample size was small, a Shapiro Wilk normality test was applied to the difference in each factor across the two conditions. The results of these tests indicated no evidence of non-normality across any of the factors (p>.05). Therefore, to investigate their significance, paired sample t-tests were performed on each factor. However, no statistically significant differences were found (p<.05).
Participants were asked to rate the perception of the three tactile actuators using a 5-point Likert scale. Applying the Friedman’s test revealed that there were no statistically significant differences in the perception of the Front (M =4.2, SD=0.84), Middle (M =4.4, SD=0.55), and Rear (M =4.0, SD=1.22) actuators; Chi-Square=0.43, p=.81. Mann-Whitney U-tests were performed to see whether these perception ratings significantly differ from those from the previous study. These tests revealed there were no significant improvement or decrease in perception of the Rear (U=44.0, p=.82), Middle (U=59.0, p=.40), or Front (U=62.5, p=.28) actuator.

### 6.2.2 Qualitative Comments and Observations

Cue Design and Delivery: Participants stated that they enjoyed the design of the cues, as the movement of the vibrations across the scalp helped portray the progression of an approaching vehicle, particularly on long stretches of roads, ”The cues really made the vehicle seem like it was approaching” [P2]. However, almost every participant stated that the far cues were often delivered too early, and the imminent cues were often delivered too late; specifically, the imminent cue was often delivered as the vehicle was overtaking, and usually immediately followed the near cue.
Usefulness of the Cues: Because of inaccurate delivery of the cues, many participants could not find the near cue was useful, as it was often masked by the imminent cue, despite the individual cues being reportedly easier to perceive and distinguish. This effect was further pronounced when on busier roads, where vehicles often transitioned back-andforth between a near and imminent distance, causing the helmet to repeatedly vibrate. Additionally, some participants reported being unable to tell which vehicle a cue was referring to on busier roads. Despite this, one participant stated that when the progression of a vehicle was slower, the cues were helpful for reminding them that the vehicle was still there, ”It was like an, ’I’m still here’, type of cue” [P1]. Despite these issues, many participants still expressed that the far cue was at least useful, not as indicator or distance, but as a way of first notifying them of the vehicle, particularly ones that they had not yet spotted, ”There were a few times it picked up cars I didn’t know were there” [P1]. Additionally, when delivered early, the imminent cue was also said to be useful for more immediate warnings.
Overall Usefulness: Three of the five participants stated that they found TactiHelm to be useful on their commute and could see themselves using it, or an improved version, again. Of the two who didn’t say this, they instead acknowledged that TactiHelm may have applications in accessibility and education. Particularly, participants expressed that a vibrotactile aid would help in conditions where it may be difficult to hear environmental noises, for example, the wind may make hearing difficult, or the user may be deaf or hardof-hearing. Additionally, it may help novice cyclists who are still learning and gaining confidence to cycle on the road, ”I might be good as an introduction to cycling on the road... it can point out things which they should be aware of” [P3]. Cognitive Effects: Although participants liked the design, some stated that the cues were often too intense, creating a worrying sense of urgency that the car might collide with them, ”It felt a little bit too urgent” [P2]. One participant

12

WITH TACTIHELM | WITHOUT TACTIHELM | t-tests
Factor | Mean | Median | SD | Min. | Max. | Mean | Median | SD | Min. | Max. | Stat | p
MD | 55.0 | 60.0 | 20.92 | 25.0 | 80.0 | 67.0 | 70.0 | 4.47 | 60.0 | 70.0 | -1.32 | 0.26
PD | 34.0 | 25.0 | 21.04 | 20.0 | 70.0 | 40.0 | 40.0 | 22.64 | 15.0 | 65.0 | -1.25 | 0.28
TD | 52.0 | 45.0 | 22.25 | 25.0 | 75.0 | 49.0 | 50.0 | 14.32 | 30.0 | 65.0 | 0.0 | 1.0
Per. | 23.0 | 20.0 | 17.89 | 5.0 | 50.0 | 23.0 | 25.0 | 20.19 | 0.0 | 45.0 | -1.45 | 0.22
Eff. | 52.0 | 50.0 | 26.12 | 20.0 | 85.0 | 51.0 | 50.0 | 2.24 | 50.0 | 55.0 | -0.30 | 0.78
Fru. | 39.0 | 40.0 | 29.03 | 5.0 | 70.0 | 41.0 | 35.0 | 24.85 | 10.0 | 75.0 | -0.57 | 0.60
RTLX | 42.5 | 35.83 | 17.67 | 21.67 | 65.83 | 45.17 | 48.33 | 5.51 | 36.67 | 49.17 | -0.73 | 0.51

Table 6: Comparison of NASA-RTLX stats for With TactiHelm and Without TactiHelm conditions (0 Very Low - 100 Very High).

who had taken part in the previous study stated, that despite the cues being easily perceptible and distinguishable, interpreting them often required more cognitive effort than when in the lab setting, ”In the lab-study I was actively feeling the vibrations, but this was more of a passive listening” [P3]. Additionally, participants expressed that it was useful that TactiHelm did not require having to look down at a mobile device or bike computer, allowing them to focus more on their surroundings.
Additional Comments: Multiple participants stated there was an initial novelty effect, where they significantly enjoyed receiving the vibrotactile alerts more in their first couple minutes of usage. P2 expressed their desire to have some form of test button on the controller application, to confirm that the helmet was indeed working before starting their journey. This comment’s significance is amplified by the fact that both P2 and P4 reported no longer receiving vibrations towards the end of their journey.

## 6.3 Discussion

The aim of this study was to evaluate the effectiveness our developed TactiHelm system in the real world. By asking commuter cyclists to use TactiHelm on their regular commutes, we used think-alouds, questionnaires, and interviews to gather both quantitative qualitative data, allowing us to answer our previously defined research questions.
RQ2.1 (effectiveness of our vibrotactile cues): Participants enjoyed the feeling created by the vibrotactile cues under the Wave Varying encoding scheme - finding it helpful in portraying the image of an approaching vehicle. Although perception of the actuators was rated highly, the inaccurate timing of the delivery of the cues caused far cues to be delivered too early and imminent cues to be delivered too late, leading to the temporal masking of near cues.
This inaccuracy was likely caused by a variety of issues. It is possible that our threshold values defining our distance categories (Table 5) were not optimally defined. The value of 1500ms defining when detected vehicles transition from near to imminent could be decreased to prevent the premature conveyance of an imminent cue and allowing more time between the delivery of the near and imminent cue. Additionally, to prevent the controller application and Arduino from being overwhelmed, we restricted the transfer of data from the bike radar to the controller to occur only every two seconds. In this time frame, it is likely that a vehicle may have transitioned between distance categories, causing the immediate delivery of a cue. Furthermore, there was a mixed response regarding whether participants enjoyed the length of the cue (Strongly Agree=3, Somewhat disagree=2).

Of those who disagreed, they stated that the 2000ms length of the imminent cue took was too long, and that a vehicle could have changed distance category by the time the cue was conveyed. Future work would improve the processing speed of the system to remove this delay. Finally, since the range of the radar was 140 metres, any vehicle within this range would be detected, causing an early conveyance of the far cue. To prevent this, a cap could be introduced to only deliver a cue if the vehicle is within a specified range, such as closer than 100 metres.
RQ2.2 (perceived safety): Our average SUS score of 73.5 is typically considered to be good [6] meaning the system was usable. Additionally, participants enjoyed having an extra aid which improved their perceived safety whilst keeping their visual senses free. However, the commutes where participants used TactiHelm showed no significant difference regarding workload compared to those without; although this study does give some initial insights into expected NASA-RTLX scores for cycling tasks. Notably, some participants stated the cues were often too intense, which differs from our results from the previous study where participants sometimes struggled to perceive vibrations. Although, it may be useful to create a sense of urgency in a hazard-notification system, such a system should not cause its users to worry. RQ2.3 (distance categories): Multiple participants stated that they did not find the near cue necessary; however, this sentiment is confounded due to the previously discussed poor delivery timing of the cues. Additionally, participants expressed difficulty knowing exactly which vehicle a cue was referring to. This may be because it was unclear that the terms far, near, and imminent referred to the following distance of a vehicle, which does not directly translate to the vehicles’ displacement from the cyclist. This unclear conveyance of information is an inherent disadvantage of using vibrotactile feedback, as it can contain less descriptive information compared to other modalities - assuming a level of interpretation on the cyclists’ part, which may vary depending on their perception and understanding of the stimuli. How this can be improved is explored in our Future Work.

## 7. CONCLUSIONS

This paper continued previous work from Vo et al. [76], to develop TactiHelm: a vibrotactile, helmet-based, hazard-notification system, which can effectively warn a cyclist of vehicles approaching from behind. We combined a commercial bike radar with a modified cycling helmet to detect approaching vehicle’s distance and speed and subsequently convey this to the cyclists’ head using tactile actuators placed along the sagittal midline of the helmet. This

13 design was informed by our conducted online survey, which confirmed cyclists’ desire for an easy to use safety system which can prevent potential collisions and injuries from other road vehicles.
Through a lab-based study we specifically defined the various parameters which compose a vibrotactile stimulus, rhythm, and cue, and investigated how these parameters effect tactile perception and interpretation on the scalp. We found that the sagittal plane of the scalp was a suitable location for vibrotactile stimulation. More so, results showed that encoding distance using the number of deliveries of a cue allows for significantly easier interpretation of distance, compared to using the pattern (location and delay) of a stimulus, due to the ability to infer a distance from the number of vibrations. Although, tactile patterns which utilise the sensory saltation illusion were more preferred by participants due to the sensation of movement it creates on the scalp.
Our final system was shown to be effective in real life, with participants in our real world user study reporting that they found the vibrotactile cues easily perceptible and helpful in portraying the image of an approaching vehicle. Additionally, results from the SUS questionnaire show that participants found the system usable. Despite the NASA-RTLX results showing that usage of TactiHelm caused no significant difference in workload for cycling, participants enjoyed that their visual senses could remain free. However, due to various reasons related to the implementation of the system, participants did not find the 3-level categorisation of distance information useful, preferring only the imminent and far cues.

## 7.1 Limitations and Future Work

From our studies, it is evident that TactiHelm has the potential to improve safety and information communication for cyclists. However, future work is needed before we can generalise these results to a wider population. We finalise this paper by outlining some potential areas which can be further explored and improved.
Stimulus Delivery: Although all participants in our studies had hair, we note that their hair density varied, possibly affecting the perception of vibrotactile stimuli. Additionally, due to the size and shape of the helmet, some participants’ heads did not make adequate contact with the actuators inside the helmet. An improved design may explore ways to consistently deliver these stimuli with the same amount of intensity. For example, the actuators could be woven into an adjustable lining, allowing a tighter fit to the scalp. Multimodal: As previously identified in our background research, it has been shown that delivering feedback multimodally leads to greater cue interpretation accuracy and shorter reaction time for cyclists. Therefore, future work may investigate how visual and auditory feedback can be best incorporated into the helmet. Furthermore, the combination of these three modalities allows for a wider vocabulary of alert messages. For example, vibrotactile feedback can be paired with audio cues to either reinforce the tactile information, reducing ambiguity in interpretation of the alert message, or provide additional details, enhancing the message clarity. This motivates the need for further research into the possible encoding parameters of these modalities, and how they can be used together to create a diverse range of warning messages.
Smartphone Integration: Usage of TactiHelm requires that the user already owns a bike radar compatible with the controller application. Although future work could improve the current system to be compatible with a variety of radars, this relies upon the assumption that the manufacturers do not make any changes to the hardware or software. Furthermore, the unit cost of these bike radars can be costly. A more suitable alternative may be to replace the bike radar with a vision-based vehicle-detection software running from a smartphone. Not only are modern smartphones ubiquitous, but they also have the processing power and camera quality needed to be able to accurately detect vehicles, meaning TactiHelm users are not required to buy an expensive bike radar. Exactly how this can be implemented is left to future work.
Feedback in Cardinal Directions: Although this paper places three tactile actuators on the midline of the scalp, the previous iteration of TactiHelm from which this paper continues, used four actuators around the circumference of the helmet, to indicate vehicles in each of the cardinal directions. Whether or not indicating a vehicle in-front is necessary, it is left to future work to explore the effectiveness of combining these two designs. This could be achieved using a nineactuator display, with two rows of four actuators around the circumference of the head, and an additional on the scalp’s central midpoint, mimicking our actuator setup in each cardinal direction. How perception varies across each linear configuration and how their activation affects each other is left to be investigated.
Tactile Patterns: This paper studied the concept of vibrotactile patterns - a combination of the location of a vibration, and the delay between each stimulus in the cue. Through our studies we showed the effectiveness of our Wave pattern, which utilises saltation to creating the sensation of movement across the scalp, helping to better portray the mental image of an approaching vehicle. This motivates the need to further explore how the location and delay affects the conveyance of hazard information and how additional vibration parameters can be altered to further refine this effect.

Acknowledgments. I would like to thank my supervisor, Stephen Brewster, for providing invaluable feedback and advice throughout the entirety of this project. I would like to thank my friends and family for their continual support. Lastly, I would like to thank all those who participated in our study, without whom this work would not have been possible.

## 8. REFERENCES

[1] D. Adminaite, R. Allsop, and G. Jost. Making walking and cycling on europe’s roads safer. 2015.
[2] D. Adminait´e-Fodor and G. Jost. How safe is walking and cycling in europe? pin flash report 38. 2020.
[3] Arduino.cc. Uno r3 arduino documentation. https://docs.arduino.cc/hardware/uno-rev3.
[4] R. A. Armstrong. When to use the bonferroni correction. Ophthalmic Physiol Opt, 34(5):502–508, Apr. 2014.
[5] A. Asif, W. Heuten, and S. Boll. Exploring distance encodings with a tactile display to convey turn by turn information in automobiles. In Proceedings of the 6th Nordic Conference on Human-Computer Interaction: Extending Boundaries, NordiCHI ’10,

14 page 32–41, New York, NY, USA, 2010. Association for Computing Machinery.
[6] A. Bangor, P. Kortum, and J. Miller. Determining what individual sus scores mean: adding an adjective rating scale. J. Usability Studies, 4(3):114–123, may 2009.
[7] A. Behnood and F. Mannering. Determinants of bicyclist injury severities in bicycle-vehicle crashes: A random parameters approach with heterogeneity in means and variances. Analytic Methods in Accident Research, 16:35–47, 2017.
[8] S. H. Berge, M. Hagenzieker, H. Farah, and
J. de Winter. Do cyclists need hmis in future automated traffic? an interview study. Transportation research part F: traffic psychology and behaviour, 84:33–52, 2022.
[9] C. Bertram, M. H. Evans, M. Javaid, T. Stafford, and
T. Prescott. Sensory augmentation with distal touch: The tactile helmet project. In N. F. Lepora, A. Mura,
H. G. Krapp, P. F. M. J. Verschure, and T. J. Prescott, editors, Biomimetic and Biohybrid Systems, pages 24–35, Berlin, Heidelberg, 2013. Springer Berlin Heidelberg.
[10] B. Bikes. smrtgrips. https://smrtgrips.com/.
[11] S. Brewster and L. M. Brown. Tactons: Structured tactile messages for non-visual information display. In Proceedings of the Fifth Conference on Australasian User Interface - Volume 28, AUIC ’04, page 15–23, AUS, 2004. Australian Computer Society, Inc.
[12] J. Brooke. Sus: A quick and dirty usability scale. Usability Eval. Ind., 189, 11 1995.
[13] C. M. Buth, N. Barbour, and M. Abdel-Aty. ¨ Effectiveness of bicycle helmets and injury prevention: a systematic review of meta-analyses. Scientific reports, 13(1):8540, 2023.
[14] M. B´ıl, M. B´ılov´a, and I. Muller. Critical factors in ¨ fatal collisions of adult cyclists with automobiles. Accident Analysis Prevention, 42(6):1632–1636, 2010.
[15] R. W. Cholewiak and A. A. Collins. The generation of vibrotactile patterns on a linear array: Influences of body site, time, and presentation mode. Perception & Psychophysics, 62:1220–1235, 2000.
[16] I. Cieslik, J. Kovaceva, M.-P. Bruyas, D. Large,
M. Kunert, S. Krebs, and M. Arbitmann. Improving the effectiveness of active safety systems to significantly reduce accidents with vulnerable road users-the project prospect (proactive safety for pedestrians and cyclists). 2019.
[17] E. Commission, D.-G. for Mobility, Transport,
H. Essen, D. Fiorello, K. El Beyrouty, C. Bieler,
L. Wijngaarden, A. Schroten, R. Parolin,
M. Brambilla, D. Sutter, S. Maffii, and F. Fermi. Handbook on the external costs of transport – Version 2019 – 1.1. Publications Office, 2020.
[18] M. De Angelis, V. M. Puchades, F. Fraboni,
L. Pietrantoni, and G. Prati. Negative attitudes towards cyclists influence the acceptance of an in-vehicle cyclist detection system. Transportation Research Part F: Traffic Psychology and Behaviour, 49:244–256, 2017.
[19] V. A. de Jesus Oliveira, L. Nedel, A. Maciel, and
L. Brayda. Spatial discrimination of vibrotactile stimuli around the head. In 2016 IEEE Haptics Symposium (HAPTICS), pages 1–6, 2016.
[20] D. de Waard, K. Edlinger, and K. Brookhuis. Effects of listening to music, and of using a handheld and handsfree telephone on cycling behaviour. Transportation Research Part F: Traffic Psychology and Behaviour, 14(6):626–637, 2011. Special Issue: Driving Simulation in Traffic Psychology.
[21] J. Edworthy and E. Hellier. Auditory warnings in noisy environments. Noise and Health, 2(6):27–39, 2000.
[22] U. Electronic. Hc-06 bluetooth module: Pinout, datasheet pdf and arduino connection. https://www.utmel.com/components/hc-06-bluetoothmodule-pinout-datasheet-pdf-and-arduinoconnection?id=884. (https://www.utmel.com/components/hc-06-bluetooth-module-pinout-datasheet-pdf-and-arduino-connection?id=884)
[23] J. S. Elke-Henriette Erdei and C. Hagemeister. Which signal modalities do cyclists prefer based on experiences in road traffic? Traffic Injury Prevention, 22(8):640–645, 2021. PMID: 34709941.
[24] E.-H. Erdei, J. Steinmann, and C. Hagemeister. Comparing perception of signals in different modalities during the cycling task: A field study. Transportation research part F: traffic psychology and behaviour, 73:259–270, 2020.
[25] J. Erp. Guidelines for the use of vibro-tactile displays in human computer interaction. Proceedings of Eurohaptics, 2002, 01 2002.
[26] J. B. F. V. Erp, H. A. H. C. V. Veen, C. Jansen, and
T. Dobbins. Waypoint navigation with a vibrotactile waist belt. ACM Trans. Appl. Percept., 2(2):106–117, apr 2005.
[27] E. P. Gardner and W. A. Spencer. Sensory funneling. ii. cortical neuronal representation of patterned cutaneous stimuli. Journal of Neurophysiology, 35(6):954–977, 1972.
[28] Garmin. Garmin varia rtl515. https://www.garmin.com/en-GB/p/698001.
[29] F. A. Geldard. Sensory saltation: Metastability in the perceptual world. Lawrence Erlbaum, 1975.
[30] K. Gilliland and R. E. Schlegel. Tactile stimulation of the human head for information display. Human Factors, 36(4):700–717, 1994.
[31] C. Goldenbeld, M. Houtenbos, E. Ehlers, and D. De Waard. The use and risk of portable electronic devices while cycling among different age groups. Journal of Safety Research, 43(1):1–8, 2012.
[32] S. G. Hart. Nasa-task load index (nasa-tlx); 20 years later. Proceedings of the Human Factors and Ergonomics Society Annual Meeting, 50(9):904–908, 2006.
[33] N. Highways. National highway urges
drivers to use the new two-second rule in new campaign. https://www.gov.uk/government/news/nationalhighwaysurges-drivers-to-use-the-two-second-rule-in-newcampaign, (https://www.gov.uk/government/news/nationalhighways-urges-drivers-to-use-the-two-second-rule-in-new-campaign) 2022.
[34] W. Hochleitner, D. Sellitsch, D. Rammer,
A. Aschauer, E. Mattheiss, G. Regal, and M. Tscheligi. No need to stop: Exploring smartphone interaction paradigms while cycling. In Proceedings of the 16th International Conference on Mobile and Ubiquitous Multimedia, MUM ’17, page 177–187, New York, NY,

15

USA, 2017. Association for Computing Machinery.
[35] A. D. Horowitz and T. A. Dingus. Warning signal design: A key human factors issue in an in-vehicle front-to-rear-end collision warning system. Proceedings of the Human Factors Society Annual Meeting, 36(13):1011–1013, 1992.
[36] A. Hoye. Recommend or mandate? a systematic review and meta-analysis of the effects of mandatory bicycle helmet legislation. Accident Analysis Prevention, 120:239–249, 2018.
[37] S.-S. Huang, C.-J. Chen, P.-Y. Hsiao, and L.-C. Fu. On-board vision system for lane recognition and front-vehicle detection to enhance driver’s awareness. In IEEE International Conference on Robotics and Automation, 2004. Proceedings. ICRA ’04. 2004, volume 3, pages 2456–2461 Vol.3, 2004.
[38] A. Høye. Bicycle helmets – to wear or not to wear? a meta-analyses of the effects of bicycle helmets on injuries. Accident Analysis Prevention, 117:85–97, 2018.
[39] N. C. Institute. Anatomical terminology. https://training.seer.cancer.gov/anatomy/body/terminology.html. (https://training.seer.cancer.gov/anatomy/body/terminology.html)
[40] M. Jenkins, D. Duggan, and A. Negri. Towards a connected bicycle to communicate with vehicles and infrastructure : Multimodel alerting interface with networked short-range transmissions (main-st). In 2017 IEEE Conference on Cognitive and Computational Aspects of Situation Management (CogSIMA), pages 1–3, 2017.
[41] A. Joshi, S. Kale, S. Chandel, and D. K. Pal. Likert scale: Explored and explained. British journal of applied science & technology, 7(4):396–403, 2015.
[42] D. S. B. Kart. Pulse width modulation. 2001.
[43] A.-M. Krauß, D. Wittchen, D. Kammer, and
G. Freitag. A head-based vibrotactile compass for cyclists. Mensch und Computer 2021-Workshopband, 2021.
[44] D. Langer and T. Jochem. Fusing radar and vision for detecting, classifying and avoiding roadway obstacles. In Proceedings of Conference on Intelligent Vehicles, pages 333–338, 1996.
[45] S. J. Lederman and L. A. Jones. Tactile and haptic illusions. IEEE Transactions on Haptics, 4(4):273–294, 2011.
[46] H. J. Lee, J. Lee, C. J. Kim, G. J. Kim, E.-S. Kim, and M. Whang. Brain process for perception of the “out of the body” tactile illusion for virtual object interaction. Sensors, 15(4):7913–7932, 2015.
[47] A. K. Low, Z. A. Zook, J. J. Fleck, and M. K. O’Malley. Effects of interfering cue separation distance and amplitude on the haptic detection of skin stretch. IEEE Transactions on Haptics, 14(2):254–259, 2021.
[48] I. Lujic, V. D. Maio, K. Pollhammer, I. Bodrozic,
J. Lasic, and I. Brandic. Increasing traffic safety with real-time edge analytics and 5g. In Proceedings of the 4th International Workshop on Edge Systems, Analytics and Networking, EdgeSys ’21, page 19–24, New York, NY, USA, 2021. Association for Computing Machinery.
[49] V. M. P. G. P. Marco De Angelis, Federico Fraboni and L. Pietrantoni. Use of smartphone and crash risk among cyclists. Journal of Transportation Safety & Security, 12(1):178–193, 2020.
[50] A. Matviienko, S. Ananthanarayan, S. S. Borojeni,
Y. Feld, W. Heuten, and S. Boll. Augmenting bicycles and helmets with multimodal warnings for children. In Proceedings of the 20th International Conference on Human-Computer Interaction with Mobile Devices and Services, MobileHCI ’18, New York, NY, USA, 2018. Association for Computing Machinery.
[51] A. Matviienko, S. Ananthanarayan, A. El Ali,
W. Heuten, and S. Boll. Navibike: Comparing unimodal navigation cues for child cyclists. In Proceedings of the 2019 CHI Conference on Human Factors in Computing Systems, CHI ’19, page 1–12, New York, NY, USA, 2019. Association for Computing Machinery.
[52] K. R. May and B. N. Walker. The effects of distractor sounds presented through bone conduction headphones on the localization of critical environmental sounds. Applied ergonomics, 61:144–158, 2017.
[53] T. L. McDaniel, S. Krishna, D. Colbry, and
S. Panchanathan. Using tactile rhythm to convey interpersonal distances to individuals who are blind. In CHI ’09 Extended Abstracts on Human Factors in Computing Systems, CHI EA ’09, page 4669–4674, New York, NY, USA, 2009. Association for Computing Machinery.
[54] J. L. Mwakalonge, J. White, and S. Siuhi. Distracted biking: a review of the current state-of-knowledge. International Journal of Traffic and Transportation Engineering, 3(2):42–51, 2014.
[55] K. Myles and J. Kalb. Guidelines for head tactile communication. page 34, 03 2010.
[56] K. Myles, J. T. Kalb, J. Lowery, and B. P. Kattel. The effect of hair density on the coupling between the tactor and the skin of the human head. Applied Ergonomics, 48:177–185, 2015.
[57] J. Olivier and P. Creighton. Bicycle injuries and helmet use: a systematic review and meta-analysis. International Journal of Epidemiology, 46(1):278–292, 07 2016.
[58] W. H. Organization. Global status report on road safety 2018. World Health Organization, 2018.
[59] M. O’Connor. Ban cyclists and e-scooter riders using phones, tory peer urges.
https://www.bbc.co.uk/news/uk-politics-61018584, 2022.
[60] T. Peeters, E. Van Breda, W. Saeys, E. Schaerlaken,
J. Vleugels, S. Truijen, and S. Verwulgen. Vibrotactile feedback during physical exercise: perception of vibrotactile cues in cycling. International Journal of Sports Medicine, 40(06):390–396, 2019.
[61] M. Pielot, O. Krull, and S. Boll. Where is my team: Supporting situation awareness with tactile displays. In Proceedings of the SIGCHI Conference on Human Factors in Computing Systems, CHI ’10, page 1705–1714, New York, NY, USA, 2010. Association for Computing Machinery.
[62] M. Pielot, B. Poppinga, W. Heuten, and S. Boll. Tacticycle: Supporting exploratory bicycle trips. In Proceedings of the 14th International Conference on Human-Computer Interaction with Mobile Devices and

16

Services, MobileHCI ’12, page 369–378, New York, NY, USA, 2012. Association for Computing Machinery.
[63] M. Porcheron, L. Clark, S. A. Nicholson, and
M. Jones. Cyclists’ use of technology while on their bike. In Proceedings of the 2023 CHI Conference on Human Factors in Computing Systems, CHI ’23, New York, NY, USA, 2023. Association for Computing Machinery.
[64] M. Prasad, P. Taele, D. Goldberg, and T. A. Hammond. Haptimoto: Turn-by-turn haptic route guidance interface for motorcyclists. In Proceedings of the SIGCHI Conference on Human Factors in Computing Systems, CHI ’14, page 3597–3606, New York, NY, USA, 2014. Association for Computing Machinery.
[65] Samsara. Following distance: How to coach cmv drivers and decrease tailgating. https://www.samsara.com/guides/following-distance/, 2021.
[66] J. Scholliers, D. Bell, A. Morris, and A. B. Garcia-Melendez. Potential of its to improve safety and mobility of vrus. 2014.
[67] J. Scholliers, D. Bell, A. Morris, and A. B. Garcia-Melendez. Potential of ITS to improve safety and mobility of VRUs. 6 2017.
[68] A. Silla, L. Leden, P. R¨am¨a, J. Scholliers, M. Van Noort, and D. Bell. Can cyclist safety be improved with intelligent transport systems? Accident Analysis Prevention, 105:134–145, 2017. Improving cyclist safety through scientific research, ICSC2015.
[69] R. Spector. Visual Fields, chapter 116, pages In Clinical Methods: The History, Physical, and Laboratory Examinations. Butterworths, Boston, 3 edition, 1990.
[70] H. Steltenpohl and A. Bouwer. Vibrobelt: Tactile navigation support for cyclists. In Proceedings of the 2013 International Conference on Intelligent User Interfaces, IUI ’13, page 417–426, New York, NY, USA, 2013. Association for Computing Machinery.
[71] M. Straub, A. Riener, and A. Ferscha. Distance encoding in vibro-tactile guidance cues. In 2009 6th Annual International Mobile and Ubiquitous Systems: Networking Services, MobiQuitous, pages 1–2, 2009.
[72] E. H. Strohaeker, A. Moia, J. Steinmann, and
C. Hagemeister. How do warnings influence cyclists’ reaction to conflicts? comparing acoustic and vibro-tactile warnings in different conflicts on a test track. Transportation Research Part F: Traffic Psychology and Behaviour, 90:151–166, 2022.
[73] R. F. Susan A. Shaheen. Intelligent transportation systems. Encyclopedia of Energy, pages 487–496, 2004.
[74] J. van Erp. Vibrotactile spatial acuity on the torso: effects of location and timing parameters. In First Joint Eurohaptics Conference and Symposium on Haptic Interfaces for Virtual Environment and Teleoperator Systems. World Haptics Conference, pages 80–85, March 2005.
[75] J. B. F. van Erp and P. J. Werkhoven. Vibro-tactile and visual asynchronies: Sensitivity and consistency. Perception, 33(1):103–111, 2004. PMID: 15035332.
[76] D.-B. Vo, J. Saari, and S. Brewster. Tactihelm: Tactile feedback in a cycling helmet for collision avoidance. In Extended Abstracts of the 2021 CHI Conference on Human Factors in Computing Systems, CHI EA ’21, New York, NY, USA, 2021. Association for Computing Machinery.
[77] T. von Sawitzky, T. Grauschopf, and A. Riener. Hazard notifications for cyclists: Comparison of awareness message modalities in a mixed reality study. In 27th International Conference on Intelligent User Interfaces, IUI ’22, page 310–322, New York, NY, USA, 2022. Association for Computing Machinery.
[78] T. von Sawitzky, T. Grauschopf, and A. Riener. ldquo;attention! a door could open.rdquo;mdash;introducing awareness messages for cyclists to safely evade potential hazards. Multimodal Technologies and Interaction, 6(1), 2022.
[79] C. Wickens. Processing resources and attention, varieties of attention. R. Parasuraman and D. Davis, Eds. Academic Press, 1984.
[80] C. D. Wickens and Y. Liu. Codes and modalities in multiple resources: A success and a qualification. Human Factors, 30(5):599–616, 1988. PMID: 3220489.
[81] M. Wierda and K. A. Brookhuis. Analysis of cycling skill: A cognitive approach. Applied Cognitive Psychology, 5(2):113–122, 1991.
[82] E. S. Wolfe, S. S. Arabian, J. L. Breeze, and M. J. Salzler. Distracted biking: an observational study. Journal of trauma nursing: the official journal of the Society of Trauma Nurses, 23(2):65, 2016.
[83] Y. Yamauchi and A. Suzuki. Vibro-tactile notification in different environments for motorcyclists. no. c, pages 59–65, 2020.

17
