LewisTrundle/tactihelm-l5project/data/lab-study/Perception of Tactors.pdf

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

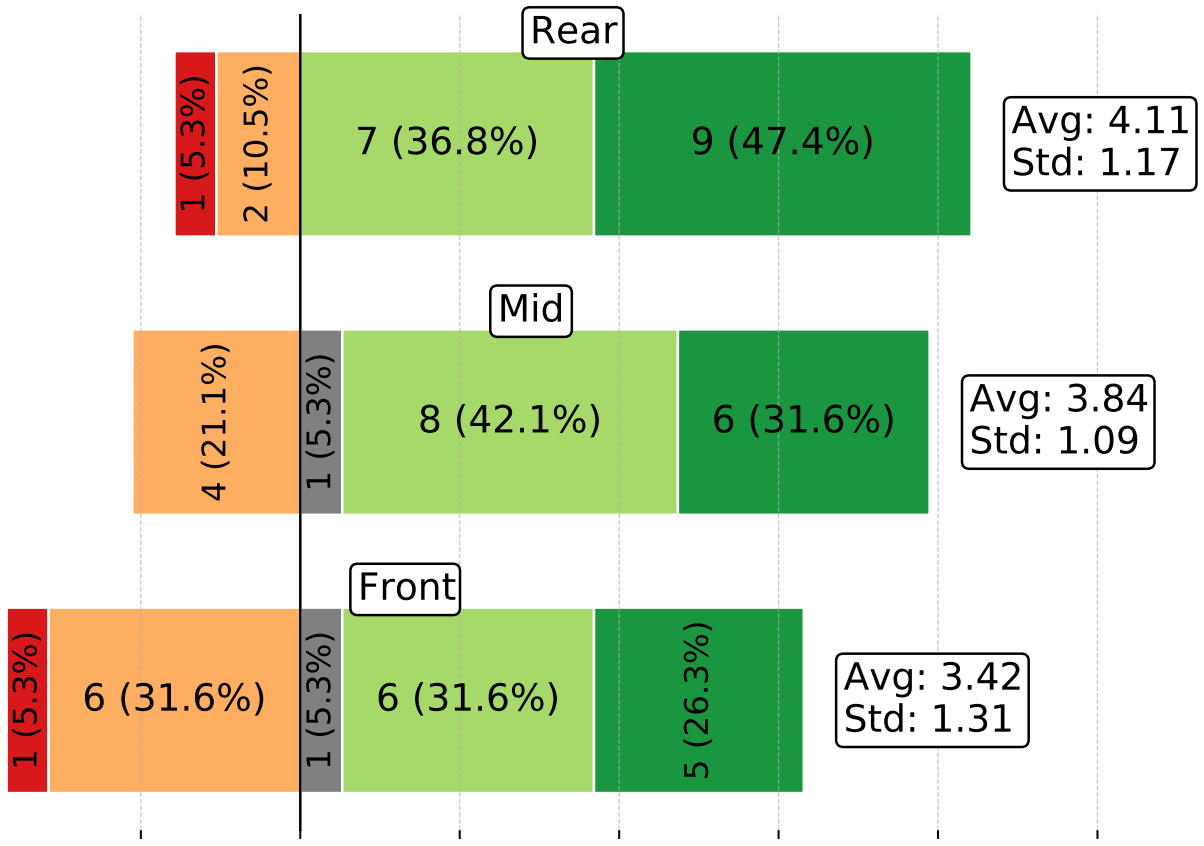
[picture p36: figure]
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
