LewisTrundle/tactihelm-l5project/dissertation/images/helmet-views.pdf

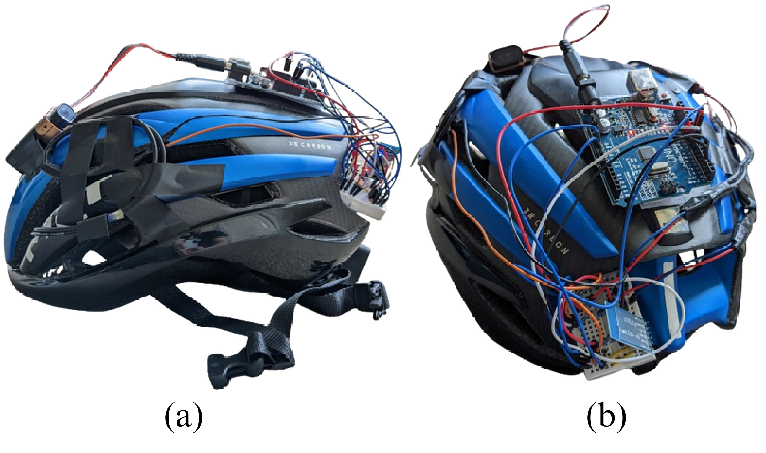
[picture p37: page 1]
