LewisTrundle/tactihelm-l5project/dissertation/images/helmets.pdf

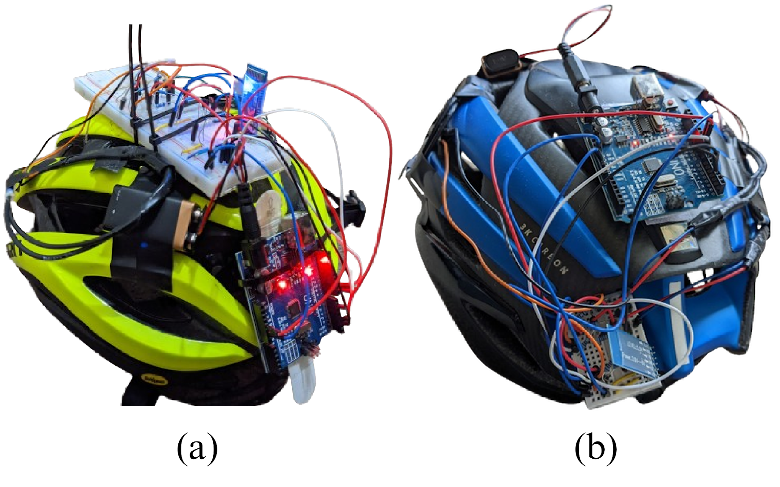
[picture p38: page 1]
