LewisTrundle/tactihelm-l5project/dissertation/images/Perception of Tactors.pdf

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

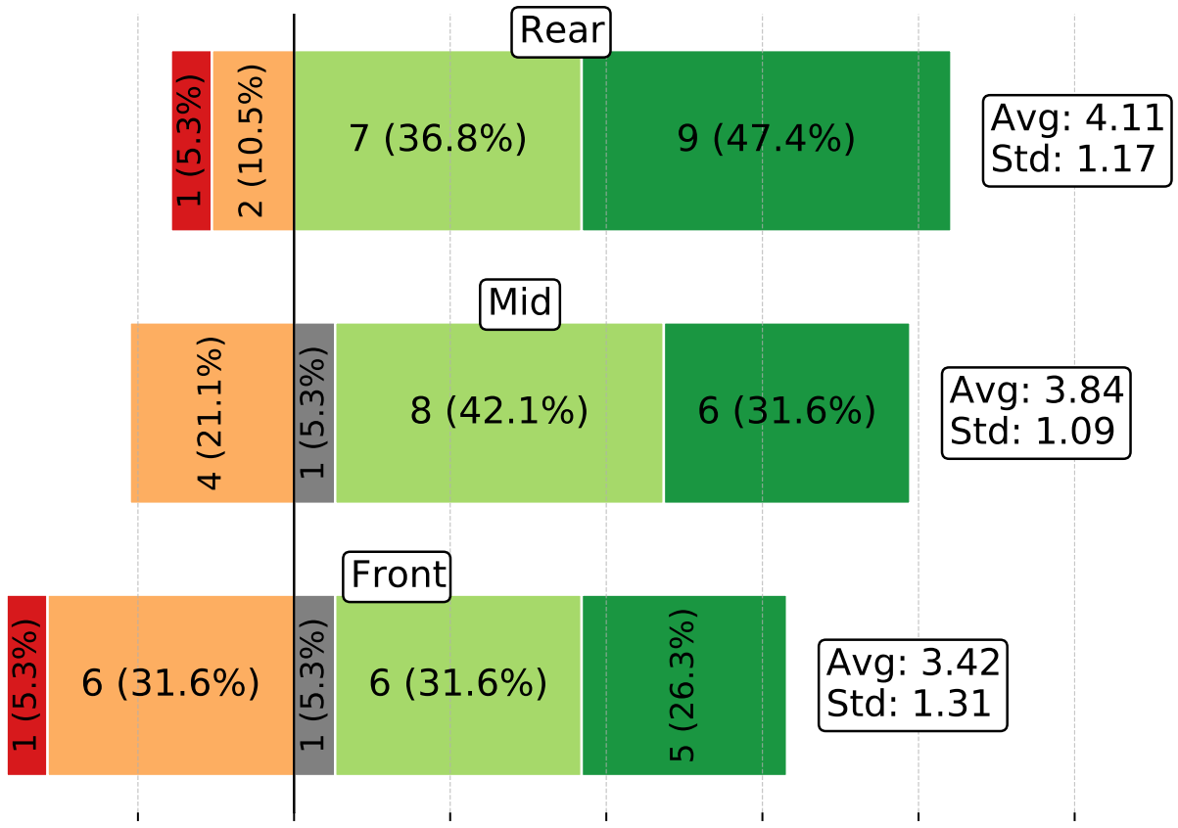
[picture p39: figure]
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
