LewisTrundle/tactihelm-l5project/dissertation/images/single-varying-example.pdf

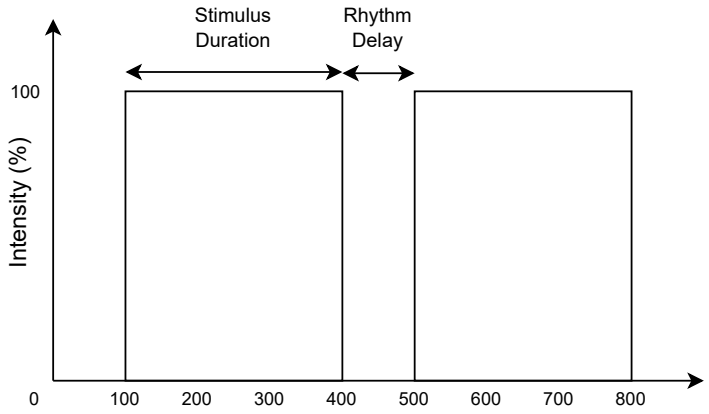
[picture p40: figure]
Stimulus Duration; Intensity (%); Rhythm Delay

## Time (ms)
