LewisTrundle/tactihelm-l5project/dissertation/images/tactor-placement.pdf

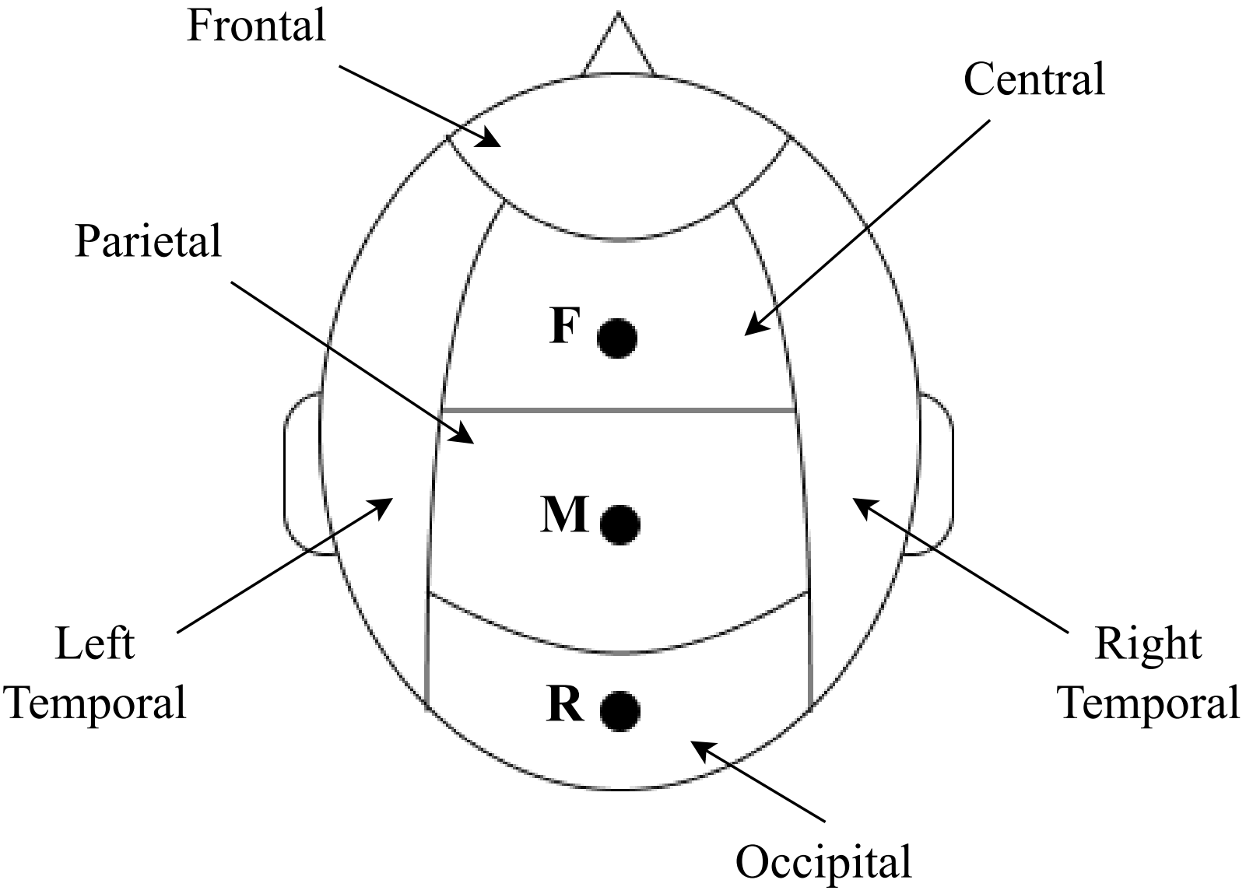
[picture p41: page 1]

Left
Temporal

Occipital

Parietal
F

M

R

Frontal

Right
Temporal

Central
