LewisTrundle/tactihelm-l5project/dissertation/images/wave-varying-example.pdf

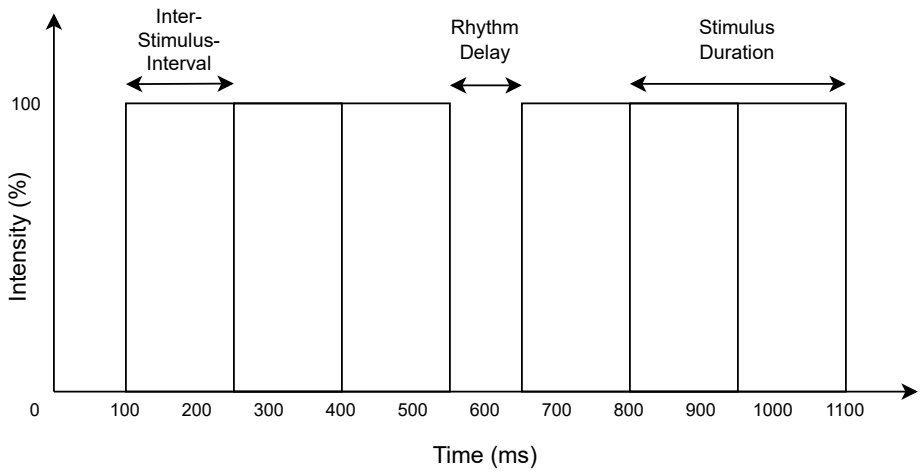
[picture p42: figure]
Inter- Stimulus- Interval; Intensity (%); Time (ms); Rhythm Delay; Stimulus Duration
