LewisTrundle/tactihelm-l5project/data/lab-study/Mean Correct by Encoding Scheme.pdf

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

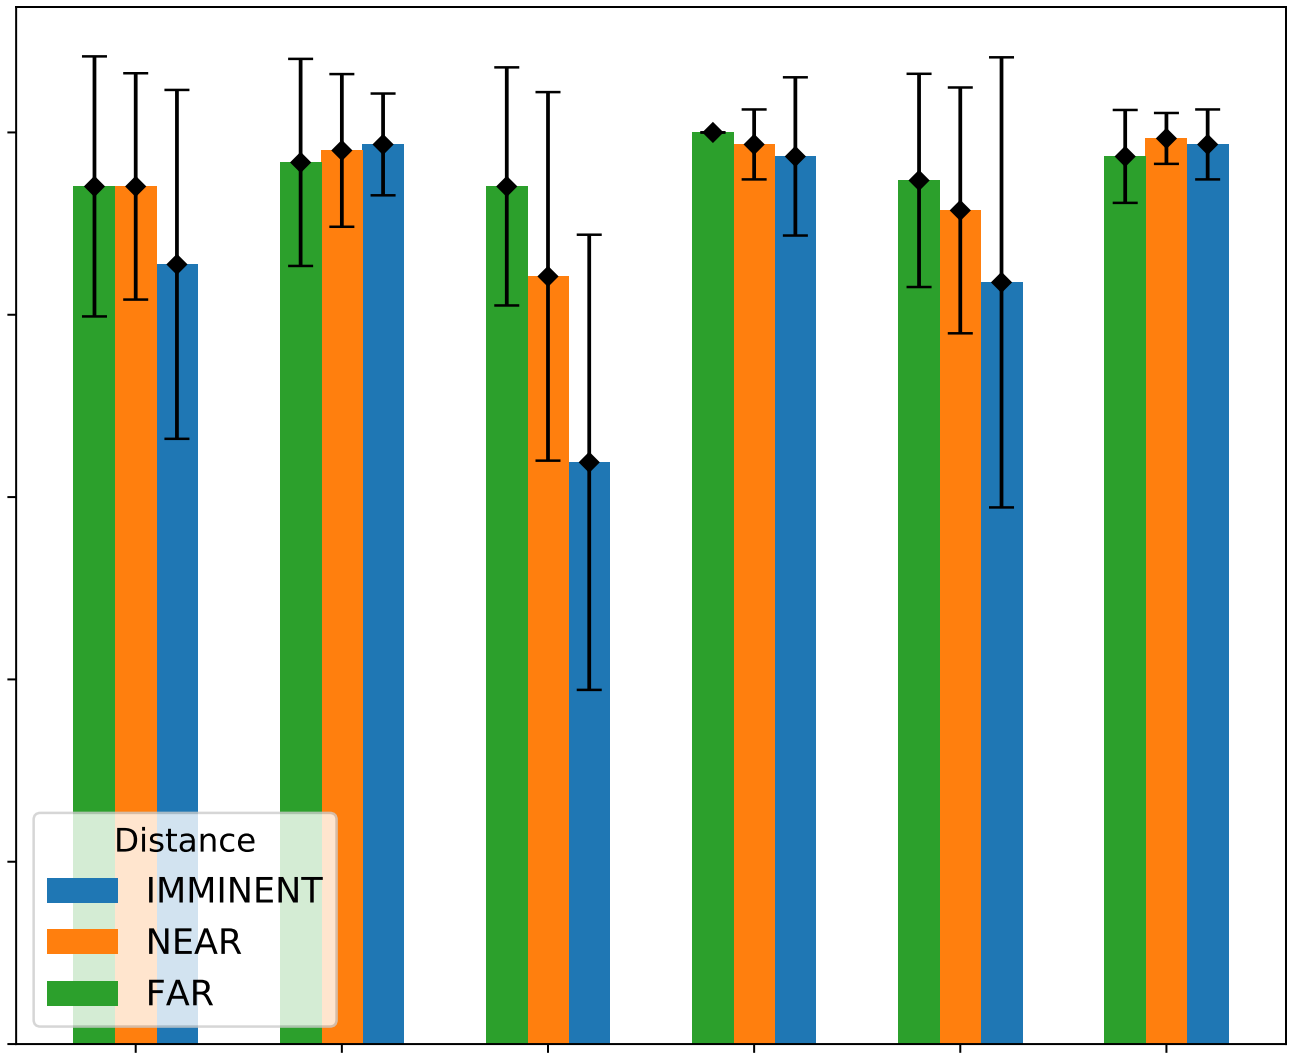
[picture p43: figure]
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
