LewisTrundle/tactihelm-l5project/dissertation/images/Mean Correct by Encoding Scheme.pdf

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
