LewisTrundle/tactihelm-l5project/dissertation/images/head-regions.pdf

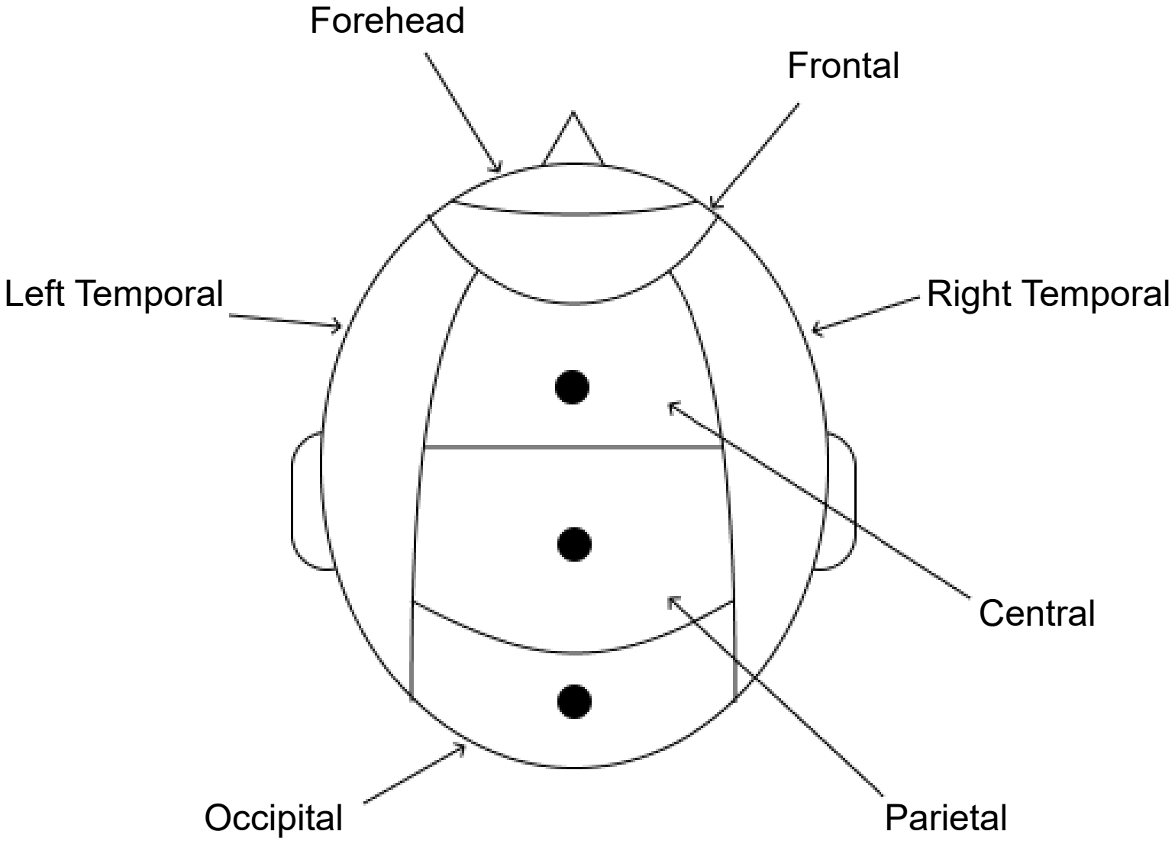
[picture p44: page 1]

Forehead
Frontal
Left Temporal | Right Temporal

Central

Occipital | Parietal
