LewisTrundle/tactihelm-l5project/data/user-study/survey-results.xlsx

Q7 | Q6 | Q3_1 | Q3_2 | Q3_3 | Q3_4 | Q3_5 | Q3_6 | Q8 | Q9 | Q10 | Q1_1 | Q1_2 | Q1_3 | Q1_4 | Q1_5 | Q1_6 | Q1_7 | Q1_8 | Q1_9 | Q1_10 | Q11_1 | Q11_2 | Q11_3 | Q11_4 | Q11_5 | Q11_6 | Q12 | Q16_1 | Q16_2 | Q16_3 | Q16_4 | Q16_5 | Q16_6 | Q17 | Q18_1 | Q19 | Q14
Please enter your participant number | Please select an option below to take you to the required sections. | The NASA Task Load Index (NASA-TLX) questionnaire is a subjective workload assessment tool, which provides respondents with an overall score regarding their mental, physical, and temporal demand, performance, effort, and frustration, in completing a task. Please carefully read each statement and rate it on a scale of 0 to 20. Each statement includes what a score of 0 or 20 means - please carefully read what each score means for each statement. Please only complete this section regarding your most recent commute. - Mental Demand: How much mental and perceptual activity was required to cycle your commute? 0 - it was very mentally easy, 20 - it was very mentally challenging. | The NASA Task Load Index (NASA-TLX) questionnaire is a subjective workload assessment tool, which provides respondents with an overall score regarding their mental, physical, and temporal demand, performance, effort, and frustration, in completing a task. Please carefully read each statement and rate it on a scale of 0 to 20. Each statement includes what a score of 0 or 20 means - please carefully read what each score means for each statement. Please only complete this section regarding your most recent commute. - Physical Demand: How much physical activity was required to cycle your commute? 0 - it was very physically easy, 20 - it was very physically challenging. | The NASA Task Load Index (NASA-TLX) questionnaire is a subjective workload assessment tool, which provides respondents with an overall score regarding their mental, physical, and temporal demand, performance, effort, and frustration, in completing a task. Please carefully read each statement and rate it on a scale of 0 to 20. Each statement includes what a score of 0 or 20 means - please carefully read what each score means for each statement. Please only complete this section regarding your most recent commute. - Temporal Demand: How much time pressure did you feel due to the rate of pace at which you cycled your normal commute? 0 - my normal pace felt slow and leisurely, 20 - my normal pace felt rapid and frantic. | The NASA Task Load Index (NASA-TLX) questionnaire is a subjective workload assessment tool, which provides respondents with an overall score regarding their mental, physical, and temporal demand, performance, effort, and frustration, in completing a task. Please carefully read each statement and rate it on a scale of 0 to 20. Each statement includes what a score of 0 or 20 means - please carefully read what each score means for each statement. Please only complete this section regarding your most recent commute. - Performance: How successful do you think you were in cycling your normal commute? 0 - I was very satisfied with my cycling performance, 20 - I was very unsatisfied with my cycling performance. | The NASA Task Load Index (NASA-TLX) questionnaire is a subjective workload assessment tool, which provides respondents with an overall score regarding their mental, physical, and temporal demand, performance, effort, and frustration, in completing a task. Please carefully read each statement and rate it on a scale of 0 to 20. Each statement includes what a score of 0 or 20 means - please carefully read what each score means for each statement. Please only complete this section regarding your most recent commute. - Effort: How hard did you have to work (mentally and physically) to accomplish your level of performance? 0 - it was not very hard, 20 - it was very hard. | The NASA Task Load Index (NASA-TLX) questionnaire is a subjective workload assessment tool, which provides respondents with an overall score regarding their mental, physical, and temporal demand, performance, effort, and frustration, in completing a task. Please carefully read each statement and rate it on a scale of 0 to 20. Each statement includes what a score of 0 or 20 means - please carefully read what each score means for each statement. Please only complete this section regarding your most recent commute. - Frustration: How irritated, stressed and annoyed, did you feel while cycling your normal commute? 0 - I felt very calm and relaxed, 20 - I felt very stressed and irritated. | Please enter your age | Please enter your gender | Have you ever been injured whilst cycling? | Please read each statement carefully and state how strongly you agree with the statement. - I think that I would like to use this system frequently. | Please read each statement carefully and state how strongly you agree with the statement. - I found the system unnecessarily complex. | Please read each statement carefully and state how strongly you agree with the statement. - I thought the system was easy to use. | Please read each statement carefully and state how strongly you agree with the statement. - I think that I would need the support of a technical person to be able to use this system. | Please read each statement carefully and state how strongly you agree with the statement. - I found the various functions in this system were well integrated. | Please read each statement carefully and state how strongly you agree with the statement. - I thought there was too much inconsistency in this system. | Please read each statement carefully and state how strongly you agree with the statement. - I would imagine that most people would learn to use this system very quickly. | Please read each statement carefully and state how strongly you agree with the statement. - I found the system very cumbersome to use. | Please read each statement carefully and state how strongly you agree with the statement. - I felt very confident using the system. | Please read each statement carefully and state how strongly you agree with the statement. - I needed to learn a lot of things before I could get going with this system. | Please state whether you agree with each of the following statements: - It was easy to feel vibrations from the front tactor | Please state whether you agree with each of the following statements: - It was easy to feel vibrations from the middle tactor | Please state whether you agree with each of the following statements: - It was easy to feel vibrations from the rear tactor | Please state whether you agree with each of the following statements: - It was easy to distinguish between the three types of vibrational cues (i.e. I could tell the difference between a far vibration and an imminent vibration). | Please state whether you agree with each of the following statements: - It was easy to interpet what a vibrational cue meant (i.e. when I felt a vibrational cue, I knew instantly what distance it was conveying). | Please state whether you agree with each of the following statements: - The vibrational cues were the perfect length (i.e. a vibration wasn't too long or too short). | Do you have any further comments regarding the perception, distinguishability, interpretation, or length of the vibrations? | Please state whether you agree with each of the following statements: - The vibrational cues were accurate (i.e. vehicles were where you would expect them to be from a vibrational cue) | Please state whether you agree with each of the following statements: - TactiHelm was reliable (i.e. it always detected and warned me of approaching vehicles) | Please state whether you agree with each of the following statements: - The vibrational cues were appropriate indicators of the proximity of an approaching vehicle (i.e. you knew what a 'far' or 'near' vehicle meant) | Please state whether you agree with each of the following statements: - The vibrational cues were delivered at appropriate times (i.e. not too often or too little) | Please state whether you agree with each of the following statements: - TactiHelm made me feel safer while cycling | Please state whether you agree with each of the following statements: - TactiHelm made me feel more alert of my surroundings while cycling | Do you have any further comments regarding the accuracy, reliability, and general effectiveness of TactiHelm in warning you of approaching vehicles? | Please rate how comfortable the helmet felt whilst on your head. | Do you have any further comments regarding the comfort of the helmet? | Do you have any further comments about TactiHelm, or suggestions for future improvements or additional features?
1 | I just completed my second commute using TactiHelm | 7 | 5 | 5 | 1 | 7 | 1 | 16 - 24 | Male | Yes - minor injury | Somewhat disagree | Strongly disagree | Strongly agree | Strongly disagree | Strongly agree | Somewhat disagree | Strongly agree | Strongly disagree | Strongly agree | Somewhat agree | Somewhat agree | Strongly agree | Strongly agree | Somewhat agree | Somewhat agree | Strongly agree |  | Somewhat agree | Strongly agree | Somewhat agree | Somewhat disagree | Somewhat agree | Somewhat agree |  | 10 | V2 is much more comfortable than V1
2 | I just completed my second commute using TactiHelm | 14 | 13 | 15 | 10 | 14 | 13 | 55 - 64 | Male | Yes - minor injury | Somewhat agree | Somewhat agree | Somewhat agree | Strongly disagree | Somewhat agree | Somewhat agree | Strongly agree | Strongly disagree | Somewhat agree | Strongly disagree | Strongly agree | Strongly agree | Somewhat agree | Neutral | Somewhat agree | Somewhat disagree | sometimes there was a lot of vibration when there were many cars around. this got a bit confusing at times. | Neutral | Neutral | Somewhat agree | Somewhat disagree | Somewhat agree | Somewhat agree | sometimes the feedback came late and the car had already passed me | 10
3 | I just completed my second commute using TactiHelm | 4 | 12 | 8 | 4 | 10 | 3 | 16 - 24 | Male | No | Strongly disagree | Strongly disagree | Strongly agree | Neutral | Somewhat agree | Somewhat agree | Somewhat agree | Strongly disagree | Neutral | Strongly disagree | Somewhat agree | Somewhat agree | Somewhat agree | Somewhat disagree | Strongly agree | Strongly agree |  | Somewhat agree | Somewhat disagree | Somewhat agree | Somewhat agree | Neutral | Somewhat disagree | Sometimes there were cars overtaking me that the system didn't recognise until they were directly beside me and then it went imminent | 6
3 | I just completed my normal commute without using TactiHelm | 4 | 13 | 10 | 5 | 10 | 2
4 | I just completed my normal commute without using TactiHelm | 3 | 14 | 6 | 9 | 11 | 15
4 | I just completed my second commute using TactiHelm | 4 | 16 | 9 | 6 | 17 | 14 | 16 - 24 | Male | Yes - minor injury | Somewhat agree | Somewhat disagree | Strongly agree | Somewhat disagree | Somewhat agree | Somewhat agree | Somewhat agree | Strongly disagree | Neutral | Neutral | Strongly agree | Somewhat agree | Somewhat disagree | Strongly agree | Somewhat agree | Somewhat disagree | really easy to pick up the meaning of each vibration | Somewhat agree | Neutral | Somewhat agree | Somewhat disagree | Somewhat agree | Somewhat agree |  | 4
1 | I just completed my normal commute without using TactiHelm | 12 | 14 | 8 | 0 | 10 | 7
6 | I just completed my normal commute without using TactiHelm | 8 | 14 | 13 | 8 | 10 | 6
6 | I just completed my second commute using TactiHelm | 5 | 9 | 15 | 2 | 4 | 8 | 16 - 24 | Male | Yes - minor injury | Somewhat agree | Somewhat disagree | Somewhat agree | Neutral | Strongly agree | Strongly disagree | Somewhat agree | Neutral | Neutral | Somewhat disagree | Neutral | Somewhat agree | Strongly agree | Somewhat agree | Somewhat agree | Strongly agree | The external factors (wind) effected the distinguishability of vibrations. | Somewhat agree | Somewhat disagree | Neutral | Neutral | Somewhat agree | Somewhat agree | I found TactiHelm most useful when there had been no cars following me and one suddenly appeared (often from far initially). The reliability was less so with a tail of cars, perhaps missing cars that were around 10 metres behind the car that was alerted as imminent when that further away car got closer. | 9 | The helmet was not more uncomfortable than a regular helmet. | I think I benefitted most from it noticing cars far away (cars I would need to turn nearly 180 degrees to notice). Perhaps a slimmer version of TactiHelm could be available meaning this was a smaller device on the helmet and could feel more comfortable/stable to cycle with.
2 | I just completed my normal commute without using TactiHelm | 13 | 12 | 12 | 1 | 10 | 11
