LewisTrundle/tactihelm-l5project/dissertation/images/overall-system.pdf

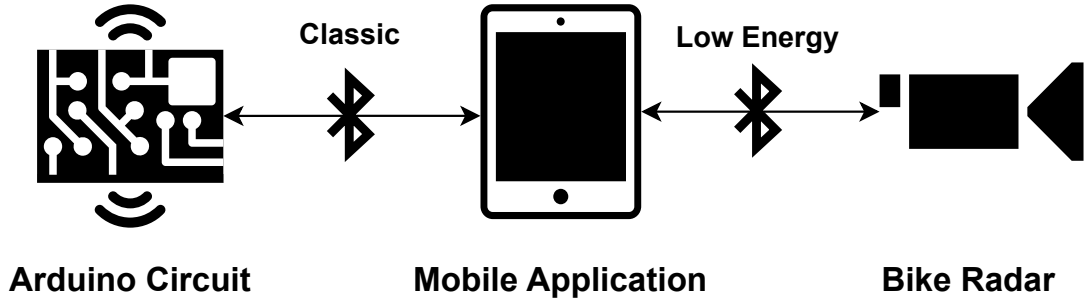
[picture p45: page 1]
Classic; Low Energy; Arduino Circuit; Mobile Application; Bike Radar
